modulolabs/pcb/Joystick/Joystick.csv

Qty | Value | Device | Package | Parts | Description | BOM | NOBOM | PARTNUM | VALUE
1 | .1uF | CAPACITOR-.1UF | 0603 | C1 | Capacitor |  |  | C0603C104K5RACTU | .1uF
1 | 1KΩ | RESISTOR-1KΩ | 0603 | R1 | Resistor |  |  | ERJ-3EKF1001V | 1KΩ
1 | ATTINY48/88-TQFP | ATTINY48/88-TQFP | TQFP-32 | U1 |  |  |  | ATTINY48-AUR
1 | DEVICE-PCB | DEVICE-PCB | DEVICE-PCB | PCB1 | Modulo Footprint |  | 1 | Joystick PCB
1 | HEADER-1X4-AMPMODU | HEADER-1X4-AMPMODU | AMPMODU-4P | JP1 |  |  |  | 147733-3
1 | JOYSTICK | JOYSTICK | JOYSTICK | U2 | Thumb Joystick |  |  | Joystick
1 | LED-1206-REV | LED-1206-REV | LED-1206-REV | LED1 | LED |  |  | LTST-C230TBKT
