modulolabs/pcb/Programmer/Programmer.brd

## EAGLE design Programmer/Programmer.brd (2015-08-15)

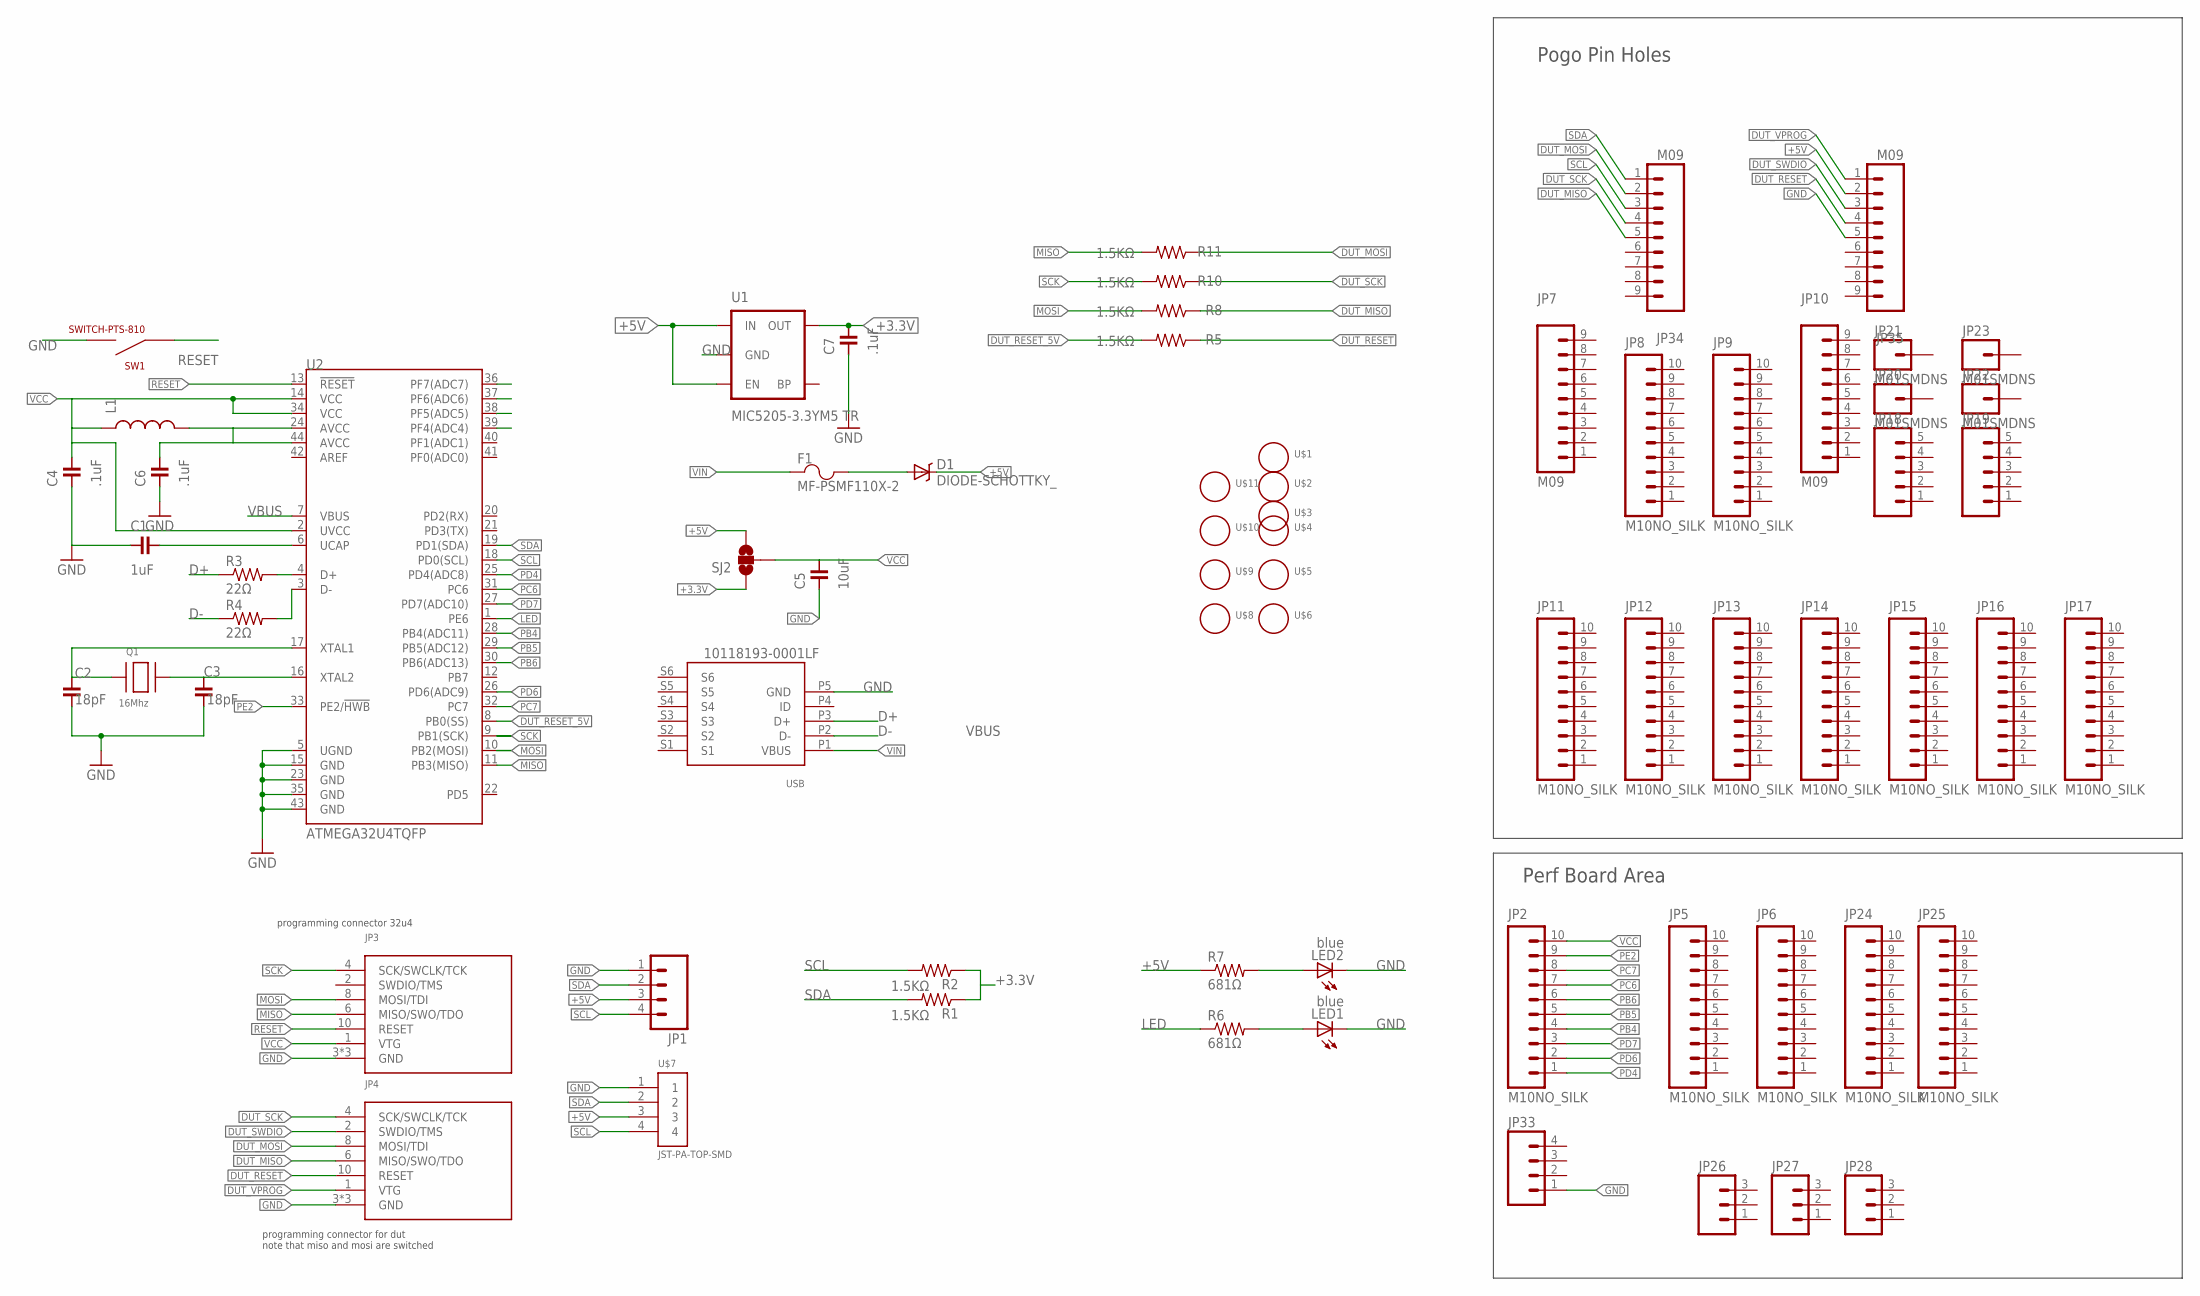
[picture p32: schematic Programmer.sch]

Parts:
C1: 1uF; 0603
C2, C3: 18pF; 0603
C4, C6, C7: .1uF; 0603
C5: 10uF; 0603
D1: DIODE-SCHOTTKY_; SMA-DIODE
F1: MF-PSMF110X-2; 0805; PARTNUM MF-PSFM110X-2
JP1: M04LOCK; 1X04_LOCK
JP2, JP5, JP6, JP8, JP9, JP11, JP12, JP13, JP14, JP15, JP16, JP17, JP24, JP25: M10NO_SILK; 1X10_NO_SILK
JP3, JP4: ICSP; 2X5-.05
JP7, JP10, JP34, JP35: M09; 1X09
JP18, JP19: M05NO_SILK; 1X05_NO_SILK
JP20, JP21, JP22, JP23: M01SMDNS; 1X01NS
JP26, JP27, JP28: M031X03_NO_SILK; 1X03_NO_SILK
JP33: M041X04_NO_SILK; 1X04_NO_SILK
L1: INDUCTOR0805; 0805
LED1, LED2: blue; 0805-LED
Q1: 16Mhz; NX3225; PARTNUM CX3225GB16000D0HEQCC
R1, R2, R5, R8, R10, R11: 1.5KΩ; 0603
R3, R4: 22Ω; 0603
R6, R7: 681Ω; 0603
SJ2: SOLDERJUMPER_2WAYPASTE1&2; SJ_3_PASTE1&2
SW1: SWITCH-PTS-810; TACT-SWITCH-PTS-810
U1: MIC5205-3.3YM5 TR; SOT23-5; PARTNUM MIC5205-3.3YM5 TR
U2: ATMEGA32U4TQFP; SPARKFUN-DIGITALIC_TQFP44; PARTNUM ATMEGA32U4TQFP
U3: USBFCI-MICROB; USB-MICROB-FCI; PARTNUM 10118193-0001LF
U$1, U$2, U$3, U$4, U$5, U$6, U$8, U$9, U$10, U$11: HOLE#2; HOLE-#2
U$7: JST-PA-TOP-SMD

Connections:
+3.3V: C7.1, R1.1, R2.1, SJ2.1, U1.5 (OUT)
+5V: D1.C, JP1.3, JP35.2, R7.1, SJ2.3, U1.1 (IN), U1.3 (EN), U$7.3
D+: R3.1, U3.P3 (D+)
D-: R4.1, U3.P2 (D-)
DUT_MISO: JP4.6 (MISO/SWO/TDO), JP34.5, R8.1
DUT_MOSI: JP4.8 (MOSI/TDI), JP34.2, R11.1
DUT_RESET: JP4.10 (RESET), JP35.4, R5.1
DUT_RESET_5V: R5.2, U2.8 (PB0(SS))
DUT_SCK: JP4.4 (SCK/SWCLK/TCK), JP34.4, R10.1
DUT_SWDIO: JP4.2 (SWDIO/TMS), JP35.3
DUT_VPROG: JP4.1 (VTG), JP35.1
GND: C1.2, C2.2, C3.2, C4.2, C5.2, C6.2, C7.2, JP1.1, JP3.3 (GND), JP3.5 (GND), JP3.9 (GND), JP4.3 (GND), JP4.5 (GND), JP4.9 (GND), JP33.1, JP35.5, LED1.C, LED2.C, SW1.P$3 (NEG1), SW1.P$4 (NEG1), U1.2 (GND), U2.5 (UGND), U2.15 (GND), U2.23 (GND), U2.35 (GND), U2.43 (GND), U3.P5 (GND), U$7.1
LED: R6.1, U2.1 (PE6)
MISO: JP3.6 (MISO/SWO/TDO), R11.2, U2.11 (PB3(MISO))
MOSI: JP3.8 (MOSI/TDI), R8.2, U2.10 (PB2(MOSI))
unnamed: C1.1, U2.6 (UCAP)
unnamed: C6.1, L1.2, U2.24 (AVCC), U2.44 (AVCC)
unnamed: C3.1, Q1.3 (X2), U2.16 (XTAL2)
unnamed: LED1.A, R6.2
unnamed: R3.2, U2.4 (D+)
unnamed: R4.2, U2.3 (D-)
unnamed: LED2.A, R7.2
unnamed: C2.1, Q1.1 (X1), U2.17 (XTAL1)
PB4: JP2.4, U2.28 (PB4(ADC11))
PB5: JP2.5, U2.29 (PB5(ADC12))
PB6: JP2.6, U2.30 (PB6(ADC13))
PC6: JP2.7, U2.31 (PC6)
PC7: JP2.8, U2.32 (PC7)
PD4: JP2.1, U2.25 (PD4(ADC8))
PD6: JP2.2, U2.26 (PD6(ADC9))
PD7: JP2.3, U2.27 (PD7(ADC10))
PE2: JP2.9, U2.33 (PE2/!HWB)
RESET: JP3.10 (RESET), SW1.P$1 (POS1), SW1.P$2 (POS1), U2.13 (!RESET)
SCK: JP3.4 (SCK/SWCLK/TCK), R10.2, U2.9 (PB1(SCK))
SCL: JP1.4, JP34.3, R2.2, U2.18 (PD0(SCL)), U$7.4
SDA: JP1.2, JP34.1, R1.2, U2.19 (PD1(SDA)), U$7.2
VBUS: D1.A, F1.2, U2.7 (VBUS)
VCC: C4.1, C5.1, JP2.10, JP3.1 (VTG), L1.1, SJ2.2, U2.2 (UVCC), U2.14 (VCC), U2.34 (VCC)
VIN: F1.1, U3.P1 (VBUS)

Notes on the sheet:
programming connector 32u4
programming connector for dut note that miso and mosi are switched
Pogo Pin Holes
Perf Board Area

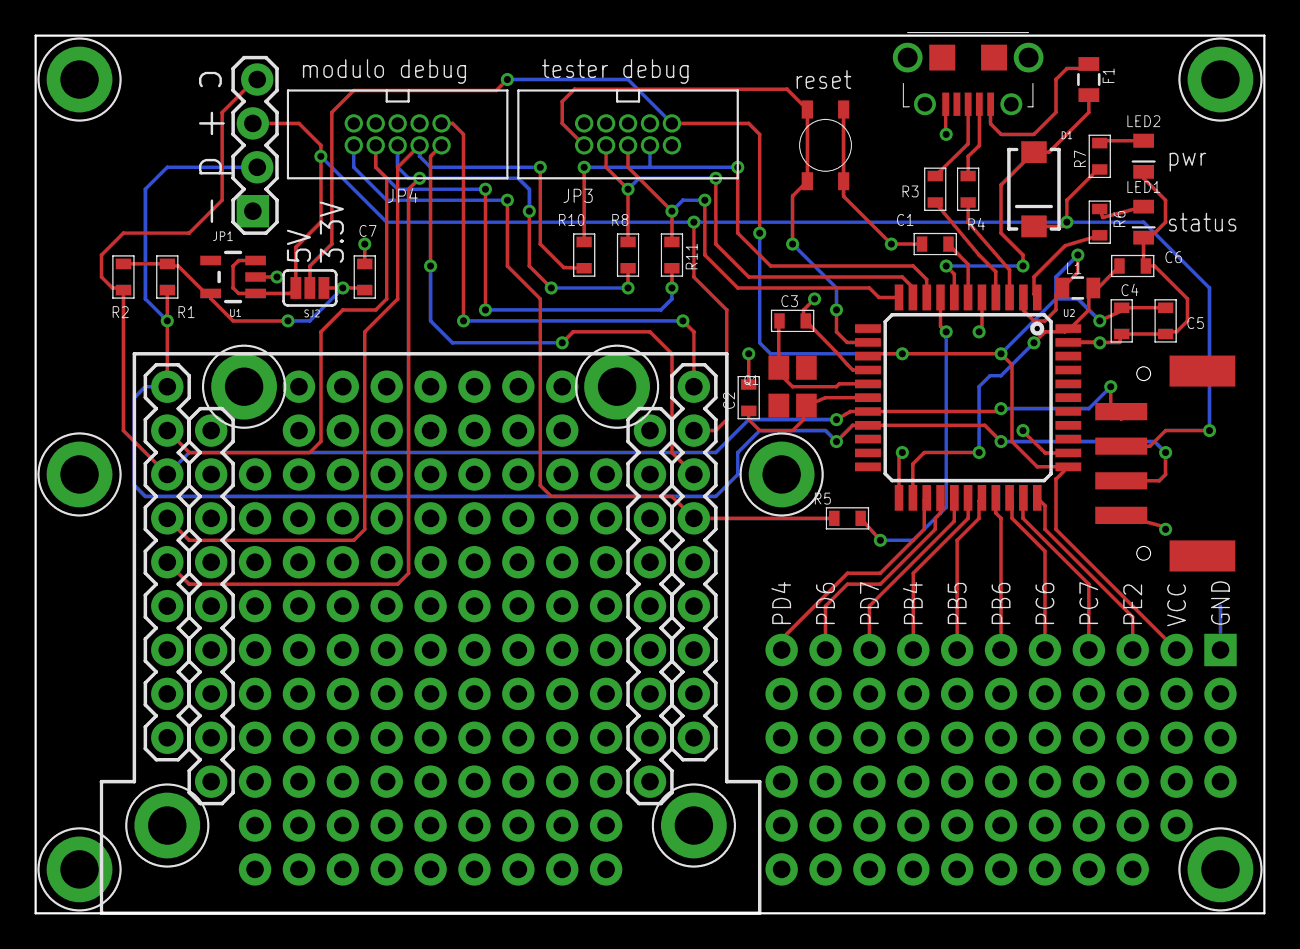
[picture p33: board Programmer.brd from above]

Board: 2 copper layers, 71.1 x 50.8 mm, 70 parts (0 on the bottom side), 39 nets.
