modulolabs/pcb/TempProbeProgrammer/TempProbeProgrammer.brd

## EAGLE design TempProbeProgrammer/TempProbeProgrammer.brd (2015-08-15)

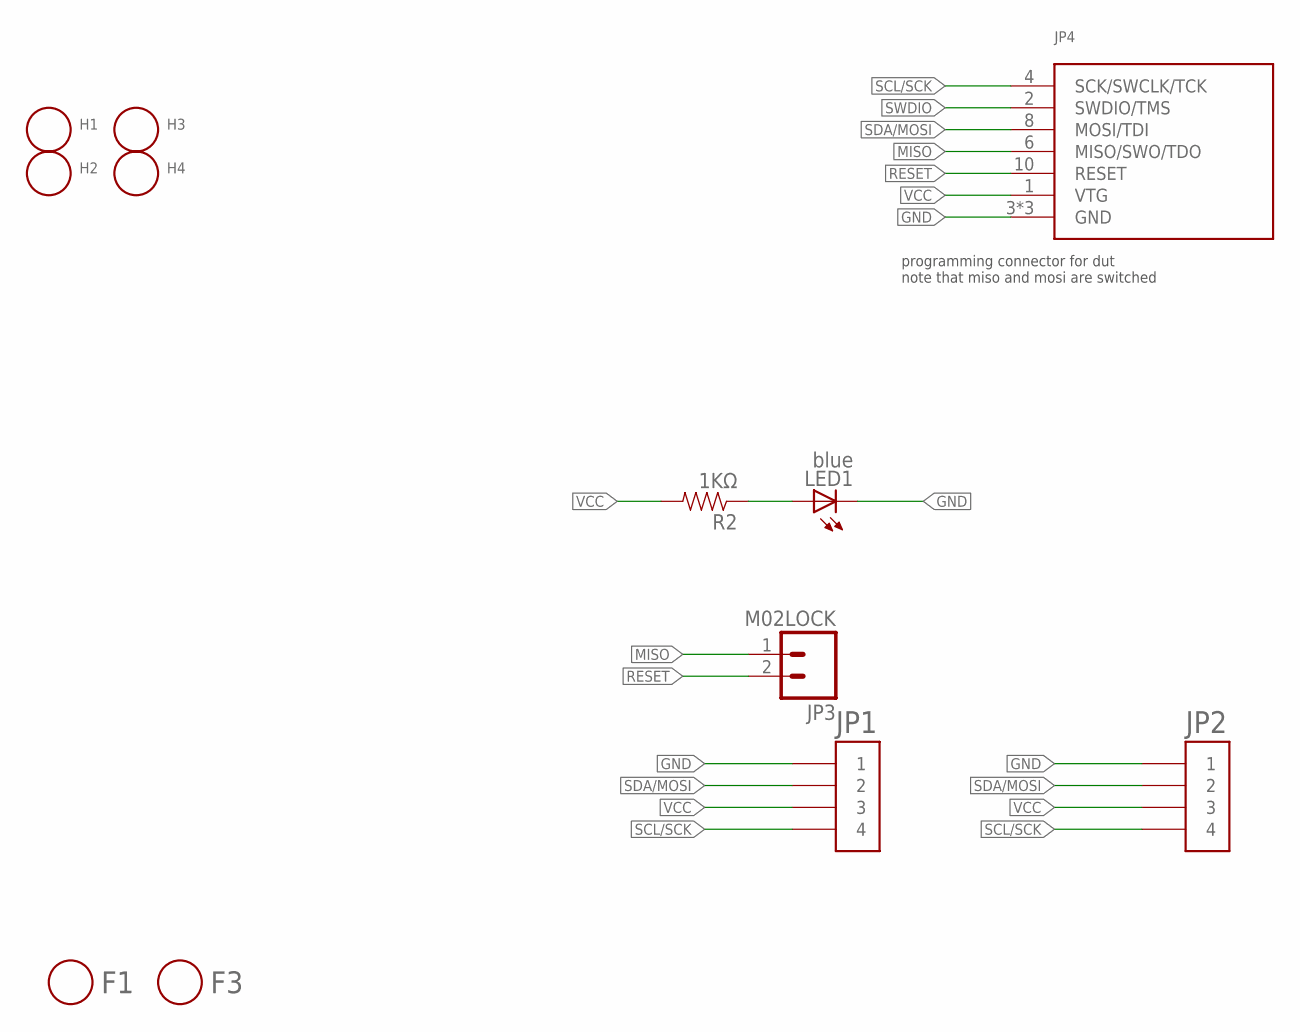
[picture p34: schematic TempProbeProgrammer.sch]

Parts:
F1, F3: FIDUCIAL; FIDUCIAL_1MM
H1, H2, H3, H4: HOLE#4; HOLE-#4
JP1, JP2: HEADER-1X4-JST-PA-SIDE-SMD; JST-PA-SIDE-SMD
JP3: M02LOCK; 1X02_LOCK; PARTNUM EXCLUDE
JP4: ICSP; 2X5-.05
LED1: blue; 0805-LED
R2: 1KΩ; 0603

Connections:
GND: JP1.1, JP2.1, JP4.3 (GND), JP4.5 (GND), JP4.9 (GND), LED1.C
MISO: JP3.1, JP4.6 (MISO/SWO/TDO)
unnamed: LED1.A, R2.1
RESET: JP3.2, JP4.10 (RESET)
SCL/SCK: JP1.4, JP2.4, JP4.4 (SCK/SWCLK/TCK)
SDA/MOSI: JP1.2, JP2.2, JP4.8 (MOSI/TDI)
SWDIO: JP4.2 (SWDIO/TMS)
VCC: JP1.3, JP2.3, JP4.1 (VTG), R2.2

Notes on the sheet:
programming connector for dut note that miso and mosi are switched

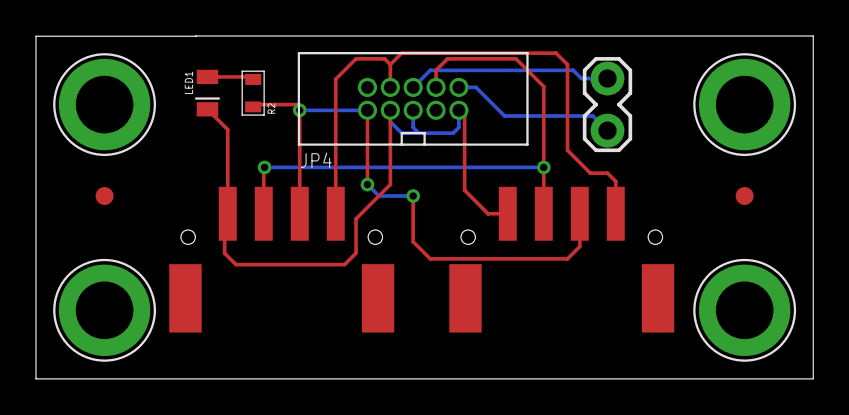
[picture p35: board TempProbeProgrammer.brd from above]

Board: 2 copper layers, 43.2 x 19.1 mm, 12 parts (0 on the bottom side), 7 nets.
