modulolabs/pcb/PerfBoard/PerfBoard.brd

## EAGLE design PerfBoard/PerfBoard.brd (2015-06-10)

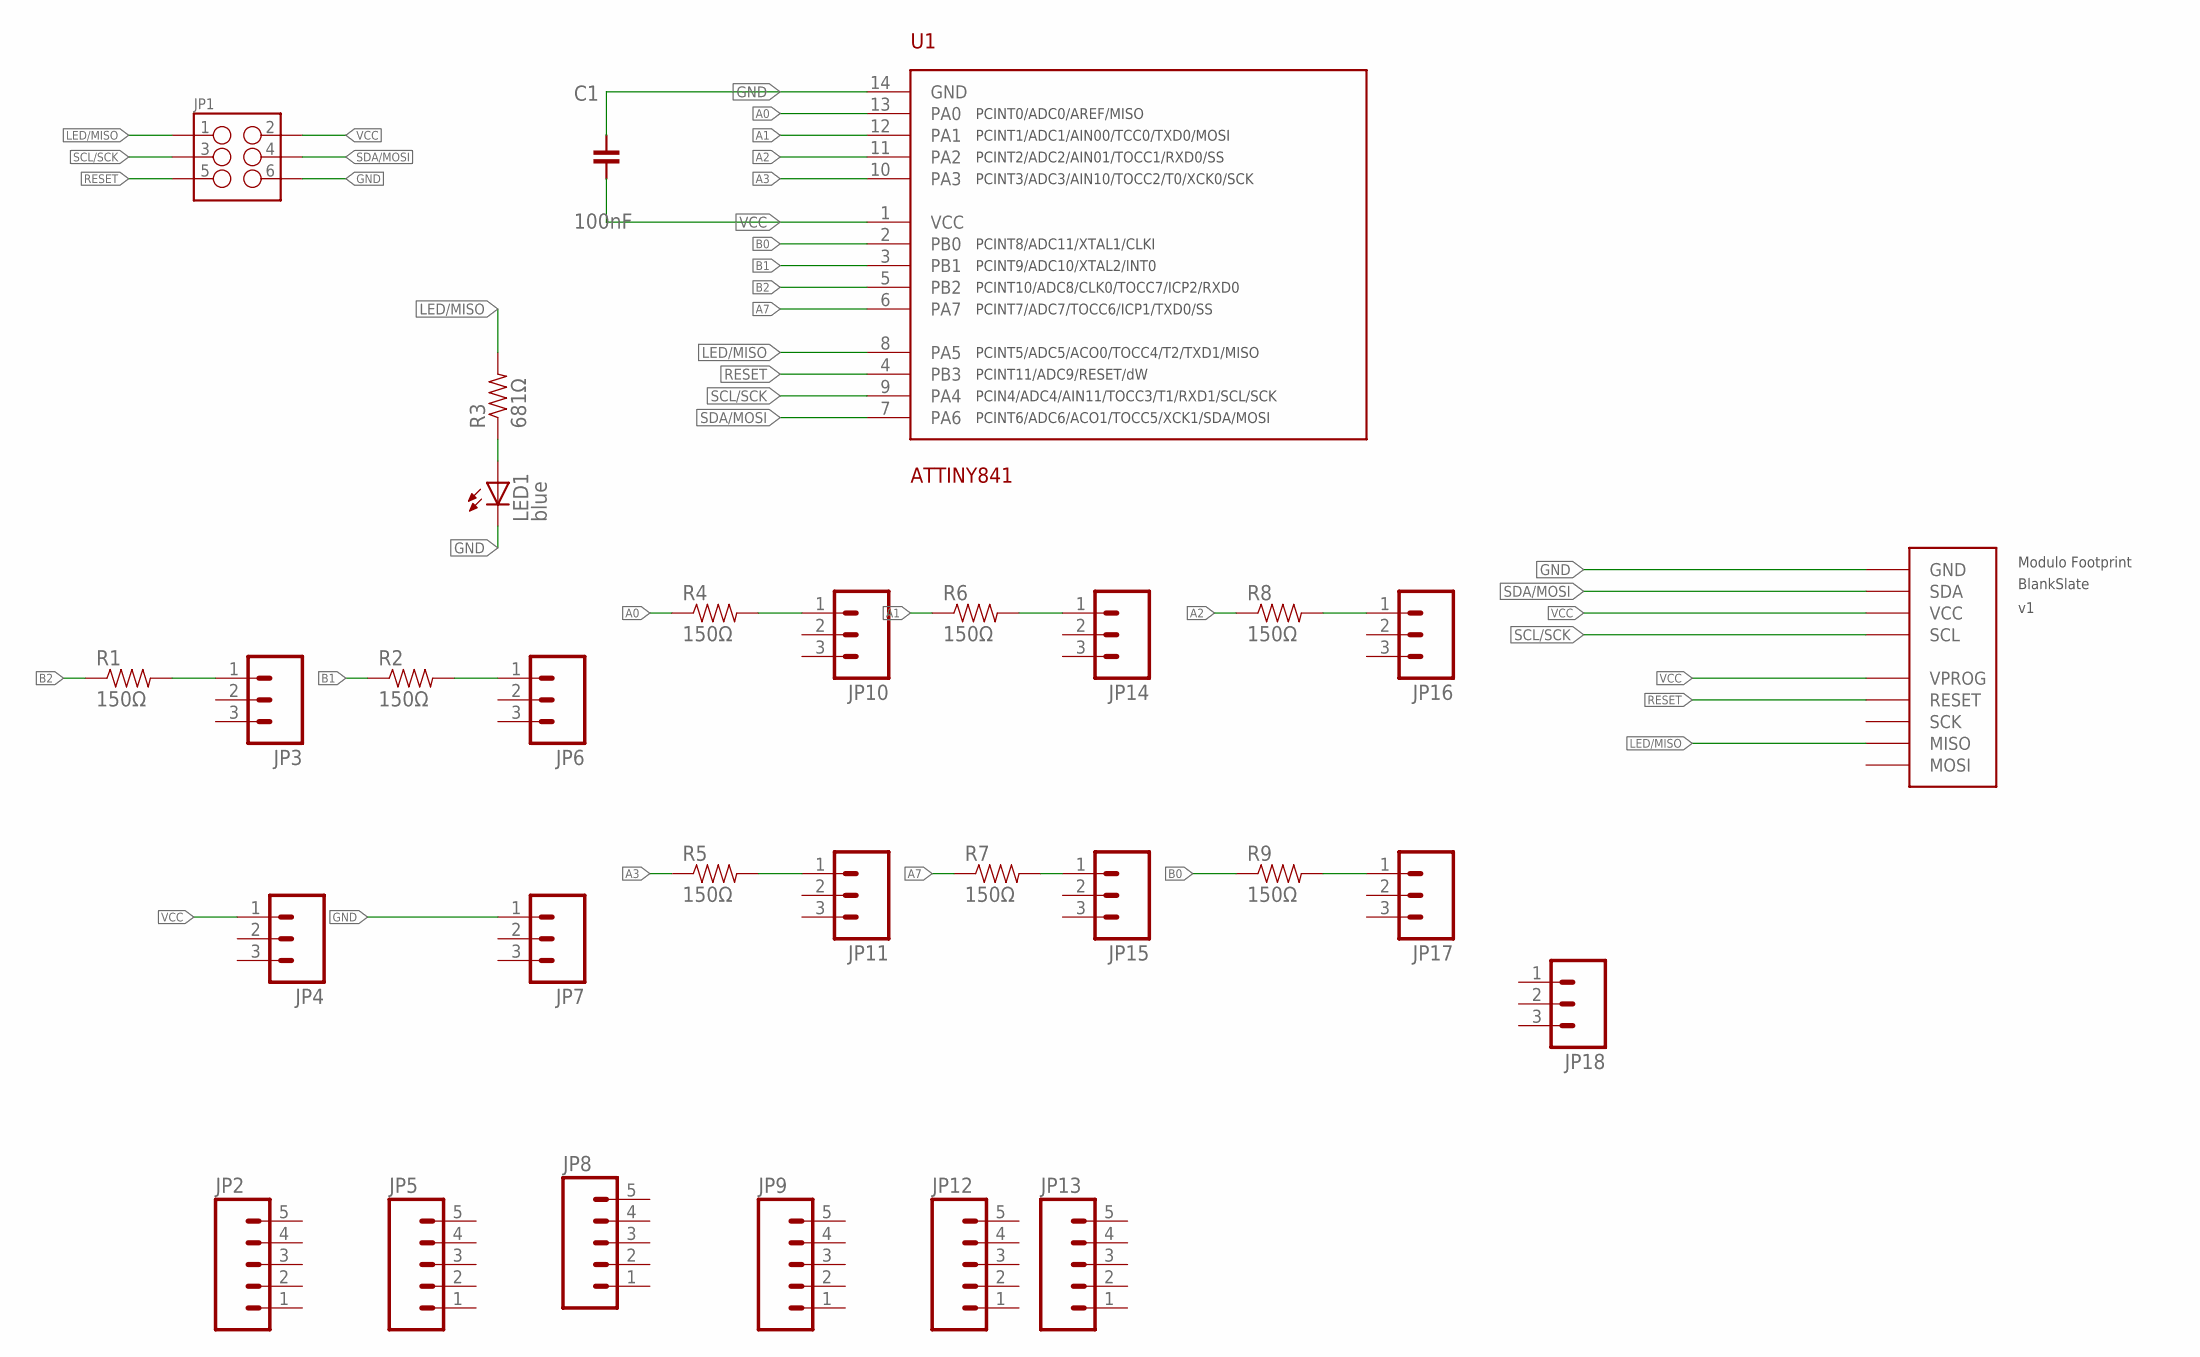
[picture p36: schematic PerfBoard.sch]

Parts:
C1: 100nF; 0603
JP1: M03X2; 2X3_SMD
JP2, JP5, JP8, JP9, JP12, JP13: M05NO_SILK; 1X05_NO_SILK
JP3, JP4, JP6, JP7, JP10, JP11, JP14, JP15, JP16, JP17, JP18: M031X03_NO_SILK; 1X03_NO_SILK
LED1: blue; 0805-LED
PCB1: EXCLUDE; FOOTPRINT2
R1, R2, R4, R5, R6, R7, R8, R9: 150Ω; 0603
R3: 681Ω; 0603
U1: ATTINY841; SOIC-14

Connections:
A0: R4.1, U1.13 (PA0)
A1: R6.1, U1.12 (PA1)
A2: R8.1, U1.11 (PA2)
A3: R5.1, U1.10 (PA3)
A7: R7.1, U1.6 (PA7)
B0: R9.1, U1.2 (PB0)
B1: R2.1, U1.3 (PB1)
B2: R1.1, U1.5 (PB2)
GND: C1.1, JP1.6, JP7.1, LED1.C, PCB1.BUS0 (GND), U1.14 (GND)
LED/MISO: JP1.1, PCB1.PROG3 (MISO), R3.2, U1.8 (PA5)
unnamed: LED1.A, R3.1
unnamed: JP3.1, R1.2
unnamed: JP6.1, R2.2
unnamed: JP10.1, R4.2
unnamed: JP11.1, R5.2
unnamed: JP15.1, R7.2
unnamed: JP14.1, R6.2
unnamed: JP16.1, R8.2
unnamed: JP17.1, R9.2
RESET: JP1.5, PCB1.PROG1 (RESET), U1.4 (PB3)
SCL/SCK: JP1.3, PCB1.BUS3 (SCL), U1.9 (PA4)
SDA/MOSI: JP1.4, PCB1.BUS1 (SDA), U1.7 (PA6)
VCC: C1.2, JP1.2, JP4.1, PCB1.BUS2 (VCC), PCB1.PROG0 (VPROG), U1.1 (VCC)

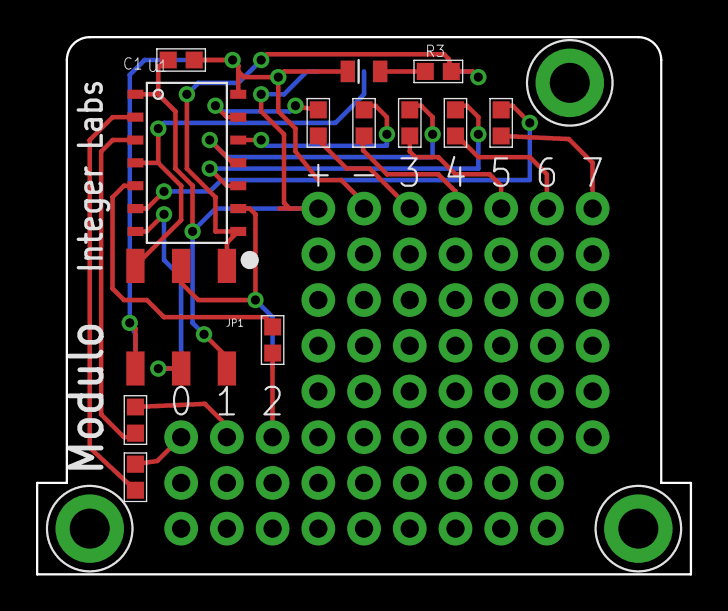
[picture p37: board PerfBoard.brd from above]

Board: 2 copper layers, 36.3 x 29.8 mm, 31 parts (0 on the bottom side), 23 nets.
