modulolabs/pcb/GPIO/GPIO.brd

## EAGLE design GPIO/GPIO.brd (2015-04-02)

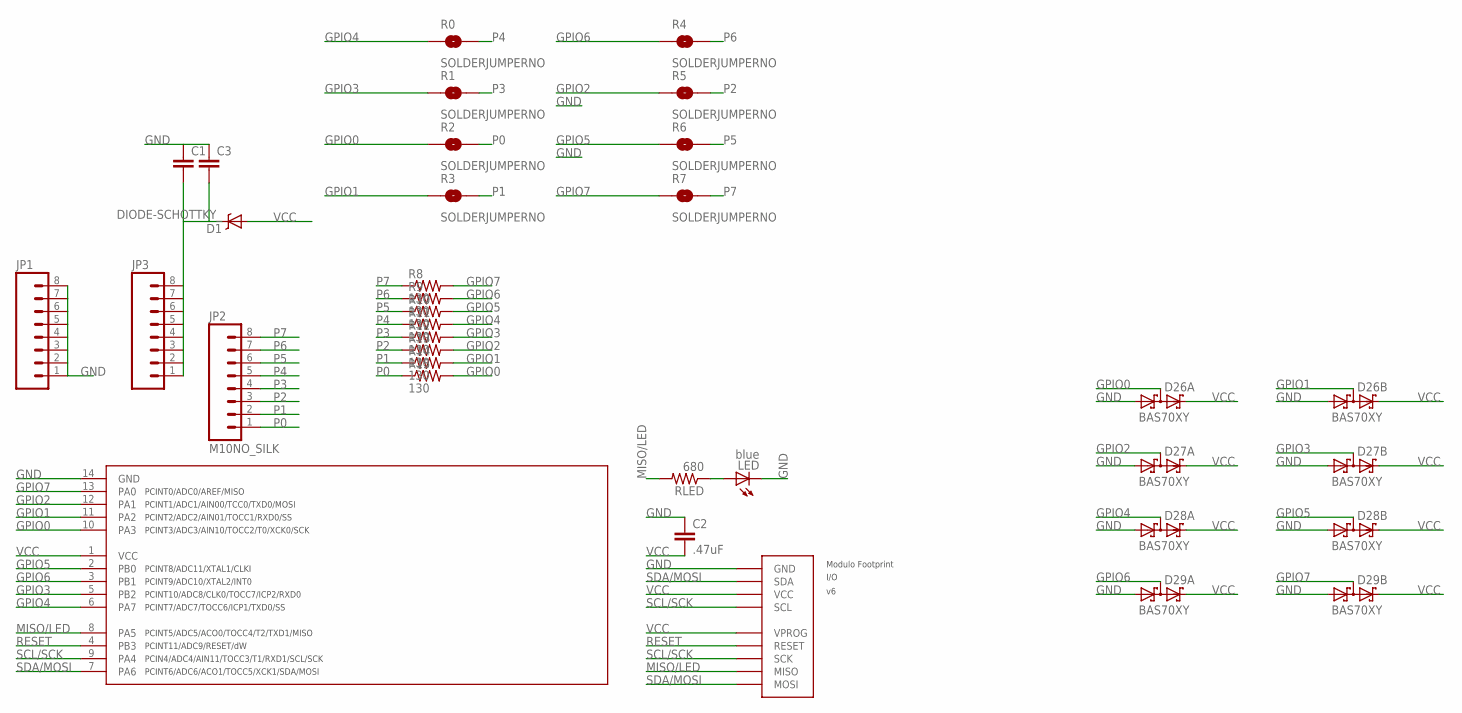
[picture p38: schematic GPIO.sch]

Parts:
C1, C3: CAP1206; 1206
C2: .47uF; 0805
D1: DIODE-SCHOTTKY_; SMA-DIODE
D26, D27, D28, D29: BAS70XY; SOT363_PHILIPS
JP1, JP3: M08NO_SILK; 1X08_NO_SILK
JP2: M10NO_SILK; 1X08_NO_SILK
LED: blue; CHIPLED_0805
R0, R1, R2, R3, R4, R5, R6, R7: SOLDERJUMPERNO; SJ_2S-NO
R8, R9, R10, R11, R12, R13, R14, R15: 130; 0805
RLED: 680; 0805
U$3: TINY841; SOIC14
U$4: FOOTPRINTFOOTPRINT-2; FOOTPRINT2

Connections:
GND: C1.1, C2.1, C3.1, D26.1 (A1), D26.4 (A1), D27.1 (A1), D27.4 (A1), D28.1 (A1), D28.4 (A1), D29.1 (A1), D29.4 (A1), JP1.1, JP1.2, JP1.3, JP1.4, JP1.5, JP1.6, JP1.7, JP1.8, LED.C, U$3.14 (GND), U$4.BUS0 (GND)
GPIO0: D26.6 (C1A2), R2.1, R15.2, U$3.10 (PA3)
GPIO1: D26.3 (C1A2), R3.1, R14.2, U$3.11 (PA2)
GPIO2: D27.6 (C1A2), R5.1, R13.2, U$3.12 (PA1)
GPIO3: D27.3 (C1A2), R1.1, R12.2, U$3.5 (PB2)
GPIO4: D28.6 (C1A2), R0.1, R11.2, U$3.6 (PA7)
GPIO5: D28.3 (C1A2), R6.1, R10.2, U$3.2 (PB0)
GPIO6: D29.6 (C1A2), R4.1, R9.2, U$3.3 (PB1)
GPIO7: D29.3 (C1A2), R7.1, R8.2, U$3.13 (PA0)
MISO/LED: RLED.2, U$3.8 (PA5), U$4.PROG3 (MISO)
unnamed: LED.A, RLED.1
P0: JP2.1, R2.2, R15.1
P1: JP2.2, R3.2, R14.1
P2: JP2.3, R5.2, R13.1
P3: JP2.4, R1.2, R12.1
P4: JP2.5, R0.2, R11.1
P5: JP2.6, R6.2, R10.1
P6: JP2.7, R4.2, R9.1
P7: JP2.8, R7.2, R8.1
RESET: U$3.4 (PB3), U$4.PROG1 (RESET)
SCL/SCK: U$3.9 (PA4), U$4.BUS3 (SCL), U$4.PROG2 (SCK)
SDA/MOSI: U$3.7 (PA6), U$4.BUS1 (SDA), U$4.PROG4 (MOSI)
VCC: C2.2, D1.A, D26.2 (C2), D26.5 (C2), D27.2 (C2), D27.5 (C2), D28.2 (C2), D28.5 (C2), D29.2 (C2), D29.5 (C2), U$3.1 (VCC), U$4.BUS2 (VCC), U$4.PROG0 (VPROG)
VOUT: C1.2, C3.2, D1.C, JP3.1, JP3.2, JP3.3, JP3.4, JP3.5, JP3.6, JP3.7, JP3.8

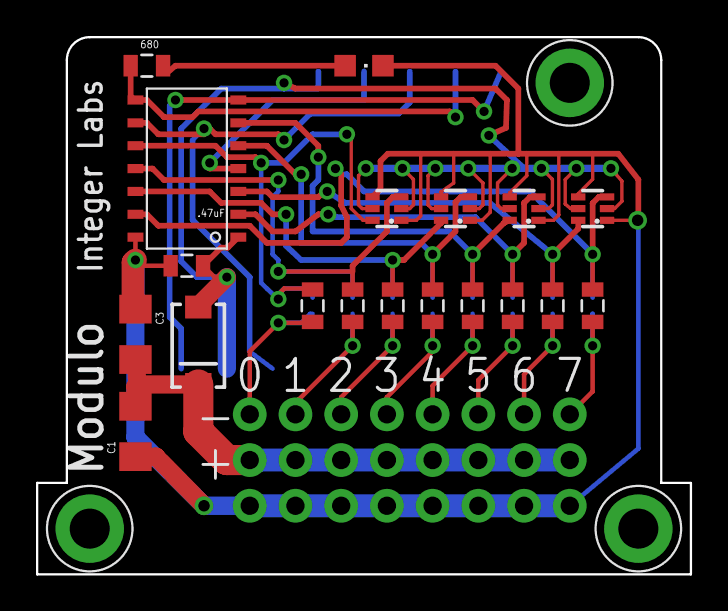
[picture p39: board GPIO.brd from above]

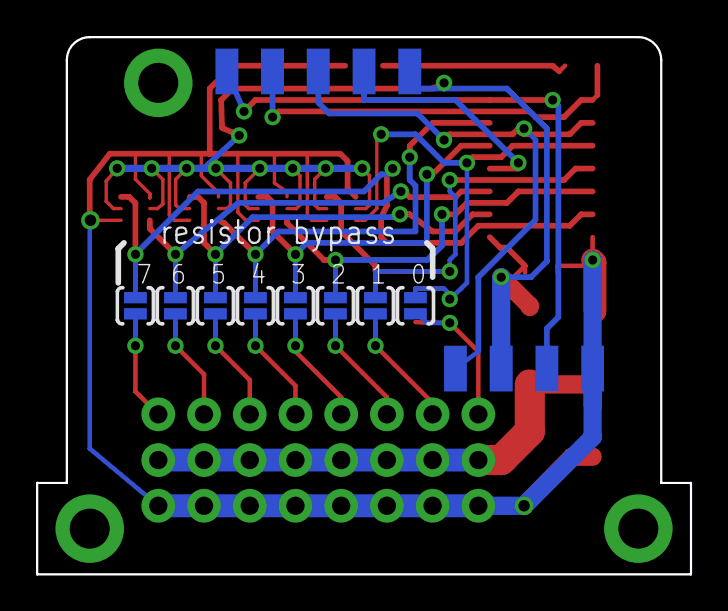
[picture p40: board GPIO.brd from below]

Board: 2 copper layers, 36.3 x 29.8 mm, 31 parts (8 on the bottom side), 24 nets.
