modulolabs/pcb/RPi/RPi.brd

## EAGLE design RPi/RPi.brd (2015-04-02)

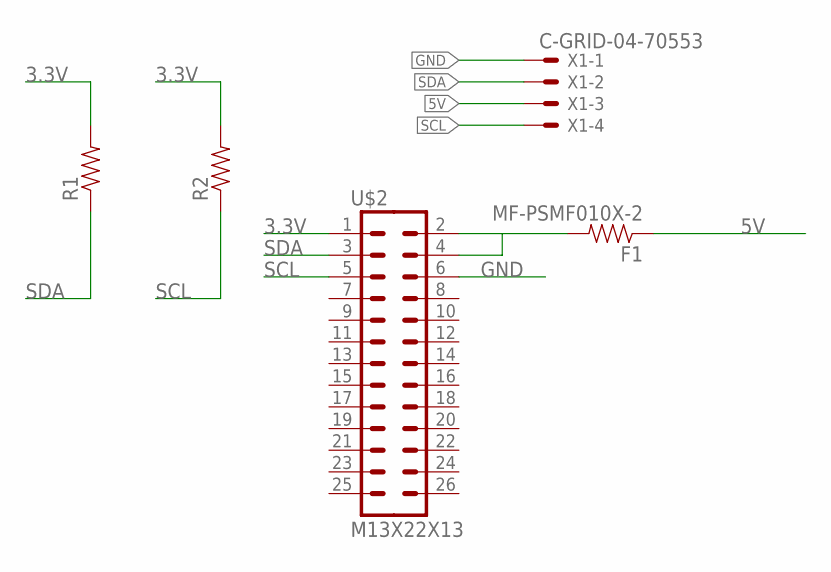
[picture p41: schematic RPi.sch]

Parts:
F1: MF-PSMF010X-2; 0805
R1, R2: RESISTOR0805-RES; 0805
U$2: M13X22X13; 2X13
X1: C-GRID-04-70553; 70553-04

Connections:
3.3V: R1.2, R2.2, U$2.1
5V: F1.1, X1.3
GND: U$2.6, X1.1
unnamed: F1.2, U$2.2, U$2.4
SCL: R2.1, U$2.5, X1.4
SDA: R1.1, U$2.3, X1.2

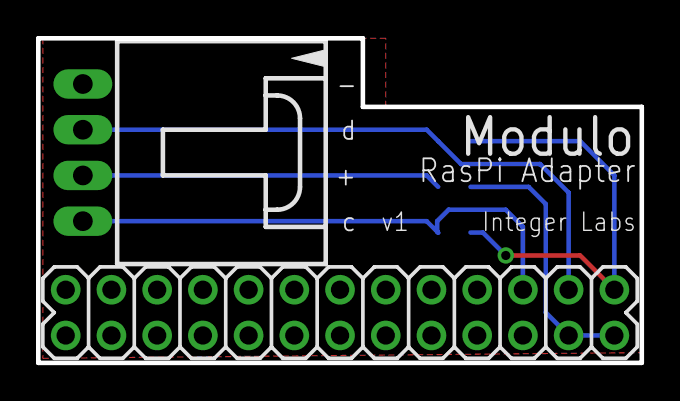
[picture p42: board RPi.brd from above]

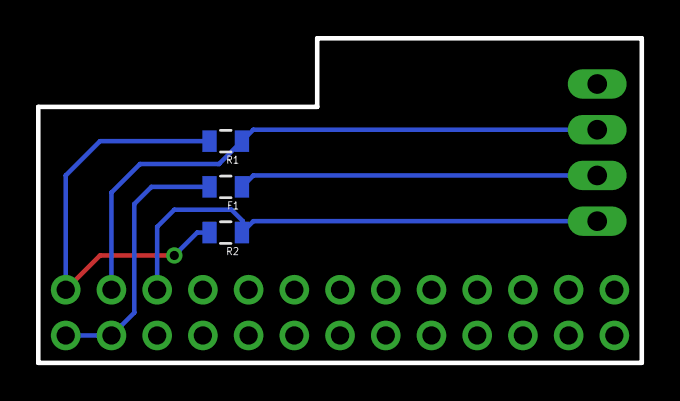
[picture p43: board RPi.brd from below]

Board: 2 copper layers, 33.5 x 18.0 mm, 5 parts (3 on the bottom side), 6 nets.
