modulolabs/pcb/OLED/OLED.brd

## EAGLE design OLED/OLED.brd (2015-04-02)

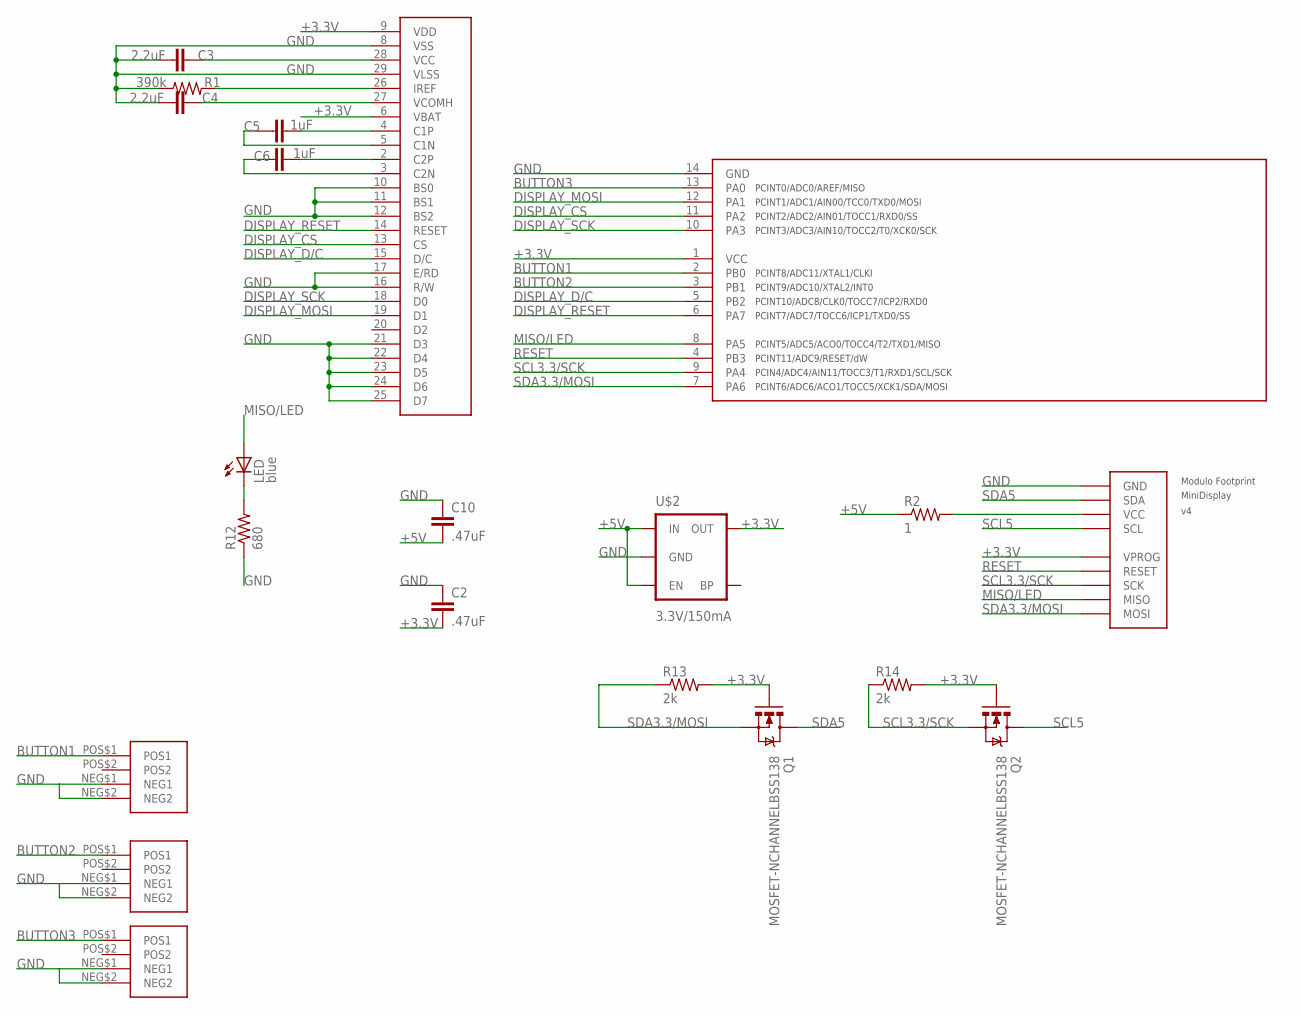
[picture p44: schematic OLED.sch]

Parts:
C2, C10: .47uF; 0805
C3, C4: 2.2uF; 0805
C5, C6: 1uF; 0805
LED: blue; CHIP-LED0805
Q1, Q2: MOSFET-NCHANNELBSS138; SOT23
R1: 390k; 0603-RES
R2: 1; 0805
R12: 680; 0805
R13, R14: 2k; 0805
U$1: OLEDREVERSE; FPC-30-REVERSE
U$2: 3.3V/150mA; SOT23-5
U$3: TINY841; SOIC14
U$4: FOOTPRINTFOOTPRINT-2; FOOTPRINT2
U$5, U$6, U$7: TACT-SWITCHBOURNS-7914J; BOURNS-7914J

Connections:
+3.3V: C2.2, Q1.1 (G), Q2.1 (G), R13.2, R14.2, U$1.6 (VBAT), U$1.9 (VDD), U$2.5 (OUT), U$3.1 (VCC), U$4.PROG0 (VPROG)
+5V: C10.2, R2.1, U$2.1 (IN), U$2.3 (EN)
BUTTON1: U$3.2 (PB0), U$5.POS$1 (POS1)
BUTTON2: U$3.3 (PB1), U$6.POS$1 (POS1)
BUTTON3: U$3.13 (PA0), U$7.POS$1 (POS1)
DISPLAY_CS: U$1.13 (CS), U$3.11 (PA2)
DISPLAY_D/C: U$1.15 (D/C), U$3.5 (PB2)
DISPLAY_MOSI: U$1.19 (D1), U$3.12 (PA1)
DISPLAY_RESET: U$1.14 (RESET), U$3.6 (PA7)
DISPLAY_SCK: U$1.18 (D0), U$3.10 (PA3)
GND: C2.1, C3.2, C4.2, C10.1, R1.1, R12.1, U$1.8 (VSS), U$1.10 (BS0), U$1.11 (BS1), U$1.12 (BS2), U$1.16 (R/W), U$1.17 (E/RD), U$1.21 (D3), U$1.22 (D4), U$1.23 (D5), U$1.24 (D6), U$1.25 (D7), U$1.29 (VLSS), U$2.2 (GND), U$3.14 (GND), U$4.BUS0 (GND), U$5.NEG$1 (NEG1), U$5.NEG$2 (NEG2), U$6.NEG$1 (NEG1), U$6.NEG$2 (NEG2), U$7.NEG$1 (NEG1), U$7.NEG$2 (NEG2)
MISO/LED: LED.A, U$3.8 (PA5), U$4.PROG3 (MISO)
unnamed: R1.2, U$1.26 (IREF)
unnamed: R2.2, U$4.BUS2 (VCC)
unnamed: C3.1, U$1.28 (VCC)
unnamed: C4.1, U$1.27 (VCOMH)
unnamed: LED.C, R12.2
unnamed: C5.2, U$1.4 (C1P)
unnamed: C6.2, U$1.2 (C2P)
unnamed: C5.1, U$1.5 (C1N)
unnamed: C6.1, U$1.3 (C2N)
RESET: U$3.4 (PB3), U$4.PROG1 (RESET)
SCL3.3/SCK: Q2.2 (S), R14.1, U$3.9 (PA4), U$4.PROG2 (SCK)
SCL5: Q2.3 (D), U$4.BUS3 (SCL)
SDA3.3/MOSI: Q1.2 (S), R13.1, U$3.7 (PA6), U$4.PROG4 (MOSI)
SDA5: Q1.3 (D), U$4.BUS1 (SDA)

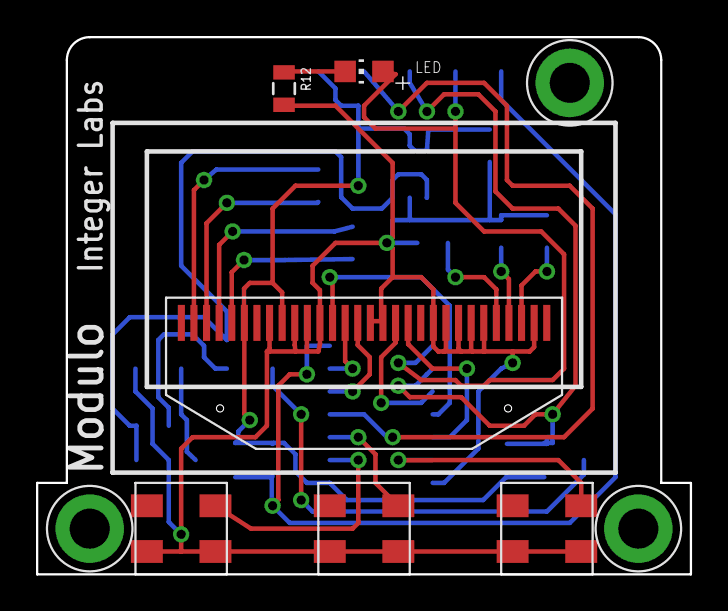
[picture p45: board OLED.brd from above]

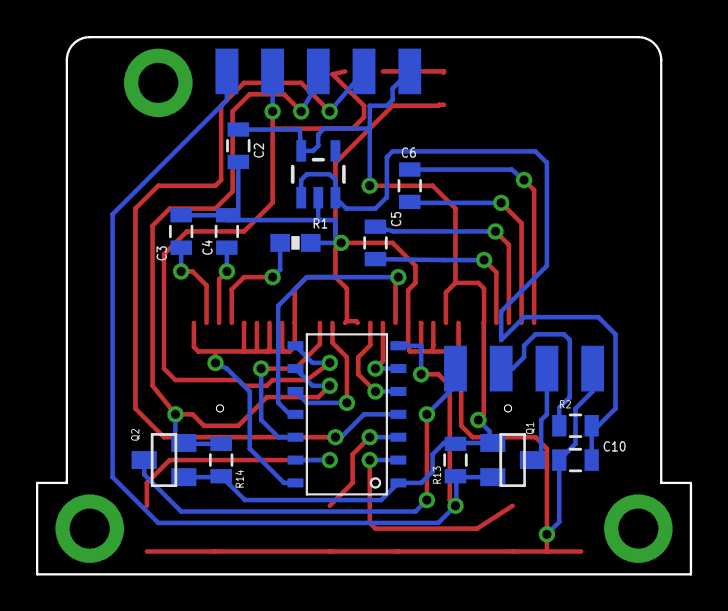
[picture p46: board OLED.brd from below]

Board: 2 copper layers, 36.3 x 29.8 mm, 21 parts (14 on the bottom side), 26 nets.
