modulolabs/pcb/MagKnob/Knob.brd

## EAGLE design MagKnob/Knob.brd (2015-04-02, an earlier design)

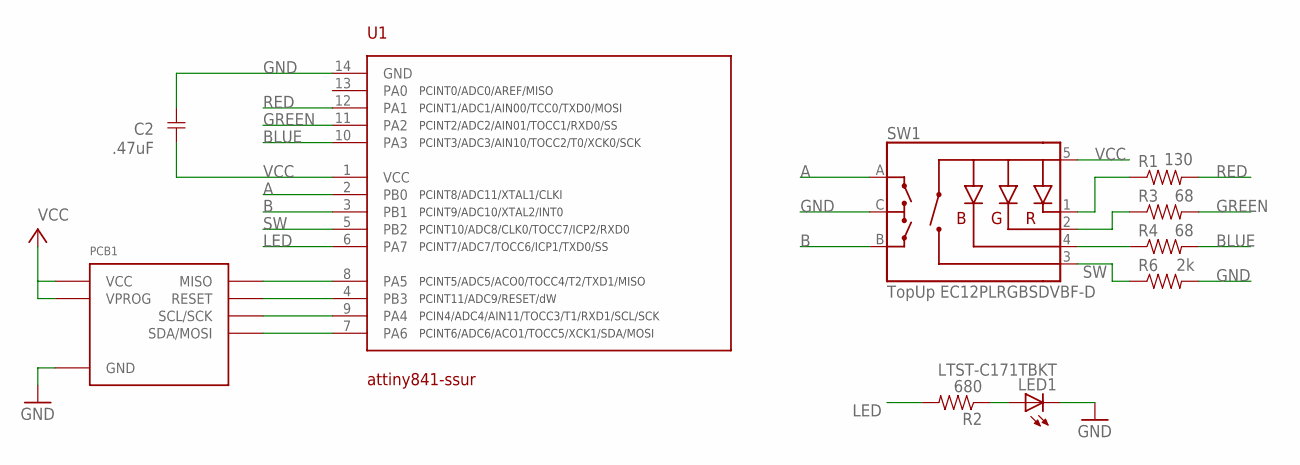
[picture p47: schematic Knob.sch]

Parts:
C2: .47uF; 0805
LED1: LTST-C171TBKT; 0805-LED
PCB1: MAGDEVICE
R1: 130; 0805
R2: 680; 0805
R3, R4: 68; 0805
R6: 2k; 0805
SW1: TopUp EC12PLRGBSDVBF-D; ENCODER_LED_3
U1: attiny841-ssur; SOIC14

Connections:
A: SW1.A, U1.2 (PB0)
B: SW1.B, U1.3 (PB1)
BLUE: R4.2, U1.10 (PA3)
GND: C2.2, LED1.C, PCB1.GNDA (GND), PCB1.GNDB (GND), R6.2, SW1.C, U1.14 (GND)
GREEN: R3.2, U1.11 (PA2)
LED: R2.2, U1.6 (PA7)
MISO: PCB1.MISO, U1.8 (PA5)
unnamed: R1.1, SW1.1 (-R)
unnamed: R3.1, SW1.2 (-G)
unnamed: R4.1, SW1.4 (-B)
unnamed: LED1.A, R2.1
RED: R1.2, U1.12 (PA1)
RESET: PCB1.RESET, U1.4 (PB3)
SCL/SCK: PCB1.SCLA (SCL/SCK), PCB1.SCLB (SCL/SCK), U1.9 (PA4)
SDA/MOSI: PCB1.SDAA (SDA/MOSI), PCB1.SDAB (SDA/MOSI), U1.7 (PA6)
SW: R6.1, SW1.3 (SW), U1.5 (PB2)
VCC: C2.1, PCB1.VCCA (VCC), PCB1.VCCB (VCC), PCB1.VPROG, SW1.5 (+), U1.1 (VCC)

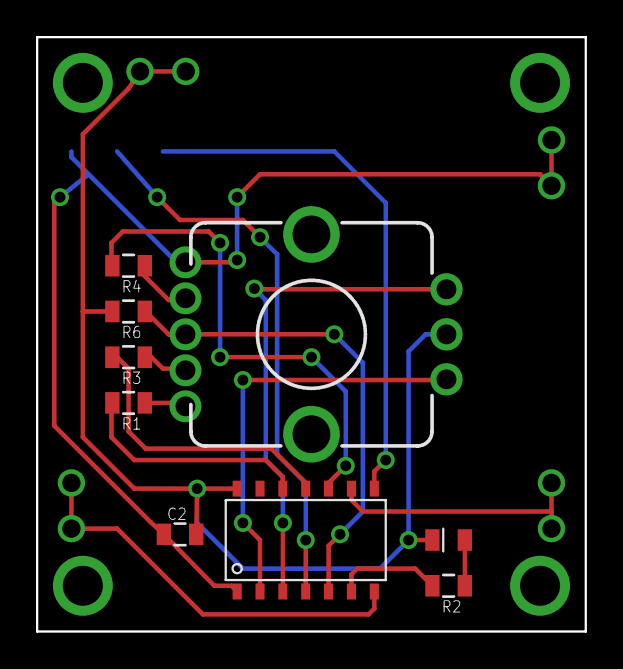
[picture p48: board MagKnob/Knob.brd from above]

Board: 2 copper layers, 30.5 x 33.0 mm, 10 parts (0 on the bottom side), 17 nets.
