modulolabs/pcb/MagController/MagController.brd

## EAGLE design MagController/MagController.brd (2015-04-02)

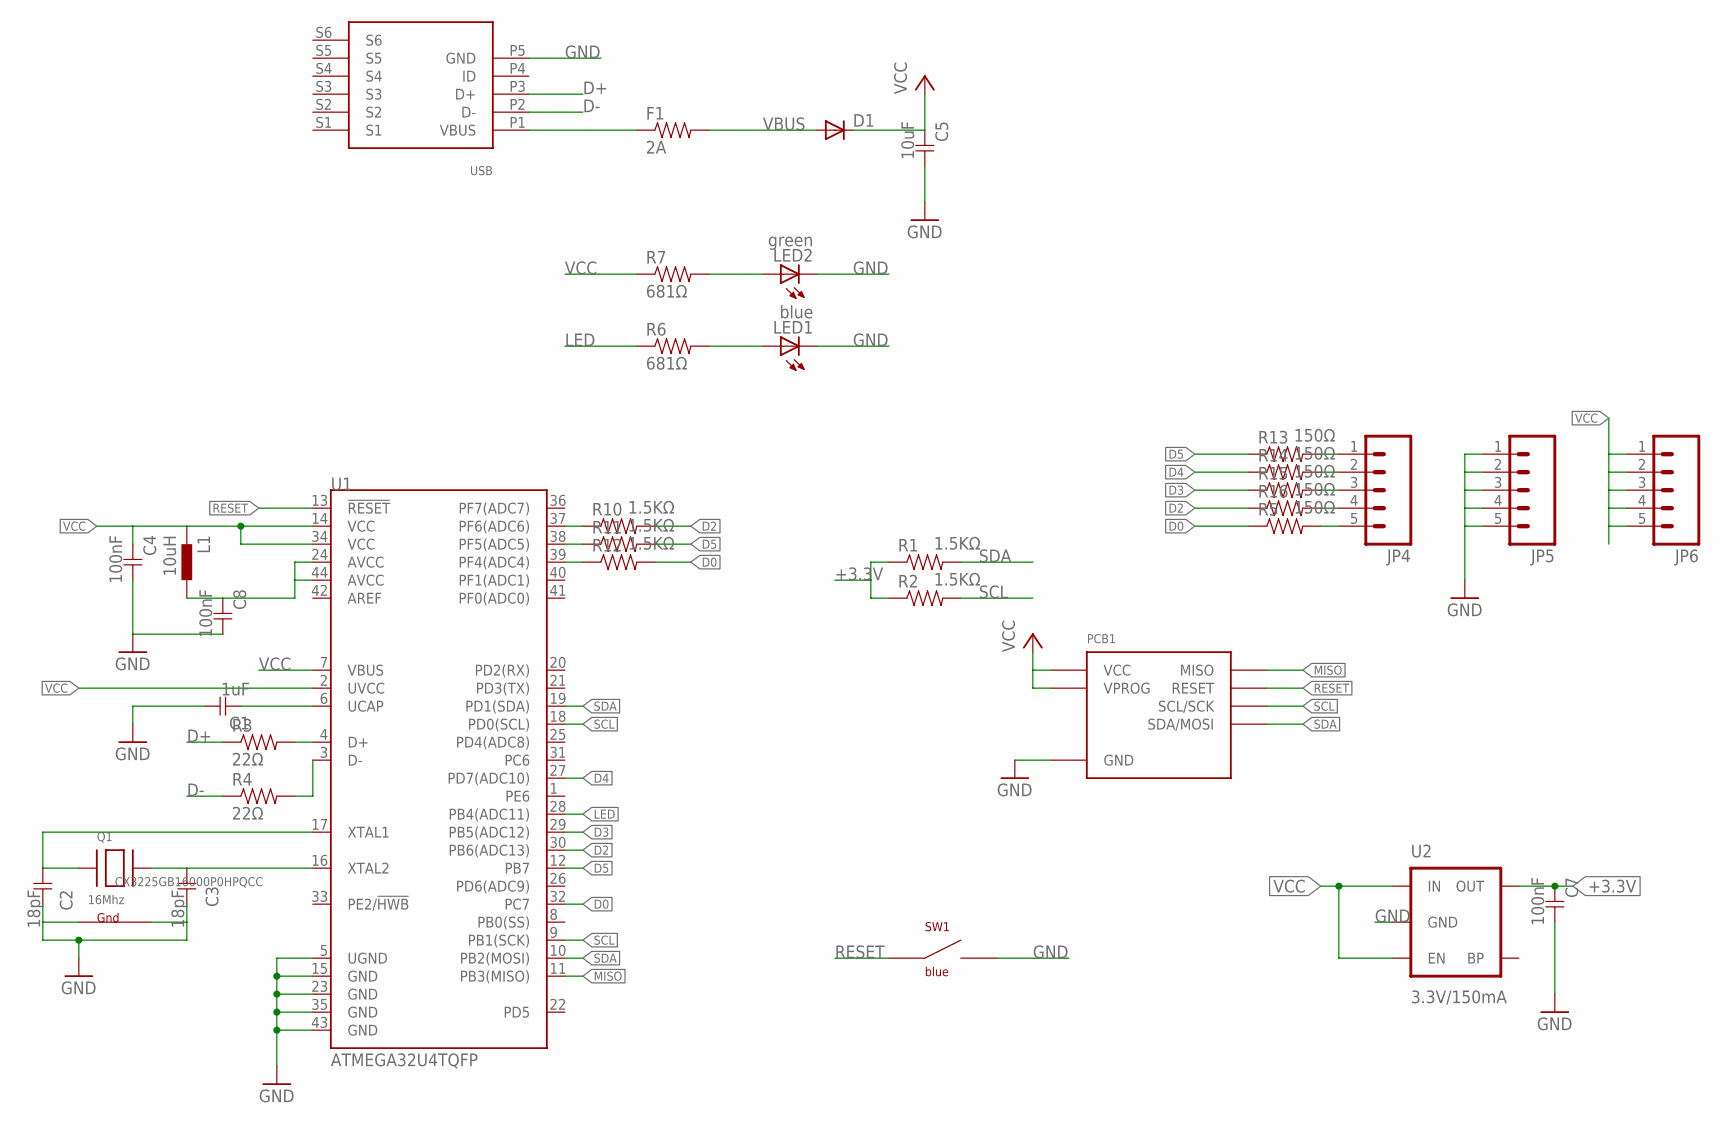
[picture p49: schematic MagController.sch]

Parts:
C1: 1uF; 0603
C2, C3: 18pF; 0603
C4, C7, C8: 100nF; 0603
C5: 10uF; 0603
D1: DIODESMA; SMA-DIODE; PARTNUM SSA33L-E3/61TGICT-ND
F1: 2A; 0603; PARTNUM MF-PSMF110X-2
JP4, JP5, JP6: M05NO_SILK; 1X05_NO_SILK
L1: 10uH; 0603
LED1: blue; 0805-LED
LED2: green; 0805-LED
PCB1: MAGDEVICE
Q1: 16Mhz; NX3225; PARTNUM CX3225GB16000P0HPQCC
R1, R2, R10, R11, R12: 1.5KΩ; 0603
R3, R4: 22Ω; 0603
R5, R13, R14, R15, R16: 150Ω; 0603
R6, R7: 681Ω; 0603
SW1: blue; BOURNS-7914J
U1: ATMEGA32U4TQFP; SPARKFUN-DIGITALIC_TQFP44; PARTNUM ATMEGA32U4-AU
U2: 3.3V/150mA; SOT23-5; PARTNUM MIC5205-3.3YM5 TR
U3: USBFCI-MICROB; USB-MICROB-FCI; PARTNUM 10118194-0001LF

Connections:
+3.3V: C7.1, R1.1, R2.1, U2.5 (OUT)
AVCC: C8.1, L1.2, U1.24 (AVCC), U1.44 (AVCC)
D0: R5.1, R12.2, U1.32 (PC7)
D2: R10.2, R16.1, U1.30 (PB6(ADC13))
D3: R15.1, U1.29 (PB5(ADC12))
D4: R14.1, U1.27 (PD7(ADC10))
D5: R11.2, R13.1, U1.12 (PB7)
D+: R3.1, U3.P3 (D+)
D-: R4.1, U3.P2 (D-)
GND: C1.2, C2.2, C3.2, C4.2, C5.2, C7.2, C8.2, JP5.1, JP5.2, JP5.3, JP5.4, JP5.5, LED1.C, LED2.C, PCB1.GNDA (GND), PCB1.GNDB (GND), Q1.2 (G1), Q1.4 (G2), SW1.NEG$1 (NEG1), SW1.NEG$2 (NEG1), U1.5 (UGND), U1.15 (GND), U1.23 (GND), U1.35 (GND), U1.43 (GND), U2.2 (GND), U3.P5 (GND)
LED: R6.1, U1.28 (PB4(ADC11))
MISO: PCB1.MISO, U1.11 (PB3(MISO))
unnamed: C1.1, U1.6 (UCAP)
unnamed: JP4.1, R13.2
unnamed: F1.1, U3.P1 (VBUS)
unnamed: C3.1, Q1.3 (X2), U1.16 (XTAL2)
unnamed: LED1.A, R6.2
unnamed: R12.1, U1.39 (PF4(ADC4))
unnamed: R11.1, U1.38 (PF5(ADC5))
unnamed: R3.2, U1.4 (D+)
unnamed: R4.2, U1.3 (D-)
unnamed: R10.1, U1.37 (PF6(ADC6))
unnamed: JP4.5, R5.2
unnamed: LED2.A, R7.2
unnamed: JP4.2, R14.2
unnamed: C2.1, Q1.1 (X1), U1.17 (XTAL1)
unnamed: JP4.3, R15.2
unnamed: JP4.4, R16.2
RESET: PCB1.RESET, SW1.POS$1 (POS1), SW1.POS$2 (POS1), U1.13 (!RESET)
SCL: PCB1.SCLA (SCL/SCK), PCB1.SCLB (SCL/SCK), R2.2, U1.9 (PB1(SCK)), U1.18 (PD0(SCL))
SDA: PCB1.SDAA (SDA/MOSI), PCB1.SDAB (SDA/MOSI), R1.2, U1.10 (PB2(MOSI)), U1.19 (PD1(SDA))
VBUS: D1.A, F1.2
VCC: C4.1, C5.1, D1.C, JP6.1, JP6.2, JP6.3, JP6.4, JP6.5, L1.1, PCB1.VCCA (VCC), PCB1.VCCB (VCC), PCB1.VPROG, R7.1, U1.2 (UVCC), U1.7 (VBUS), U1.14 (VCC), U1.34 (VCC), U2.1 (IN), U2.3 (EN)

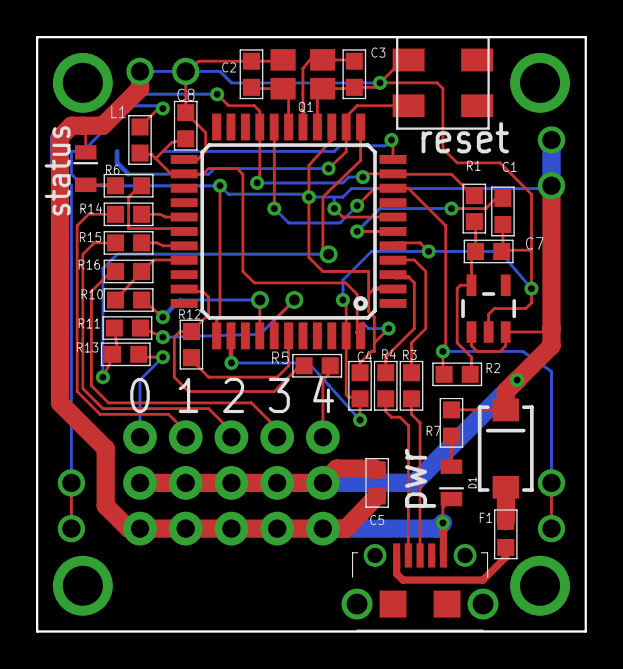
[picture p50: board MagController.brd from above]

Board: 2 copper layers, 30.5 x 33.0 mm, 35 parts (0 on the bottom side), 33 nets.
