modulolabs/pcb/SX1231/SX1231.brd

## EAGLE design SX1231/SX1231.brd (2015-04-02)

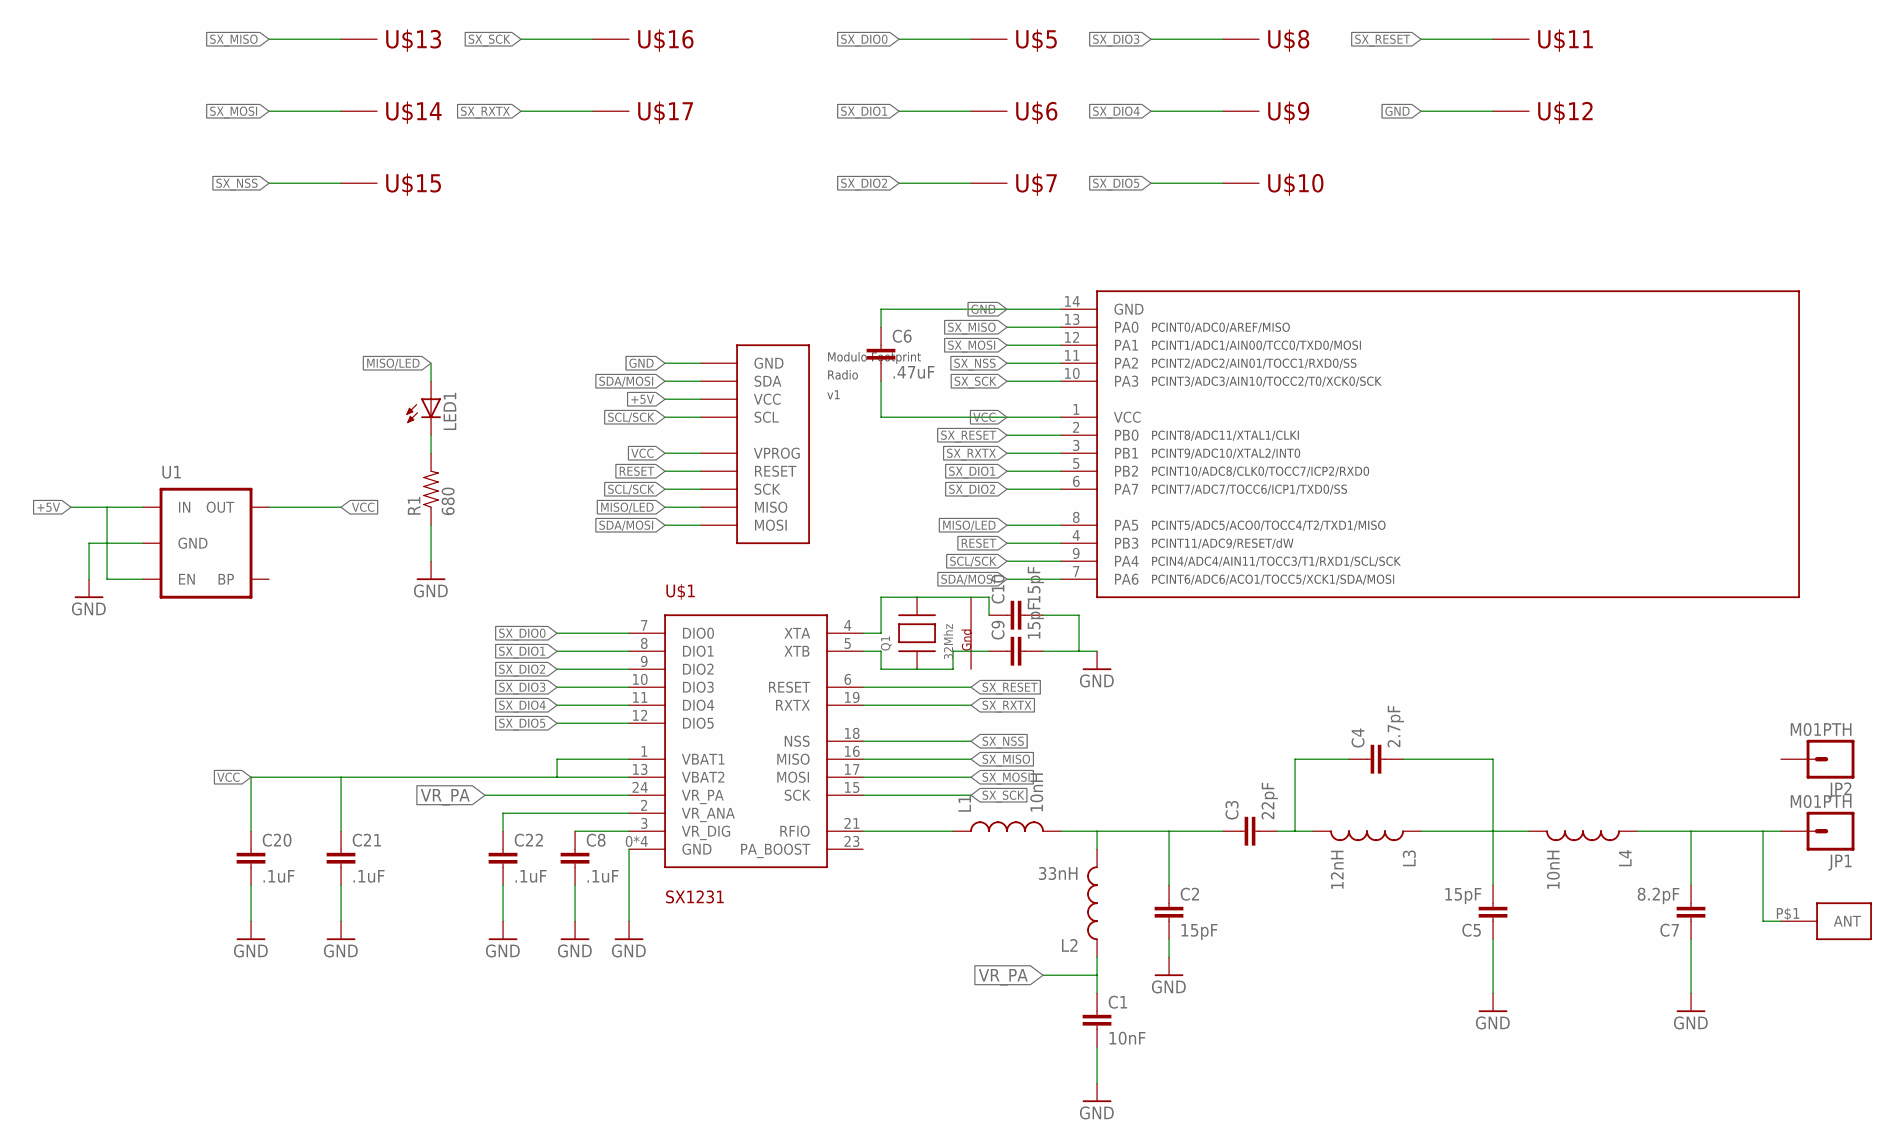
[picture p51: schematic SX1231.sch]

Parts:
C1: 10nF; 0805
C2, C5, C9, C10: 15pF; 0805
C3: 22pF; 0805
C4: 2.7pF; 0805
C6: .47uF; 0805
C7: 8.2pF; 0805
C8, C20, C21, C22: .1uF; 0805
JP1, JP2: M01PTH; 1X01
L1, L4: 10nH; 0805
L2: 33nH; 0805
L3: 12nH; 0805
LED1: LEDCHIP-LED0805; CHIP-LED0805
Q1: 32Mhz; NX3225
R1: 680; 0805
U1: MIC52053.3V; SOT23-5
U$1: SX1231; QFN-24
U$2: FOOTPRINTFOOTPRINT-2; FOOTPRINT2
U$3: TINY841; SOIC14
U$4: ANTENNA; ANT-433-PW-LP
U$5, U$6, U$7, U$8, U$9, U$10, U$11, U$12, U$13, U$14, U$15, U$16, U$17: TESTPOINT

Connections:
+5V: U1.1 (IN), U1.3 (EN), U$2.BUS2 (VCC)
G1: Q1.4 (G1)
G2: Q1.2 (G2)
GND: C1.2, C2.2, C5.1, C6.1, C7.1, C8.2, C9.2, C10.2, C20.2, C21.2, C22.2, R1.1, U1.2 (GND), U$1.0 (GND), U$1.14 (GND), U$1.20 (GND), U$1.22 (GND), U$2.BUS0 (GND), U$3.14 (GND), U$12.P$1
MISO/LED: LED1.A, U$2.PROG3 (MISO), U$3.8 (PA5)
unnamed: C8.1, U$1.3 (VR_DIG)
unnamed: C9.1, Q1.1 (X1), U$1.5 (XTB)
unnamed: C10.1, Q1.3 (X2), U$1.4 (XTA)
unnamed: LED1.C, R1.2
unnamed: C22.1, U$1.2 (VR_ANA)
unnamed: L1.1, U$1.21 (RFIO)
unnamed: C2.1, C3.1, L1.2, L2.2
unnamed: C3.2, C4.1, L3.2
unnamed: C4.2, C5.2, L3.1, L4.2
unnamed: C7.2, JP1.1, L4.1, U$4.P$1
RESET: U$2.PROG1 (RESET), U$3.4 (PB3)
SCL/SCK: U$2.BUS3 (SCL), U$2.PROG2 (SCK), U$3.9 (PA4)
SDA/MOSI: U$2.BUS1 (SDA), U$2.PROG4 (MOSI), U$3.7 (PA6)
SX_DIO0: U$1.7 (DIO0), U$5.P$1
SX_DIO1: U$1.8 (DIO1), U$3.5 (PB2), U$6.P$1
SX_DIO2: U$1.9 (DIO2), U$3.6 (PA7), U$7.P$1
SX_DIO3: U$1.10 (DIO3), U$8.P$1
SX_DIO4: U$1.11 (DIO4), U$9.P$1
SX_DIO5: U$1.12 (DIO5), U$10.P$1
SX_MISO: U$1.16 (MISO), U$3.13 (PA0), U$13.P$1
SX_MOSI: U$1.17 (MOSI), U$3.12 (PA1), U$14.P$1
SX_NSS: U$1.18 (NSS), U$3.11 (PA2), U$15.P$1
SX_RESET: U$1.6 (RESET), U$3.2 (PB0), U$11.P$1
SX_RXTX: U$1.19 (RXTX), U$3.3 (PB1), U$17.P$1
SX_SCK: U$1.15 (SCK), U$3.10 (PA3), U$16.P$1
VCC: C6.2, C20.1, C21.1, U1.5 (OUT), U$1.1 (VBAT1), U$1.13 (VBAT2), U$2.PROG0 (VPROG), U$3.1 (VCC)
VR_PA: C1.1, L2.1, U$1.24 (VR_PA)
