modulolabs/pcb/SX1231/SX1231.brd

## EAGLE design SX1231/SX1231.brd (continued)

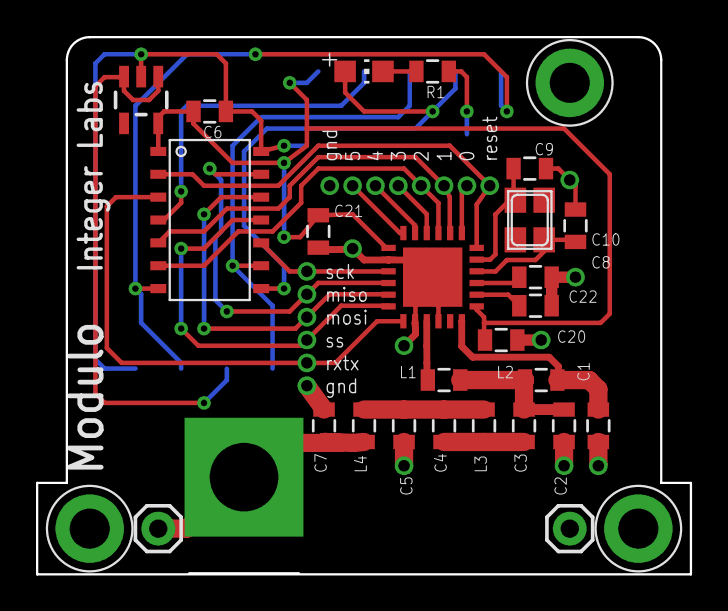
[picture p52: board SX1231.brd from above]

Board: 2 copper layers, 36.3 x 29.8 mm, 40 parts (0 on the bottom side), 30 nets.
