modulolabs/pcb/PowerSupply/PowerSupply.brd

## EAGLE design PowerSupply/PowerSupply.brd (2015-04-02)

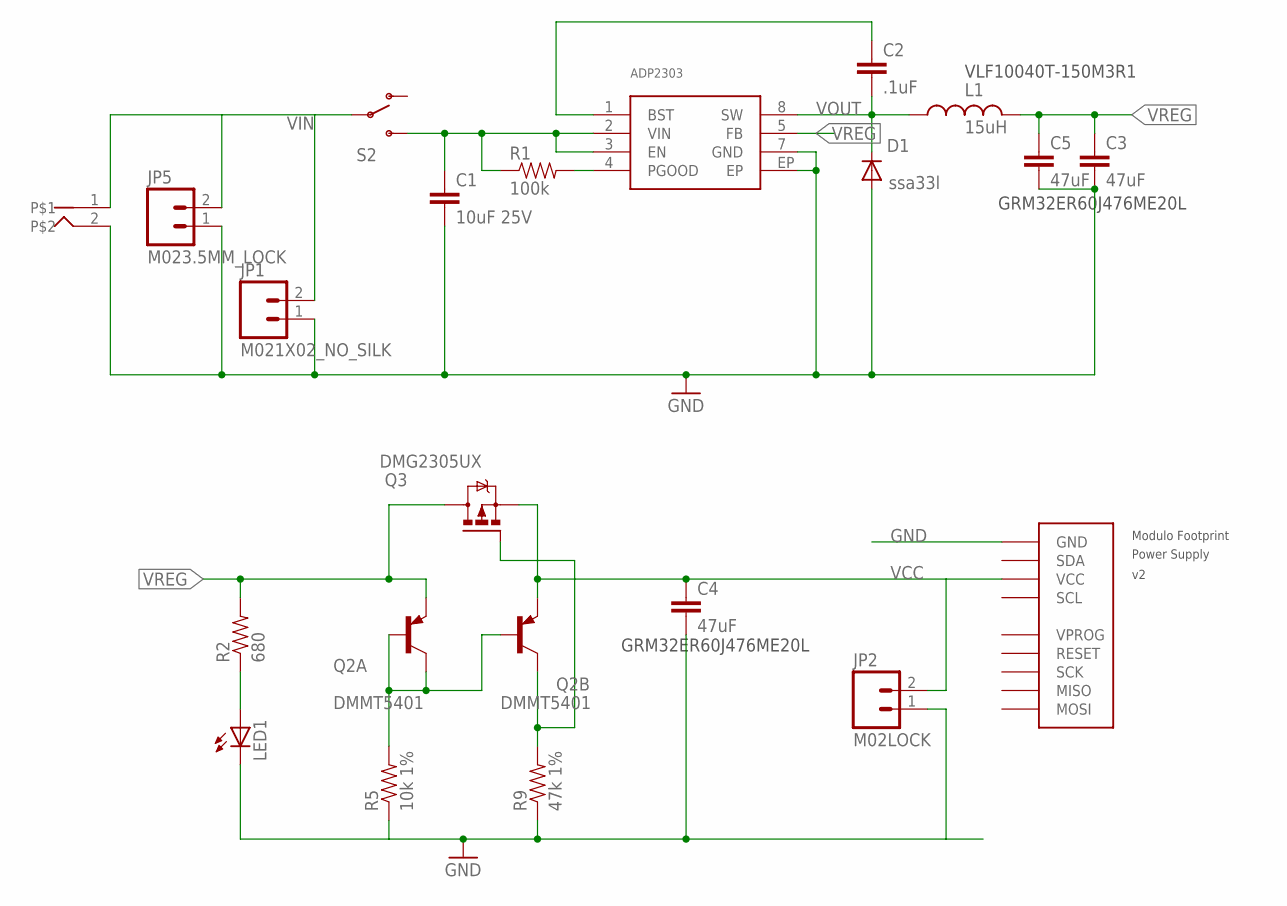
[picture p53: schematic PowerSupply.sch]

Parts:
C1: 10uF 25V; 0805
C2: .1uF; 0805
C3, C4, C5: 47uF; 1210
D1: ssa33l; SMA-DIODE
JP1: M021X02_NO_SILK; 1X02_NO_SILK
JP2: M02LOCK; 1X02_LOCK
JP5: M023.5MM_LOCK; SCREWTERMINAL-3.5MM-2_LOCK
L1: 15uH; INDUCTOR-VLF10040
LED1: LEDCHIP-LED0805; CHIP-LED0805
Q2: DMMT5401; SOT-26
Q3: DMG2305UX; MICRO3
R1: 100k; 0805
R2: 680; 0805
R5: 10k 1%; 0805
R9: 47k 1%; 0805
S2: SWITCH-SPDTPTH_LOCK; SWITCH-SPDT_LOCK.007S
U$3: ADP2303; SOIC8-EP
U$4: FOOTPRINTFOOTPRINT-2; FOOTPRINT2
U$21: DC-JACKLOWPRO; DC-POWER-JACK-LOWPRO

Connections:
GND: C1.2, C3.2, C4.2, C5.2, D1.A, JP1.1, JP2.1, JP5.1, LED1.C, R5.1, R9.1, U$3.7 (GND), U$3.EP, U$4.BUS0 (GND), U$21.2
unnamed: JP1.2, JP5.2, S2.2, U$21.1
unnamed: R1.2, U$3.4 (PGOOD)
unnamed: LED1.A, R2.1
unnamed: C2.1, U$3.1 (BST)
unnamed: Q2.1 (C), Q2.2 (B), Q2.3 (B), R5.2
unnamed: Q2.4 (C), Q3.1 (G), R9.2
VCC: C4.1, JP2.2, Q2.5 (E), Q3.2 (S), U$4.BUS2 (VCC)
VIN: C1.1, R1.1, S2.3 (S), U$3.2 (VIN), U$3.3 (EN)
VOUT: C2.2, D1.C, L1.P$1 (1), U$3.8 (SW)
VREG: C3.1, C5.1, L1.P$2 (2), Q2.6 (E), Q3.3 (D), R2.2, U$3.5 (FB)

Notes on the sheet:
GRM32ER60J476ME20L
VLF10040T-150M3R1

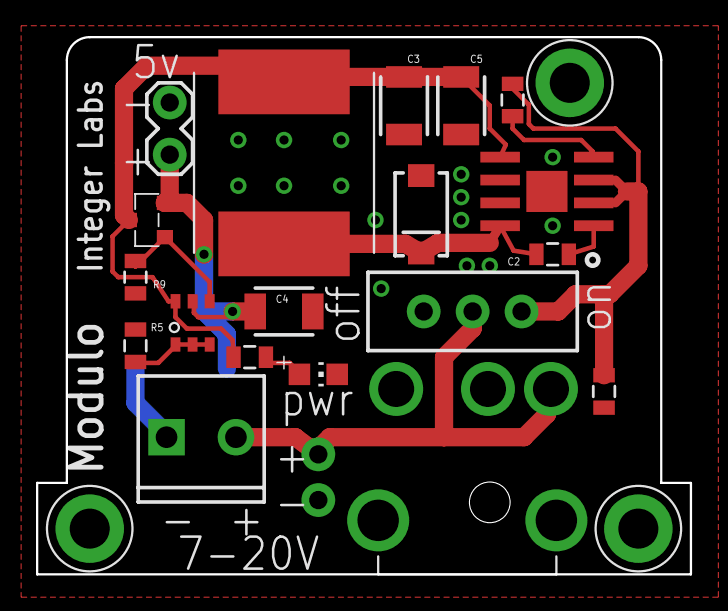
[picture p54: board PowerSupply.brd from above]

Board: 2 copper layers, 36.3 x 29.8 mm, 21 parts (0 on the bottom side), 11 nets.
