modulolabs/pcb/32u4/32u4.brd

## EAGLE design 32u4/32u4.brd (2015-04-02)

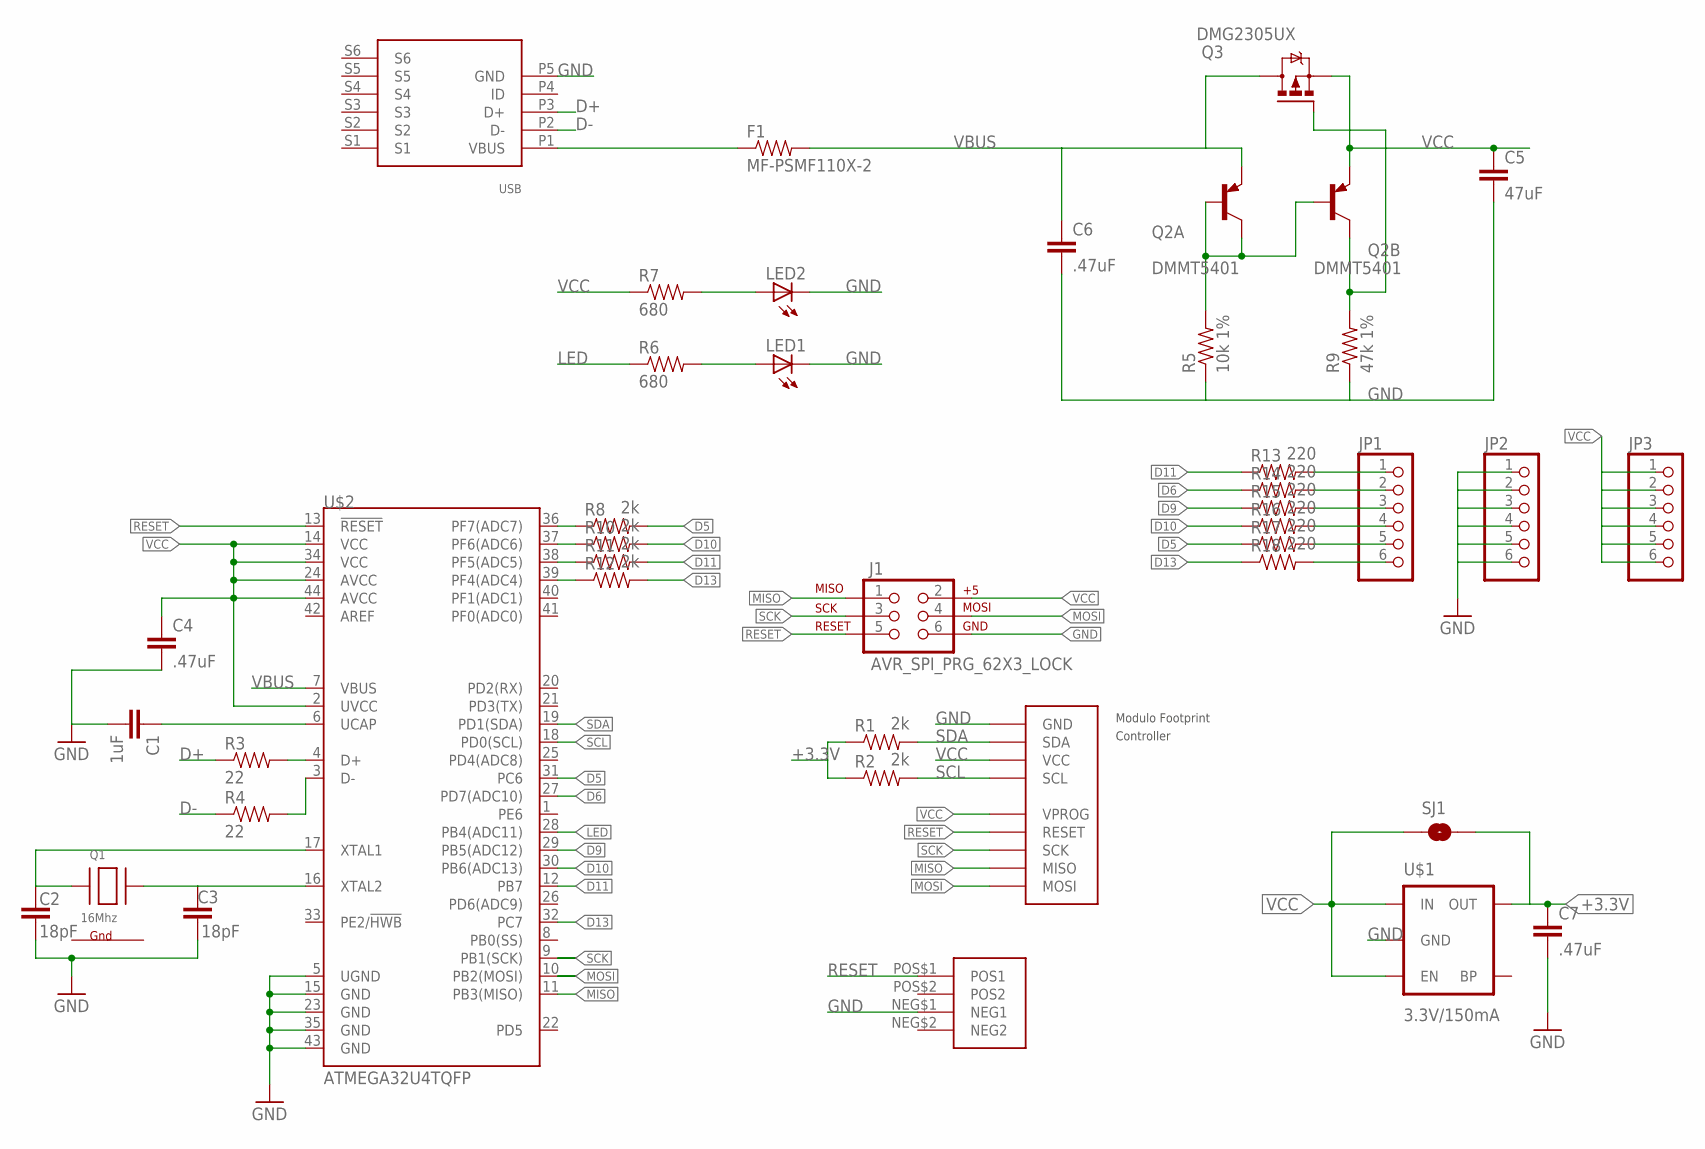
[picture p55: schematic 32u4.sch]

Parts:
C1: 1uF; 0805
C2, C3: 18pF; 0805
C4, C6, C7: .47uF; 0805
C5: 47uF; 0805
F1: MF-PSMF110X-2; 0805
FOOTPRINT: Controller; FOOTPRINT2
J1: AVR_SPI_PRG_62X3_LOCK; 2X3_LOCK
JP1, JP2, JP3: PINHD-1X6LOCK; 1X06-BIGLOCK
LED1, LED2: LEDCHIP-LED0805; CHIP-LED0805
Q1: 16Mhz; NX3225
Q2: DMMT5401; SOT-26
Q3: DMG2305UX; MICRO3
R1, R2, R8, R10, R11, R12: 2k; 0805
R3, R4: 22; 0805
R5: 10k 1%; 0805
R6, R7: 680; 0805
R9: 47k 1%; 0805
R13, R14, R15, R16, R17, R18: 220; 0805
SJ1: SOLDERJUMPERNO; SJ_2S-NO
U$1: 3.3V/150mA; SOT23-5
U$2: ATMEGA32U4TQFP; SPARKFUN-DIGITALIC_TQFP44
U$4: USBFCI-MICROB; USB-MICROB-FCI
U$6: TACT-SWITCHBOURNS-7914J; BOURNS-7914J

Connections:
+3.3V: C7.1, R1.1, R2.1, SJ1.2, U$1.5 (OUT)
D0: R12.2, R18.1, U$2.32 (PC7)
D1: R8.2, R17.1, U$2.31 (PC6)
D2: R10.2, R16.1, U$2.30 (PB6(ADC13))
D3: R15.1, U$2.29 (PB5(ADC12))
D4: R14.1, U$2.27 (PD7(ADC10))
D5: R11.2, R13.1, U$2.12 (PB7)
D+: R3.1, U$4.P3 (D+)
D-: R4.1, U$4.P2 (D-)
G1: Q1.4 (G1)
G2: Q1.2 (G2)
GND: C1.2, C2.2, C3.2, C4.2, C5.2, C6.2, C7.2, FOOTPRINT.BUS0 (GND), J1.6, JP2.1, JP2.2, JP2.3, JP2.4, JP2.5, JP2.6, LED1.C, LED2.C, R5.1, R9.1, U$1.2 (GND), U$2.5 (UGND), U$2.15 (GND), U$2.23 (GND), U$2.35 (GND), U$2.43 (GND), U$4.P5 (GND), U$6.NEG$1 (NEG1)
LED: R6.1, U$2.28 (PB4(ADC11))
MISO: FOOTPRINT.PROG3 (MISO), J1.1, U$2.11 (PB3(MISO))
MOSI: FOOTPRINT.PROG4 (MOSI), J1.4, U$2.10 (PB2(MOSI))
unnamed: C1.1, U$2.6 (UCAP)
unnamed: JP1.1, R13.2
unnamed: F1.1, U$4.P1 (VBUS)
unnamed: C3.1, Q1.3 (X2), U$2.16 (XTAL2)
unnamed: LED1.A, R6.2
unnamed: R12.1, U$2.39 (PF4(ADC4))
unnamed: R11.1, U$2.38 (PF5(ADC5))
unnamed: R3.2, U$2.4 (D+)
unnamed: R4.2, U$2.3 (D-)
unnamed: R10.1, U$2.37 (PF6(ADC6))
unnamed: R8.1, U$2.36 (PF7(ADC7))
unnamed: LED2.A, R7.2
unnamed: JP1.2, R14.2
unnamed: Q2.1 (C), Q2.2 (B), Q2.3 (B), R5.2
unnamed: C2.1, Q1.1 (X1), U$2.17 (XTAL1)
unnamed: Q2.4 (C), Q3.1 (G), R9.2
unnamed: JP1.3, R15.2
unnamed: JP1.4, R16.2
unnamed: JP1.5, R17.2
unnamed: JP1.6, R18.2
RESET: FOOTPRINT.PROG1 (RESET), J1.5, U$2.13 (!RESET), U$6.POS$1 (POS1)
SCK: FOOTPRINT.PROG2 (SCK), J1.3, U$2.9 (PB1(SCK))
SCL: FOOTPRINT.BUS3 (SCL), R2.2, U$2.18 (PD0(SCL))
SDA: FOOTPRINT.BUS1 (SDA), R1.2, U$2.19 (PD1(SDA))
VBUS: C6.1, F1.2, Q2.6 (E), Q3.3 (D), U$2.7 (VBUS)
VCC: C4.1, C5.1, FOOTPRINT.BUS2 (VCC), FOOTPRINT.PROG0 (VPROG), J1.2, JP3.1, JP3.2, JP3.3, JP3.4, JP3.5, JP3.6, Q2.5 (E), Q3.2 (S), R7.1, SJ1.1, U$1.1 (IN), U$1.3 (EN), U$2.2 (UVCC), U$2.14 (VCC), U$2.24 (AVCC), U$2.34 (VCC), U$2.44 (AVCC)

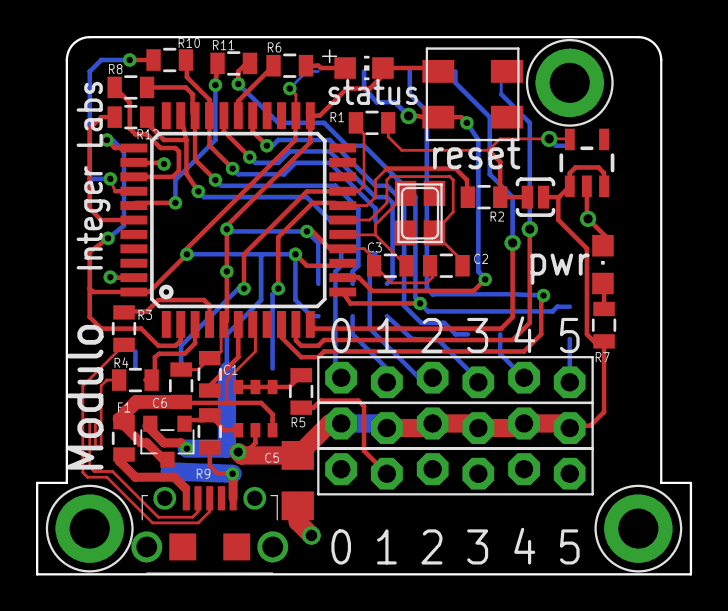
[picture p56: board 32u4.brd from above]

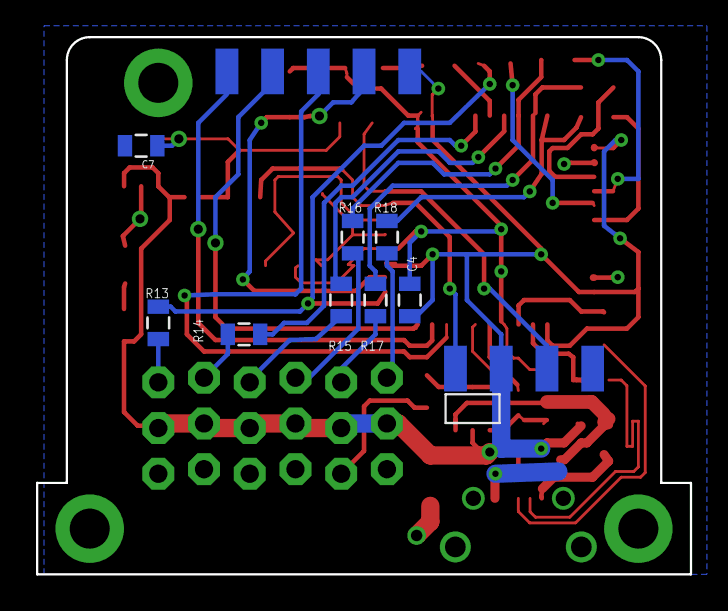
[picture p57: board 32u4.brd from below]

Board: 2 copper layers, 36.3 x 29.8 mm, 40 parts (8 on the bottom side), 39 nets.
