modulolabs/pcb/ControllerBase/ControllerBase.brd

## EAGLE design ControllerBase/ControllerBase.brd (2015-04-02)

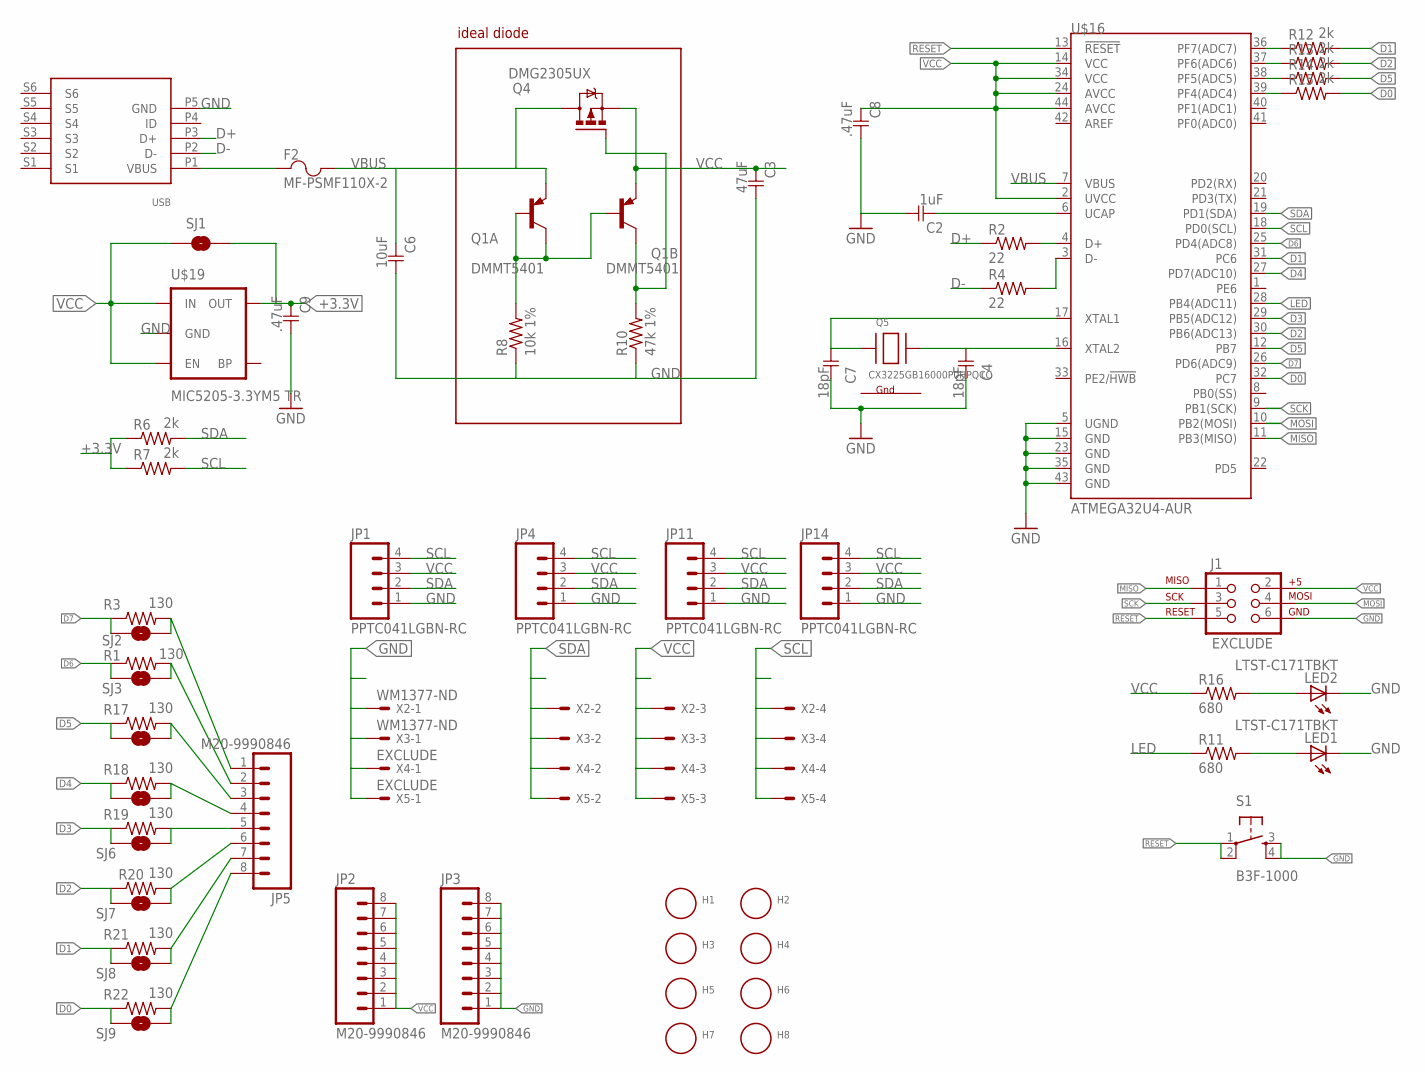
[picture p58: schematic ControllerBase.sch]

Parts:
C2: 1uF; 0805
C3: 47uF; 0805
C4, C7: 18pF; 0805
C6: 10uF; 0805
C8, C9: .47uF; 0805
F2: MF-PSMF110X-2; 0805
H1, H2, H3, H4, H5, H6, H7, H8: EXCLUDE; HOLE-#2
J1: EXCLUDE; 2X3_LOCK
JP1, JP4, JP11, JP14: PPTC041LGBN-RC; 1X04_LOCK
JP2, JP3, JP5: M20-9990846; 1X08_NO_SILK
LED1, LED2: LTST-C171TBKT; 0805-LED
Q1: DMMT5401; SOT-26
Q4: DMG2305UX; MICRO3
Q5: CX3225GB16000P0HPQCC; NX3225
R1, R3, R17, R18, R19, R20, R21, R22: 130; 0805
R2, R4: 22; 0805
R6, R7, R12, R13, R14, R15: 2k; 0805
R8: 10k 1%; 0805
R10: 47k 1%; 0805
R11, R16: 680; 0805
S1: B3F-1000; TACTILE-PTH
SJ1, SJ2, SJ3, SJ4, SJ5, SJ6, SJ7, SJ8, SJ9: EXCLUDE; SJ_2S-NO
U$16: ATMEGA32U4-AUR; SPARKFUN-DIGITALIC_TQFP44
U$17: 10118194-0001LF; USB-MICROB-FCI
U$19: MIC5205-3.3YM5 TR; SOT23-5
X2, X3: WM1377-ND; 15-91-04
X4, X5: EXCLUDE; 15-91-04

Connections:
+3.3V: C9.1, R6.1, R7.1, SJ1.2, U$19.5 (OUT)
D0: R15.2, R22.1, SJ9.1, U$16.32 (PC7)
D1: R12.2, R21.1, SJ8.1, U$16.31 (PC6)
D2: R13.2, R20.1, SJ7.1, U$16.30 (PB6(ADC13))
D3: R19.1, SJ6.1, U$16.29 (PB5(ADC12))
D4: R18.1, SJ5.1, U$16.27 (PD7(ADC10))
D5: R14.2, R17.1, SJ4.1, U$16.12 (PB7)
D6: R1.1, SJ3.1, U$16.25 (PD4(ADC8))
D7: R3.1, SJ2.1, U$16.26 (PD6(ADC9))
D+: R2.1, U$17.P3 (D+)
D-: R4.1, U$17.P2 (D-)
G1: Q5.4 (G1)
G2: Q5.2 (G2)
GND: C2.2, C3.2, C4.2, C6.2, C7.2, C8.2, C9.2, J1.6, JP1.1, JP3.1, JP3.2, JP3.3, JP3.4, JP3.5, JP3.6, JP3.7, JP3.8, JP4.1, JP11.1, JP14.1, LED1.C, LED2.C, R8.1, R10.1, S1.3, S1.4, U$16.5 (UGND), U$16.15 (GND), U$16.23 (GND), U$16.35 (GND), U$16.43 (GND), U$17.P5 (GND), U$19.2 (GND), X2.1, X3.1, X4.1, X5.1
LED: R11.1, U$16.28 (PB4(ADC11))
MISO: J1.1, U$16.11 (PB3(MISO))
MOSI: J1.4, U$16.10 (PB2(MOSI))
unnamed: JP5.2, R1.2, SJ3.2
unnamed: JP5.1, R3.2, SJ2.2
unnamed: C2.1, U$16.6 (UCAP)
unnamed: R2.2, U$16.4 (D+)
unnamed: R4.2, U$16.3 (D-)
unnamed: Q1.1 (C), Q1.2 (B), Q1.3 (B), R8.2
unnamed: Q1.4 (C), Q4.1 (G), R10.2
unnamed: F2.1, U$17.P1 (VBUS)
unnamed: LED1.A, R11.2
unnamed: C4.1, Q5.3 (X2), U$16.16 (XTAL2)
unnamed: R15.1, U$16.39 (PF4(ADC4))
unnamed: R14.1, U$16.38 (PF5(ADC5))
unnamed: R13.1, U$16.37 (PF6(ADC6))
unnamed: R12.1, U$16.36 (PF7(ADC7))
unnamed: LED2.A, R16.2
unnamed: C7.1, Q5.1 (X1), U$16.17 (XTAL1)
unnamed: JP5.3, R17.2, SJ4.2
unnamed: JP5.4, R18.2, SJ5.2
unnamed: JP5.5, R19.2, SJ6.2
unnamed: JP5.6, R20.2, SJ7.2
unnamed: JP5.7, R21.2, SJ8.2
unnamed: JP5.8, R22.2, SJ9.2
RESET: J1.5, S1.1, S1.2, U$16.13 (!RESET)
SCK: J1.3, U$16.9 (PB1(SCK))
SCL: JP1.4, JP4.4, JP11.4, JP14.4, R7.2, U$16.18 (PD0(SCL)), X2.4, X3.4, X4.4, X5.4
SDA: JP1.2, JP4.2, JP11.2, JP14.2, R6.2, U$16.19 (PD1(SDA)), X2.2, X3.2, X4.2, X5.2
VBUS: C6.1, F2.2, Q1.6 (E), Q4.3 (D), U$16.7 (VBUS)
VCC: C3.1, C8.1, J1.2, JP1.3, JP2.1, JP2.2, JP2.3, JP2.4, JP2.5, JP2.6, JP2.7, JP2.8, JP4.3, JP11.3, JP14.3, Q1.5 (E), Q4.2 (S), R16.1, SJ1.1, U$16.2 (UVCC), U$16.14 (VCC), U$16.24 (AVCC), U$16.34 (VCC), U$16.44 (AVCC), U$19.1 (IN), U$19.3 (EN), X2.3, X3.3, X4.3, X5.3

Notes on the sheet:
ideal diode

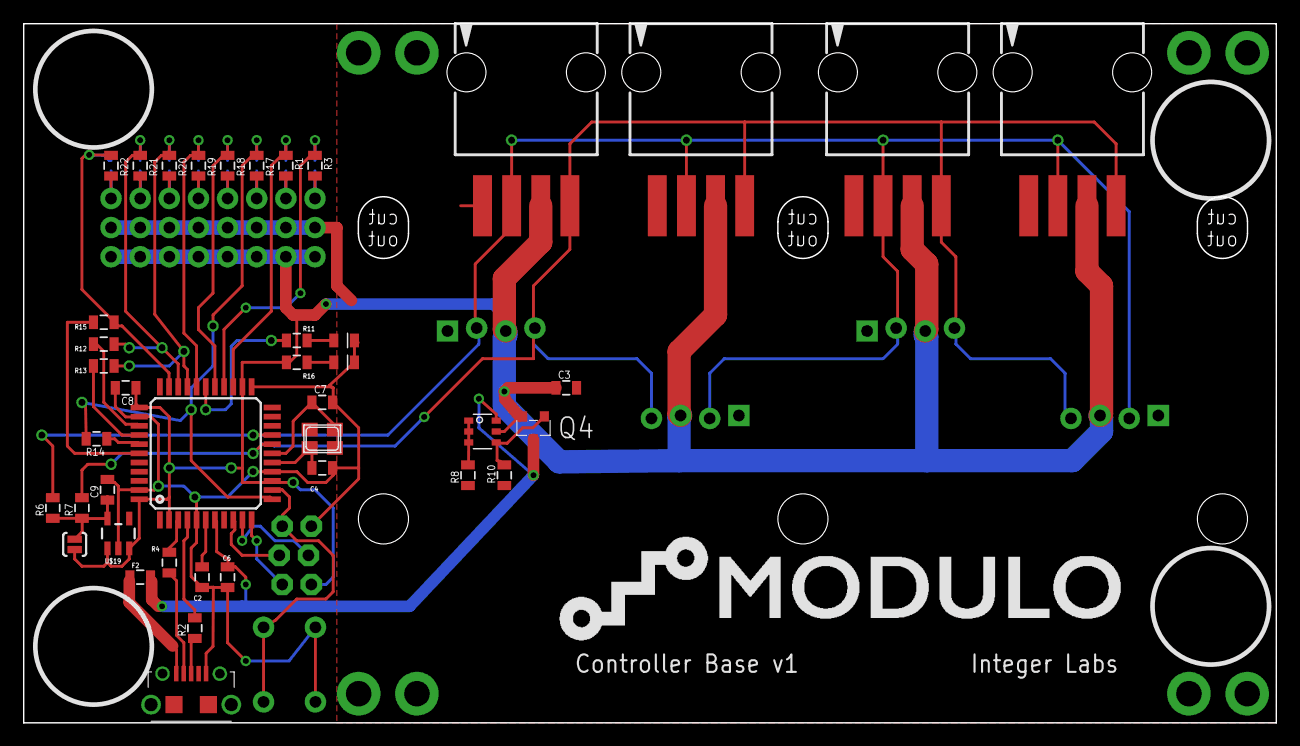
[picture p59: board ControllerBase.brd from above]

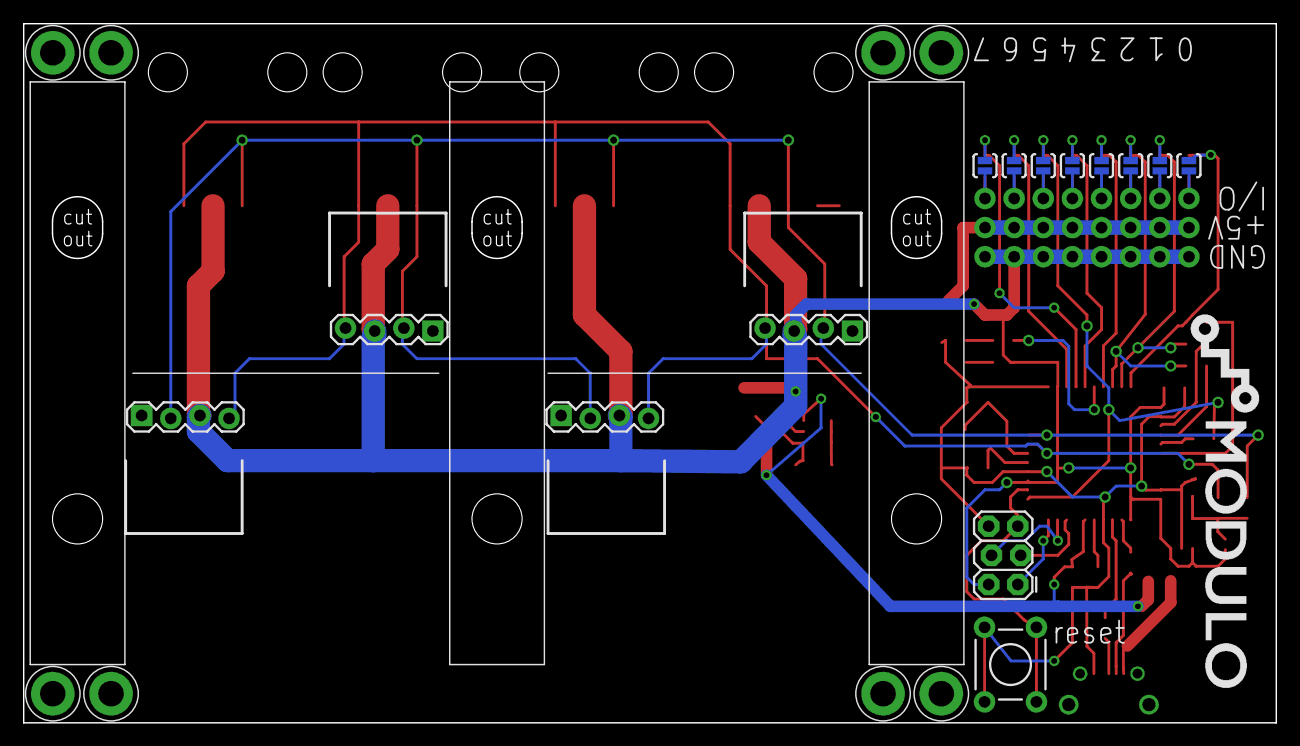
[picture p60: board ControllerBase.brd from below]

Board: 2 copper layers, 109.2 x 61.0 mm, 71 parts (29 on the bottom side), 43 nets.

Other parts of the board:
U$1: LOGO_WITH_TEXT_0.25_INCH
U$2: LOGO_WITH_TEXT_0.5
U$3, U$4, U$5: CARD-GUIDE-2"
