modulolabs/pcb/SparkBase/SparkBase.brd

## EAGLE design SparkBase/SparkBase.brd (2015-04-02)

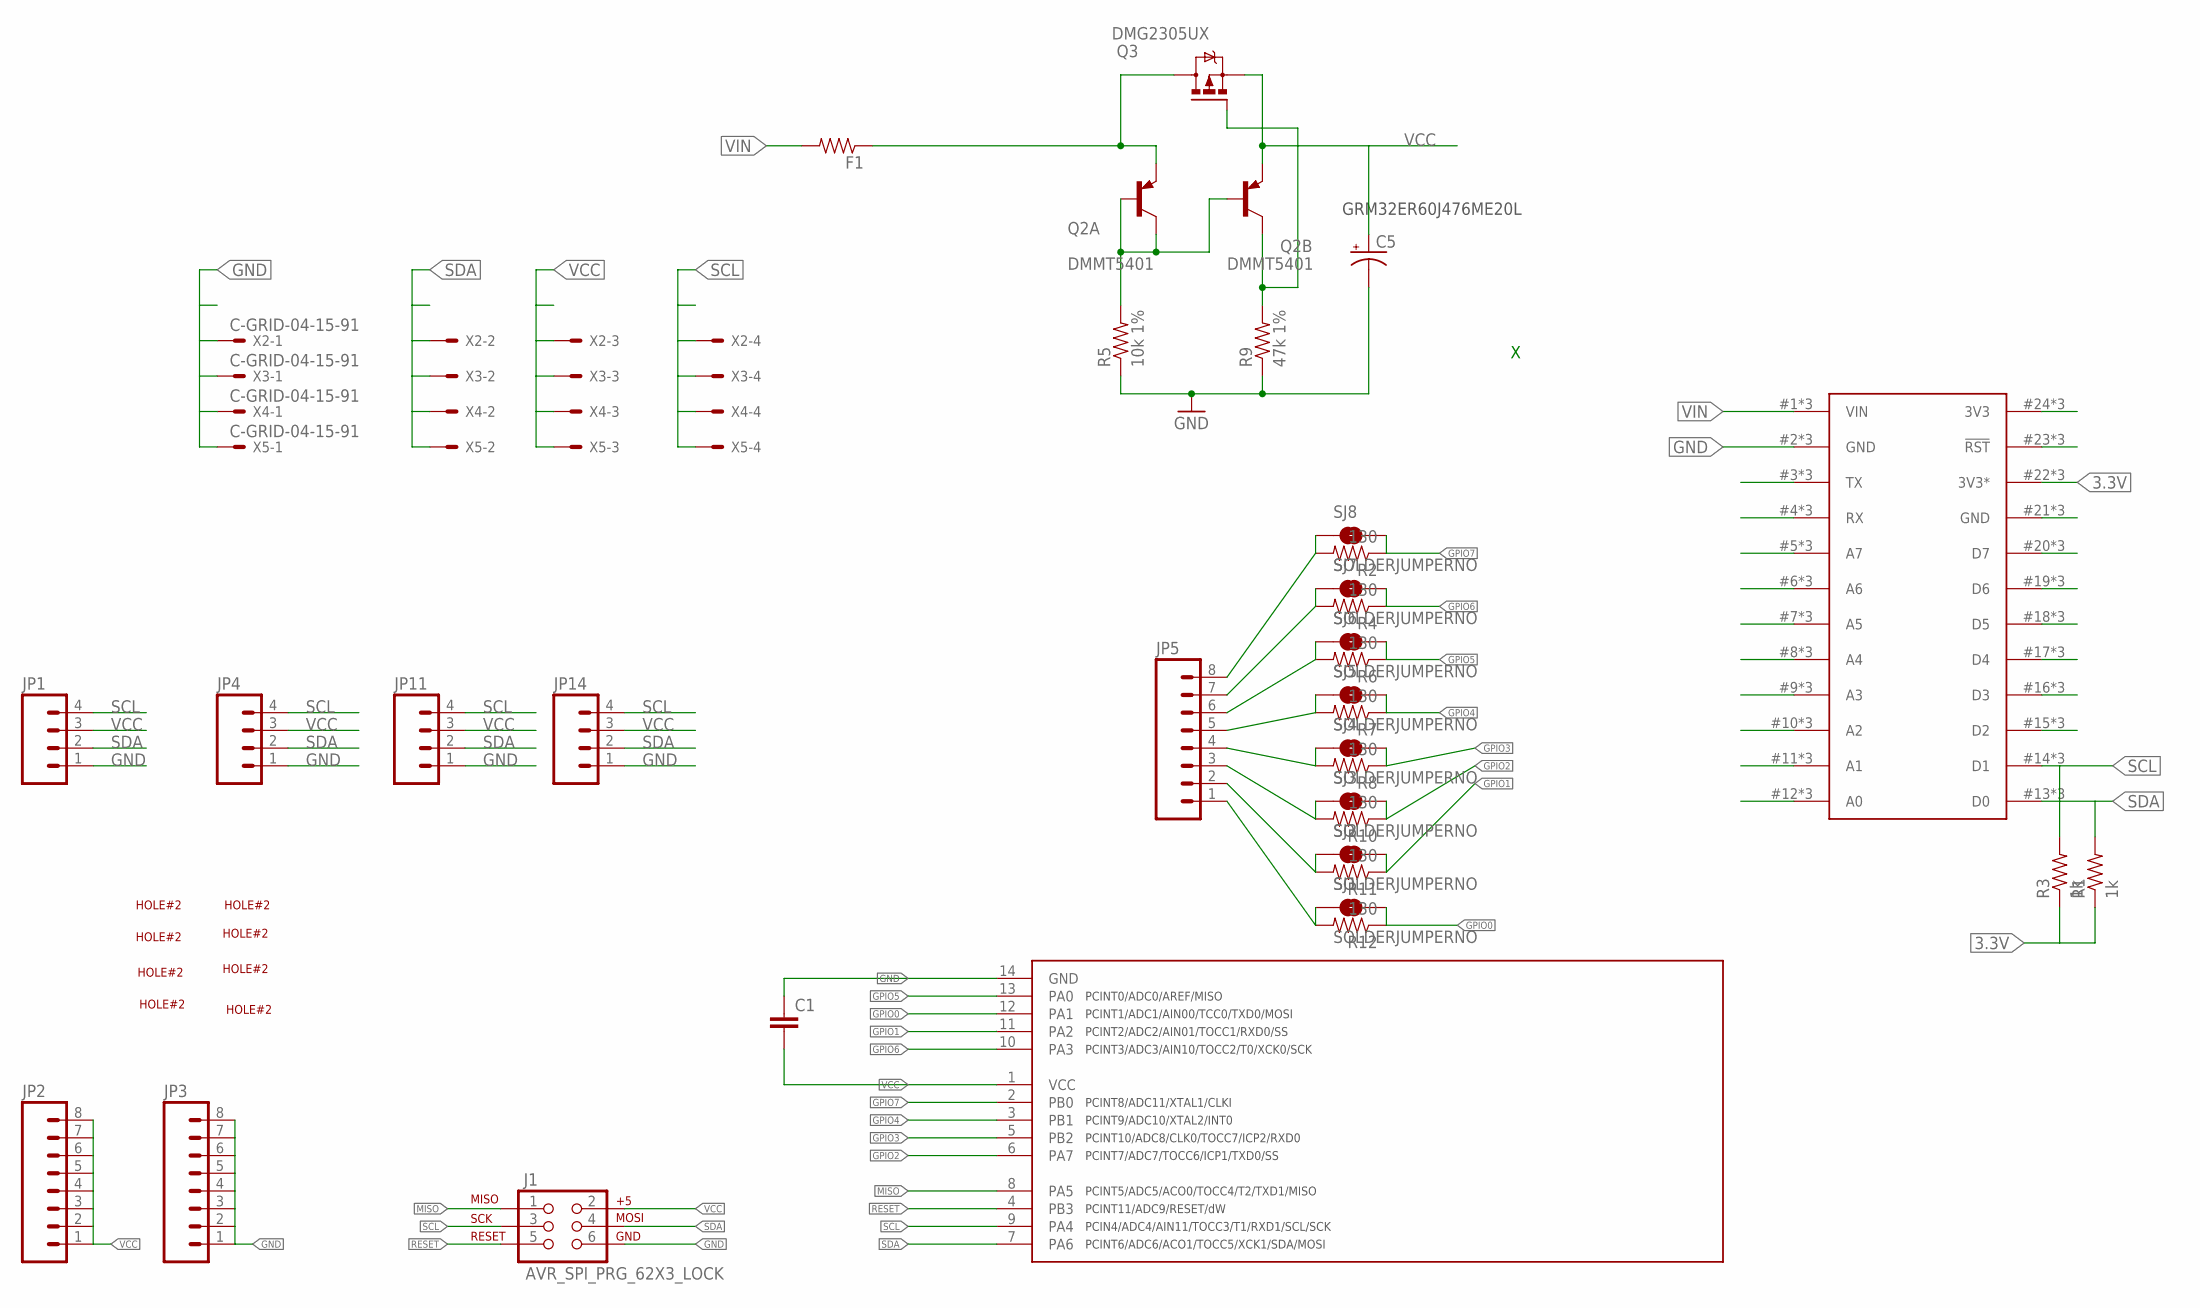
[picture p61: schematic SparkBase.sch]

Parts:
C1: CAP0805; 0805
C5: CAP_POLC; PANASONIC_C
F1: RESISTOR0805-RES; 0805
J1: AVR_SPI_PRG_62X3_LOCK; 2X3_LOCK
JP1, JP4, JP11, JP14: M04LOCK; 1X04_LOCK
JP2, JP3, JP5: M08NO_SILK; 1X08_NO_SILK
Q2: DMMT5401; SOT-26
Q3: DMG2305UX; MICRO3
R1, R3: 1k; 0805
R2, R4, R6, R7, R8, R10, R11, R12: 130; 0805
R5: 10k 1%; 0805
R9: 47k 1%; 0805
SJ1, SJ2, SJ3, SJ4, SJ5, SJ6, SJ7, SJ8: SOLDERJUMPERNO; SJ_2S-NO
U$2: SPARK_CORE; SPARK_CORE_STACKABLE
U$6: TINY841; SOIC14
U$7, U$8, U$9, U$10, U$11, U$12, U$13, U$14: HOLE#2; HOLE-#2
X2, X3, X4, X5: C-GRID-04-15-91; 15-91-04

Connections:
3.3V: R1.1, R3.1, U$2.22 (3V3*), U$2.#22 (3V3*), U$2.@22 (3V3*)
GND: C1.1, C5.-, J1.6, JP1.1, JP3.1, JP3.2, JP3.3, JP3.4, JP3.5, JP3.6, JP3.7, JP3.8, JP4.1, JP11.1, JP14.1, R5.1, R9.1, U$2.2 (GND), U$2.#2 (GND), U$2.@2 (GND), U$6.14 (GND), X2.1, X3.1, X4.1, X5.1
GPIO0: R12.1, SJ1.2, U$6.12 (PA1)
GPIO1: R11.1, SJ2.2, U$6.11 (PA2)
GPIO2: R10.1, SJ3.2, U$6.6 (PA7)
GPIO3: R8.1, SJ4.2, U$6.5 (PB2)
GPIO4: R7.1, SJ5.2, U$6.3 (PB1)
GPIO5: R6.1, SJ6.2, U$6.13 (PA0)
GPIO6: R4.1, SJ7.2, U$6.10 (PA3)
GPIO7: R2.1, SJ8.2, U$6.2 (PB0)
MISO: J1.1, U$6.8 (PA5)
unnamed: U$2.3 (TX), U$2.#3 (TX), U$2.@3 (TX)
unnamed: U$2.4 (RX), U$2.#4 (RX), U$2.@4 (RX)
unnamed: U$2.5 (A7), U$2.#5 (A7), U$2.@5 (A7)
unnamed: U$2.6 (A6), U$2.#6 (A6), U$2.@6 (A6)
unnamed: U$2.7 (A5), U$2.#7 (A5), U$2.@7 (A5)
unnamed: U$2.8 (A4), U$2.#8 (A4), U$2.@8 (A4)
unnamed: U$2.9 (A3), U$2.#9 (A3), U$2.@9 (A3)
unnamed: U$2.10 (A2), U$2.#10 (A2), U$2.@10 (A2)
unnamed: U$2.11 (A1), U$2.#11 (A1), U$2.@11 (A1)
unnamed: U$2.12 (A0), U$2.#12 (A0), U$2.@12 (A0)
unnamed: U$2.24 (3V3), U$2.#24 (3V3), U$2.@24 (3V3)
unnamed: U$2.23 (!RST), U$2.#23 (!RST), U$2.@23 (!RST)
unnamed: U$2.21 (GND), U$2.#21 (GND), U$2.@21 (GND)
unnamed: Q2.1 (C), Q2.2 (B), Q2.3 (B), R5.2
unnamed: U$2.20 (D7), U$2.#20 (D7), U$2.@20 (D7)
unnamed: Q2.4 (C), Q3.1 (G), R9.2
unnamed: U$2.19 (D6), U$2.#19 (D6), U$2.@19 (D6)
unnamed: U$2.18 (D5), U$2.#18 (D5), U$2.@18 (D5)
unnamed: U$2.17 (D4), U$2.#17 (D4), U$2.@17 (D4)
unnamed: U$2.16 (D3), U$2.#16 (D3), U$2.@16 (D3)
unnamed: U$2.15 (D2), U$2.#15 (D2), U$2.@15 (D2)
unnamed: JP5.1, R12.2, SJ1.1
unnamed: JP5.2, R11.2, SJ2.1
unnamed: JP5.3, R10.2, SJ3.1
unnamed: JP5.4, R8.2, SJ4.1
unnamed: JP5.5, R7.2, SJ5.1
unnamed: JP5.6, R6.2, SJ6.1
unnamed: JP5.7, R4.2, SJ7.1
unnamed: JP5.8, R2.2, SJ8.1
RESET: J1.5, U$6.4 (PB3)
SCL: J1.3, JP1.4, JP4.4, JP11.4, JP14.4, R3.2, U$2.14 (D1), U$2.#14 (D1), U$2.@14 (D1), U$6.9 (PA4), X2.4, X3.4, X4.4, X5.4
SDA: J1.4, JP1.2, JP4.2, JP11.2, JP14.2, R1.2, U$2.13 (D0), U$2.#13 (D0), U$2.@13 (D0), U$6.7 (PA6), X2.2, X3.2, X4.2, X5.2
VCC: C1.2, C5.+, J1.2, JP1.3, JP2.1, JP2.2, JP2.3, JP2.4, JP2.5, JP2.6, JP2.7, JP2.8, JP4.3, JP11.3, JP14.3, Q2.5 (E), Q3.2 (S), U$6.1 (VCC), X2.3, X3.3, X4.3, X5.3
VIN: F1.2, U$2.1 (VIN), U$2.#1 (VIN), U$2.@1 (VIN)
VREG: F1.1, Q2.6 (E), Q3.3 (D)

Notes on the sheet:
GRM32ER60J476ME20L

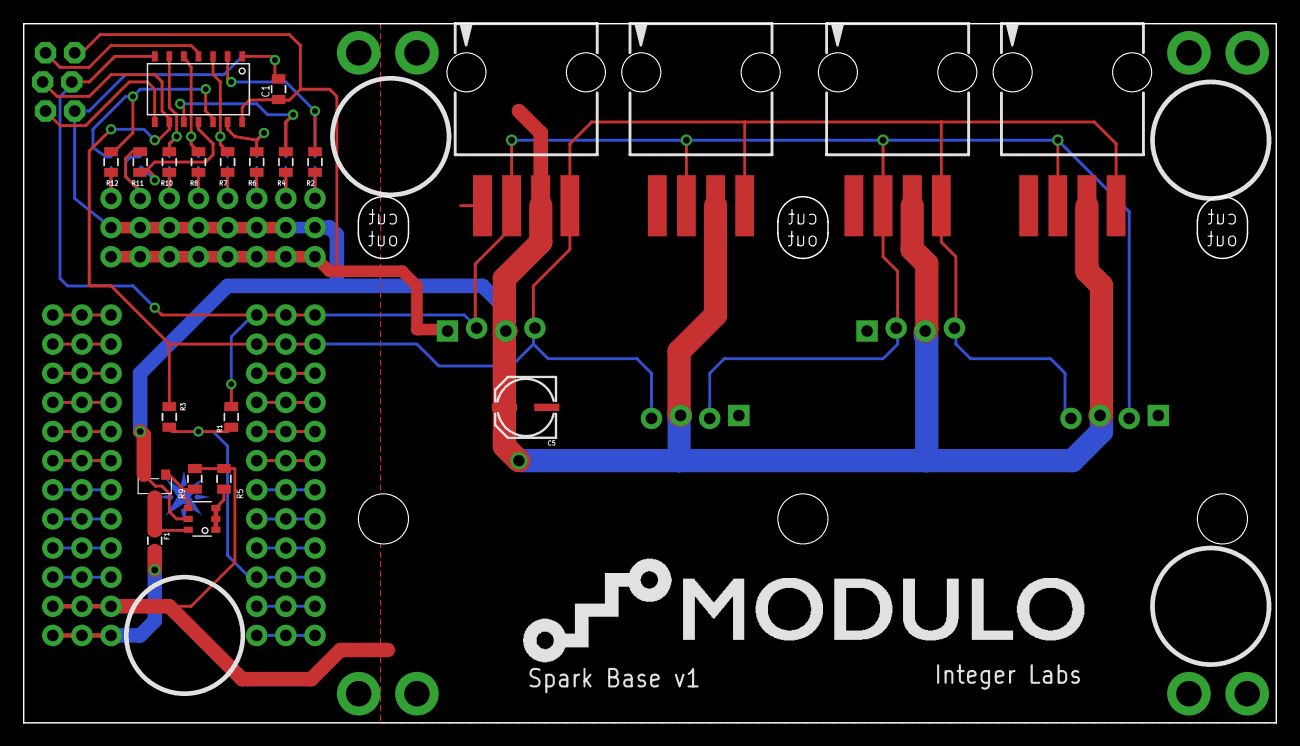
[picture p62: board SparkBase.brd from above]

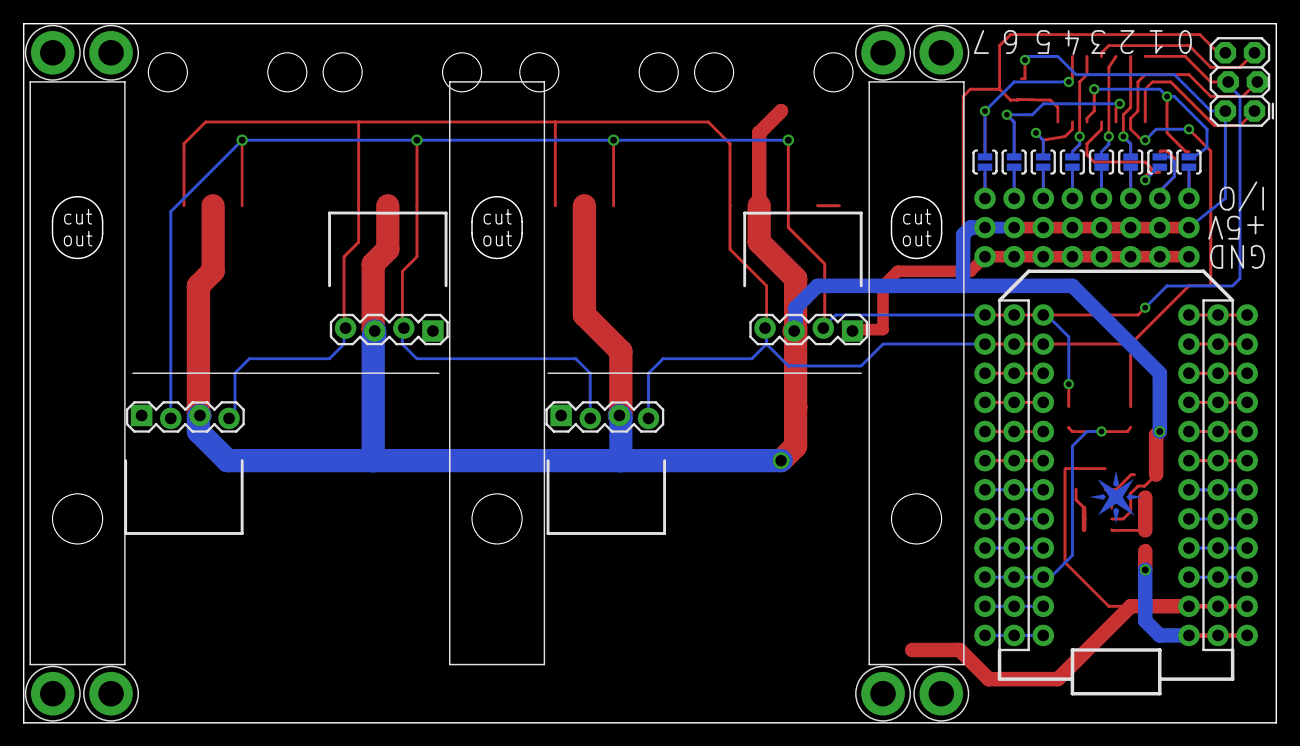
[picture p63: board SparkBase.brd from below]

Board: 2 copper layers, 109.2 x 61.0 mm, 52 parts (29 on the bottom side), 46 nets.

Other parts of the board:
U$1: SPARK_LOGO_PLUS_PLANE
U$3, U$4, U$5: CARD-GUIDE-2"
U$15: LOGO_WITH_TEXT_0.5
