modulolabs/pcb/NJM2670/NJM2670.brd

## EAGLE design NJM2670/NJM2670.brd (2015-04-02)

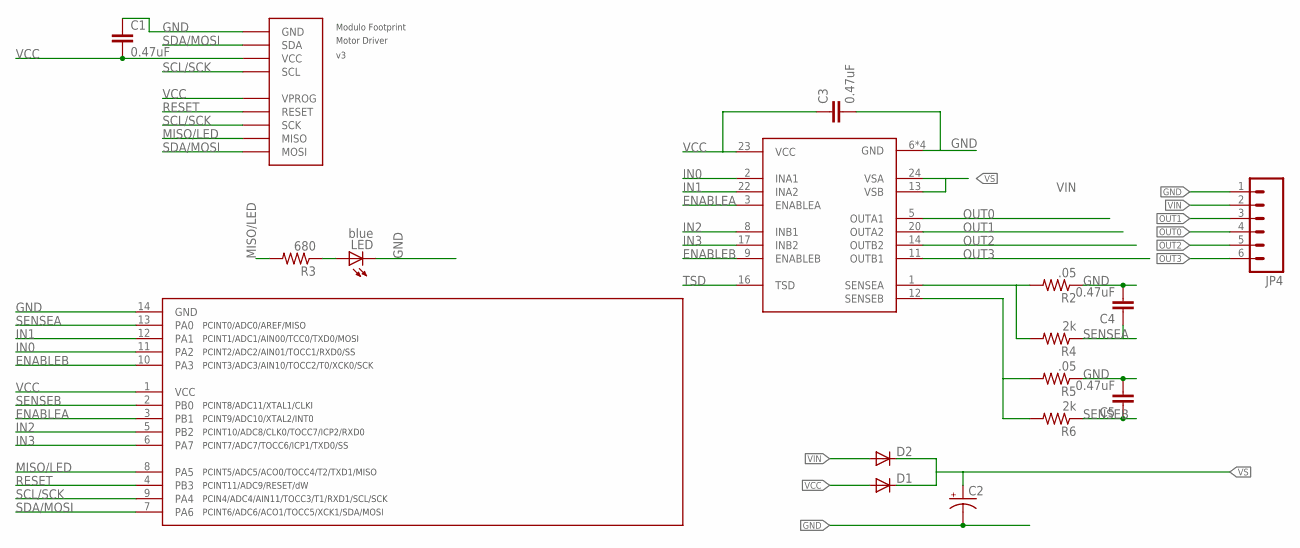
[picture p64: schematic NJM2670.sch]

Parts:
C1, C3, C4, C5: 0.47uF; 0805
C2: CAP_POLC; PANASONIC_C
D1, D2: DIODESMA; SMA-DIODE
JP4: M063.5MM-6; SCREWTERMINAL-3.5MM-6
LED: blue; CHIPLED_0805
R2, R5: .05; 0805
R3: 680; 0805
R4, R6: 2k; 0805
U$1: FOOTPRINTFOOTPRINT-2; FOOTPRINT2
U$3: TINY841; SOIC14
U$6: NJM2670; SOP-24-E3

Connections:
ENABLEA: U$3.3 (PB1), U$6.3 (ENABLEA)
ENABLEB: U$3.10 (PA3), U$6.9 (ENABLEB)
GND: C1.1, C2.-, C3.2, C4.2, C5.2, JP4.1, LED.C, R2.1, R5.1, U$1.BUS0 (GND), U$3.14 (GND), U$6.6 (GND), U$6.7 (GND), U$6.18 (GND), U$6.19 (GND)
IN0: U$3.11 (PA2), U$6.2 (INA1)
IN1: U$3.12 (PA1), U$6.22 (INA2)
IN2: U$3.5 (PB2), U$6.8 (INB1)
IN3: U$3.6 (PA7), U$6.17 (INB2)
MISO/LED: R3.2, U$1.PROG3 (MISO), U$3.8 (PA5)
unnamed: R2.2, R4.2, U$6.1 (SENSEA)
unnamed: R5.2, R6.2, U$6.12 (SENSEB)
unnamed: LED.A, R3.1
OUT0: JP4.4, U$6.5 (OUTA1)
OUT1: JP4.3, U$6.20 (OUTA2)
OUT2: JP4.5, U$6.14 (OUTB2)
OUT3: JP4.6, U$6.11 (OUTB1)
RESET: U$1.PROG1 (RESET), U$3.4 (PB3)
SCL/SCK: U$1.BUS3 (SCL), U$1.PROG2 (SCK), U$3.9 (PA4)
SDA/MOSI: U$1.BUS1 (SDA), U$1.PROG4 (MOSI), U$3.7 (PA6)
SENSEA: C4.1, R4.1, U$3.13 (PA0)
SENSEB: C5.1, R6.1, U$3.2 (PB0)
TSD: U$6.16 (TSD)
VCC: C1.2, C3.1, D1.A, U$1.BUS2 (VCC), U$1.PROG0 (VPROG), U$3.1 (VCC), U$6.23 (VCC)
VIN: D2.A, JP4.2
VS: C2.+, D1.C, D2.C, U$6.13 (VSB), U$6.24 (VSA)

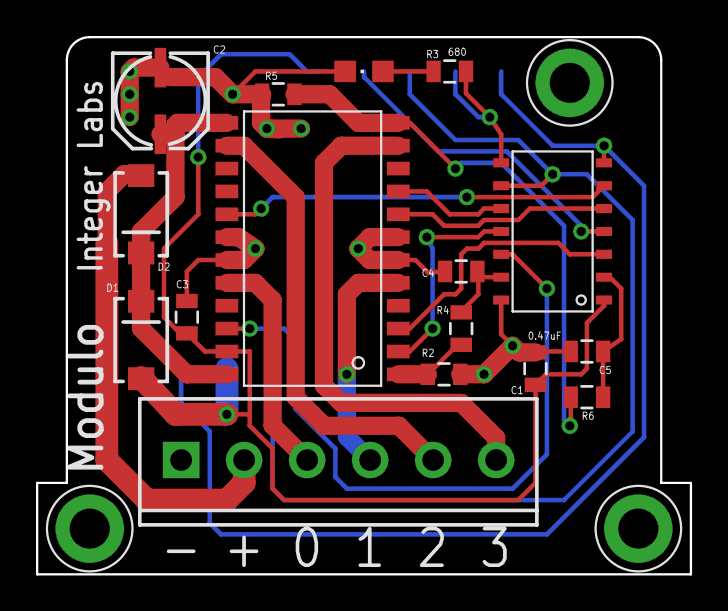
[picture p65: board NJM2670.brd from above]

Board: 2 copper layers, 36.3 x 29.8 mm, 17 parts (0 on the bottom side), 23 nets.
