modulolabs/pcb/MagBase/MagBase.brd

## EAGLE design MagBase/MagBase.brd (2015-04-02)

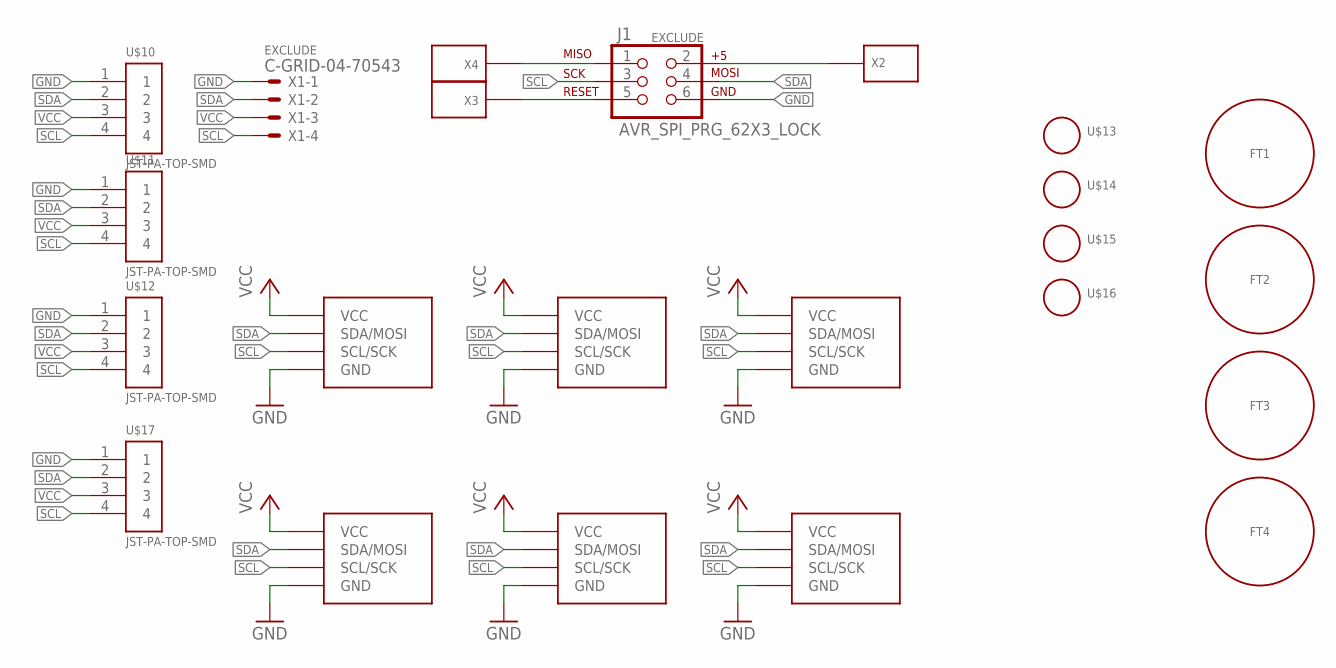
[picture p66: schematic MagBase.sch]

Parts:
FT1, FT2, FT3, FT4: FOOT
J1: AVR_SPI_PRG_62X3_LOCK; 2X3_LOCK; PARTNUM EXCLUDE
U$1, U$2, U$3, U$4, U$5, U$6: MAGBASE
U$10, U$11, U$12, U$17: JST-PA-TOP-SMD; PARTNUM BM04B-PASS-1-TFT(LF)(SN)
U$13, U$14, U$15, U$16: HOLE#4; HOLE-#4
X1: C-GRID-04-70543; 70543-04; PARTNUM EXCLUDE
X2, X3, X4: SPRING-CONTACT

Connections:
GND: J1.6, U$1.GNDA (GND), U$1.GNDB (GND), U$2.GNDA (GND), U$2.GNDB (GND), U$3.GNDA (GND), U$3.GNDB (GND), U$4.GNDA (GND), U$4.GNDB (GND), U$5.GNDA (GND), U$5.GNDB (GND), U$6.GNDA (GND), U$6.GNDB (GND), U$10.1, U$11.1, U$12.1, U$17.1, X1.1
unnamed: J1.1, X4.P$1
unnamed: J1.5, X3.P$1
unnamed: J1.2, X2.P$1
SCL: J1.3, U$1.SCLA (SCL/SCK), U$1.SCLB (SCL/SCK), U$2.SCLA (SCL/SCK), U$2.SCLB (SCL/SCK), U$3.SCLA (SCL/SCK), U$3.SCLB (SCL/SCK), U$4.SCLA (SCL/SCK), U$4.SCLB (SCL/SCK), U$5.SCLA (SCL/SCK), U$5.SCLB (SCL/SCK), U$6.SCLA (SCL/SCK), U$6.SCLB (SCL/SCK), U$10.4, U$11.4, U$12.4, U$17.4, X1.4
SDA: J1.4, U$1.SDAA (SDA/MOSI), U$1.SDAB (SDA/MOSI), U$2.SDAA (SDA/MOSI), U$2.SDAB (SDA/MOSI), U$3.SDAA (SDA/MOSI), U$3.SDAB (SDA/MOSI), U$4.SDAA (SDA/MOSI), U$4.SDAB (SDA/MOSI), U$5.SDAA (SDA/MOSI), U$5.SDAB (SDA/MOSI), U$6.SDAA (SDA/MOSI), U$6.SDAB (SDA/MOSI), U$10.2, U$11.2, U$12.2, U$17.2, X1.2
VCC: U$1.VCCA (VCC), U$1.VCCB (VCC), U$2.VCCA (VCC), U$2.VCCB (VCC), U$3.VCCA (VCC), U$3.VCCB (VCC), U$4.VCCA (VCC), U$4.VCCB (VCC), U$5.VCCA (VCC), U$5.VCCB (VCC), U$6.VCCA (VCC), U$6.VCCB (VCC), U$10.3, U$11.3, U$12.3, U$17.3, X1.3

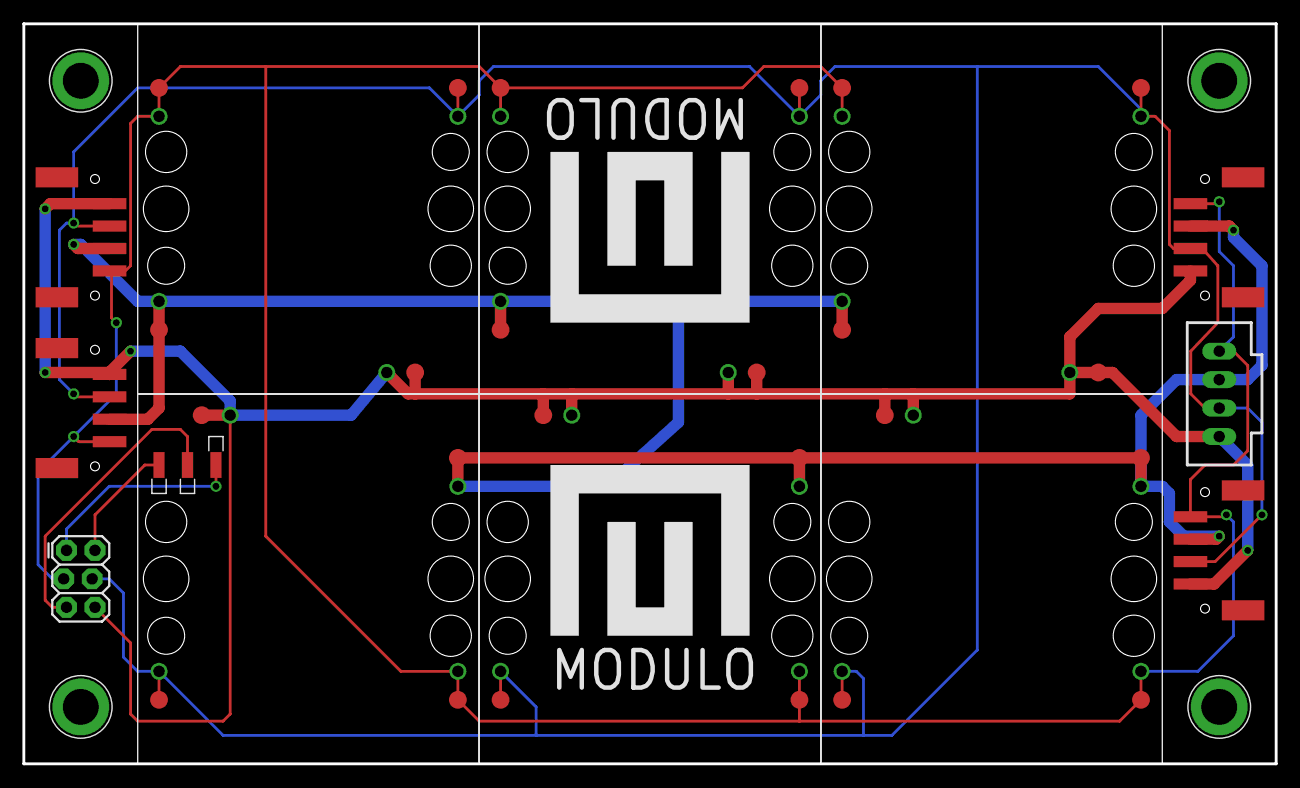
[picture p67: board MagBase.brd from above]

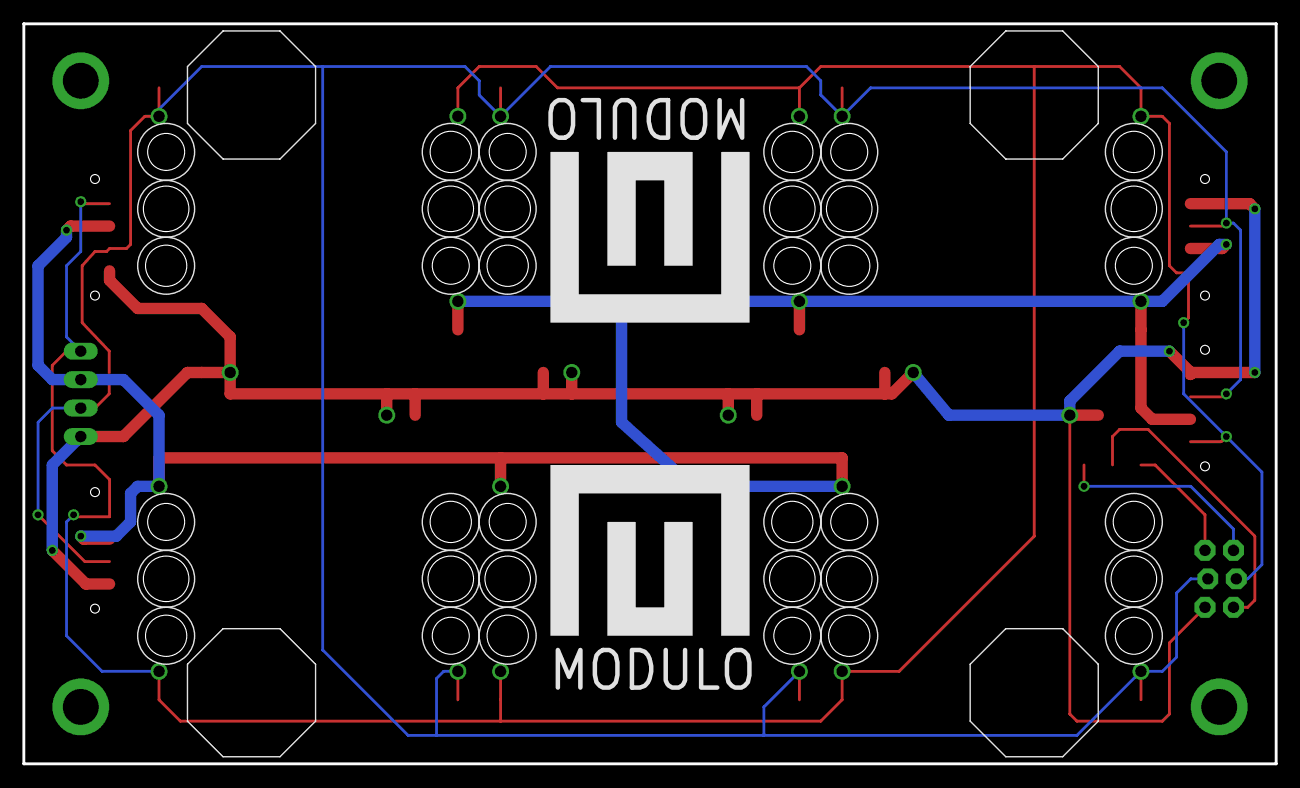
[picture p68: board MagBase.brd from below]

Board: 2 copper layers, 111.8 x 66.0 mm, 23 parts (4 on the bottom side), 7 nets.
