modulolabs/pcb/NavButtons/NavButtons.brd

## EAGLE design NavButtons/NavButtons.brd (2014-11-25)

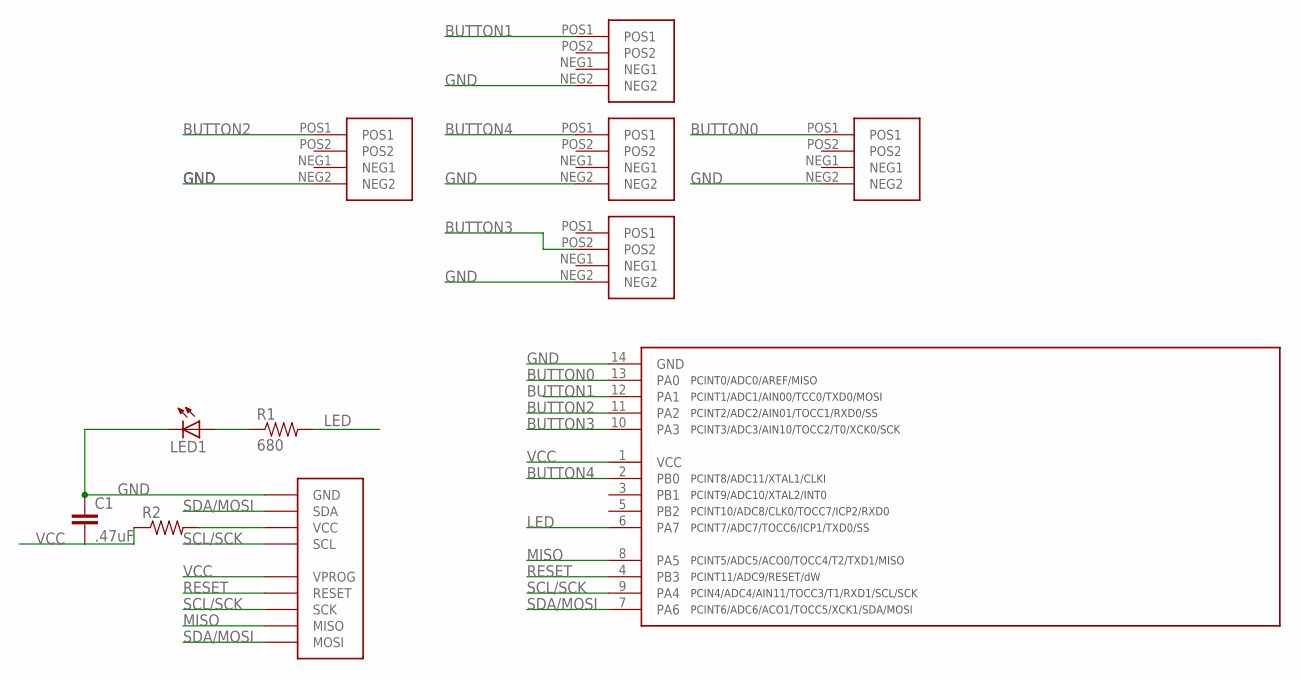
[picture p69: schematic NavButtons.sch]

Parts:
B1, B3, B4, B5, B7: TACT-SWITCH; MJTP1138
C1: .47uF; 0805
LED1: LEDCHIP-LED0805; CHIP-LED0805
R1: 680; 0805
R2: RESISTOR0805-RES; 0805
U$1: TINY841; SOIC14
U$2: FOOTPRINTFOOTPRINT-2; FOOTPRINT2

Connections:
BUTTON0: B5.POS1, U$1.13 (PA0)
BUTTON1: B1.POS1, U$1.12 (PA1)
BUTTON2: B3.POS1, U$1.11 (PA2)
BUTTON3: B7.POS2, U$1.10 (PA3)
BUTTON4: B4.POS1, U$1.2 (PB0)
GND: B1.NEG2, B3.NEG2, B4.NEG2, B5.NEG2, B7.NEG2, C1.1, LED1.C, U$1.14 (GND), U$2.BUS0 (GND)
LED: R1.2, U$1.6 (PA7)
MISO: U$1.8 (PA5), U$2.PROG3 (MISO)
unnamed: R2.2, U$2.BUS2 (VCC)
unnamed: LED1.A, R1.1
RESET: U$1.4 (PB3), U$2.PROG1 (RESET)
SCL/SCK: U$1.9 (PA4), U$2.BUS3 (SCL), U$2.PROG2 (SCK)
SDA/MOSI: U$1.7 (PA6), U$2.BUS1 (SDA), U$2.PROG4 (MOSI)
VCC: C1.2, R2.1, U$1.1 (VCC), U$2.PROG0 (VPROG)

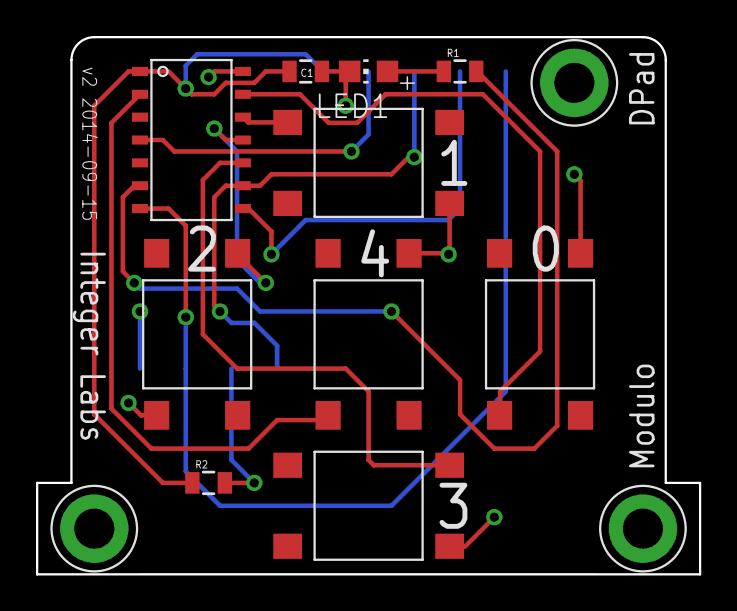
[picture p70: board NavButtons.brd from above]

Board: 2 copper layers, 36.8 x 29.8 mm, 11 parts (0 on the bottom side), 14 nets.
