modulolabs/pcb/AC/AC.brd

## EAGLE design AC/AC.brd (2014-10-15)

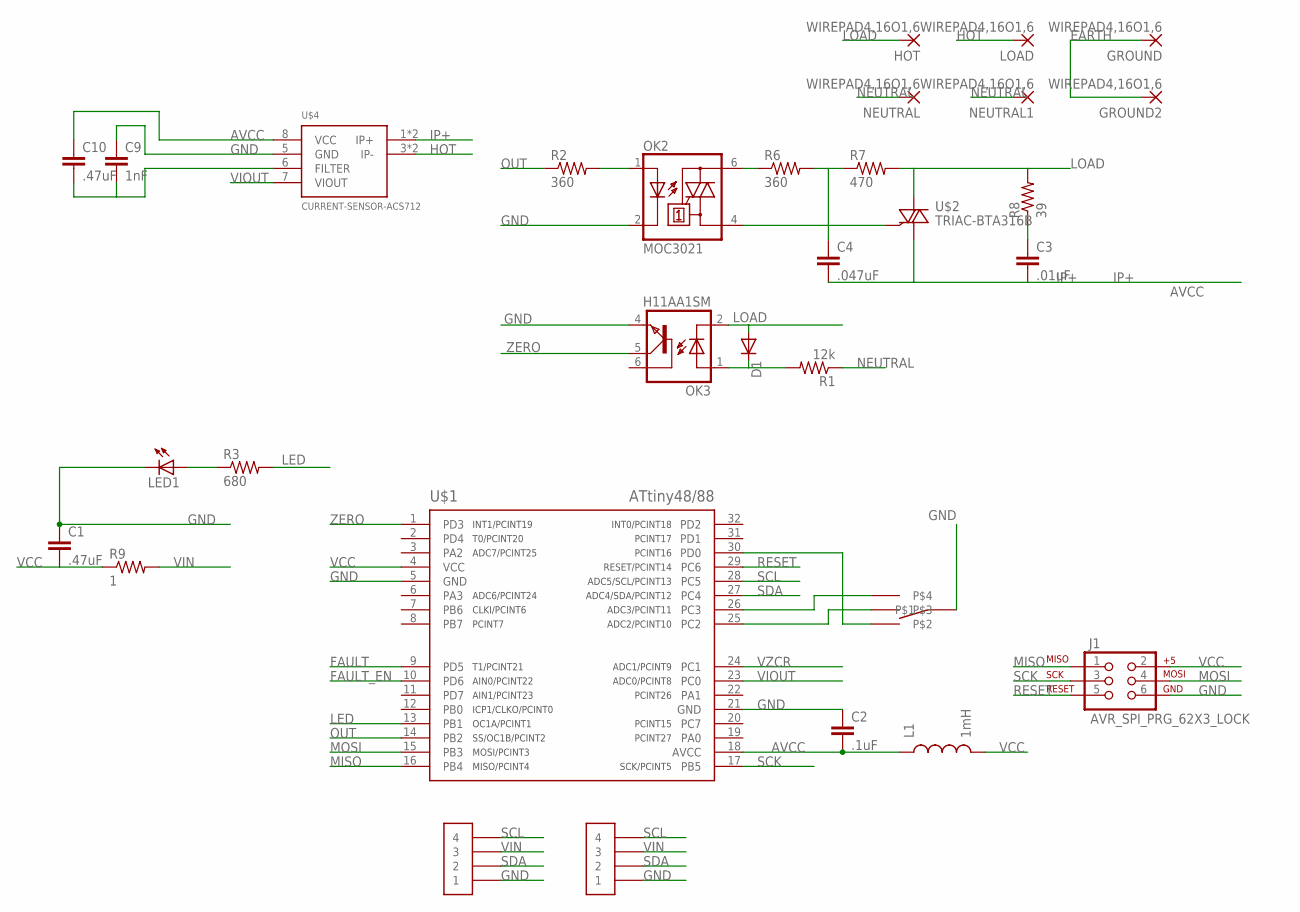
[picture p71: schematic AC.sch]

Parts:
C1, C10: .47uF; 0805
C2: .1uF; 0805
C3: .01uF; C1206
C4: .047uF; C1206
C9: 1nF; 0805
D1: DIODESMA; SMA-DIODE
GROUND, GROUND2: WIREPAD4,16O1,6; 4,16O1,6
HOT: WIREPAD4,16O1,6; 4,16O1,6
J1: AVR_SPI_PRG_62X3_LOCK; 2X3_LOCK
JP1, JP2: HEADER-1X4MOLEX-SL; HEADER-1X4-MOLEX-SL
L1: 1mH; 1007
LED1: LED5MM
LOAD: WIREPAD4,16O1,6; 4,16O1,6
NEUTRAL, NEUTRAL1: WIREPAD4,16O1,6; 4,16O1,6
OK2: MOC3021; DIL6-SMD
OK3: H11AA1SM; DIL6-SMD
R1: 12k; R1206
R2: 360; 0805
R3: 680; 0805
R6: 360; R1206
R7: 470; R1206
R8: 39; R1206
R9: 1; 0805
U$1: ATTINY48/88-TQFP; TQFP-32
U$2: TRIAC-BTA316B; D2PACK
U$3: SWITCH-SP3T; SWITCH-SLIDE-APEM-MHS133K
U$4: CURRENT-SENSOR-ACS712; SOIC-8

Connections:
AVCC: C2.2, C10.1, L1.1, U$1.18 (AVCC), U$4.8 (VCC)
EARTH: GROUND.1, GROUND2.1
FAULT: U$1.9 (PD5)
FAULT_EN: U$1.10 (PD6)
GND: C1.1, C2.1, C9.1, J1.6, JP1.P$1 (1), JP2.P$1 (1), LED1.K (C), OK2.2 (C), OK3.4 (EMI), U$1.5 (GND), U$1.21 (GND), U$3.P2, U$4.5 (GND)
HOT: LOAD.1, U$4.3 (IP-), U$4.4 (IP-)
IP+: C3.2, C4.2, U$2.1 (A1), U$4.1 (IP+), U$4.2 (IP+)
LED: R3.2, U$1.13 (PB1)
LOAD: D1.A, HOT.1, OK3.2 (C), R7.2, R8.2, U$2.2 (A2)
MISO: J1.1, U$1.16 (PB4)
MOSI: J1.4, U$1.15 (PB3)
unnamed: OK2.4 (A1), U$2.3 (G)
unnamed: D1.C, OK3.1 (A), R1.2
unnamed: OK2.1 (A), R2.2
unnamed: OK2.6 (A2), R6.1
unnamed: LED1.A, R3.1
unnamed: U$1.25 (PC2), U$3.P3
unnamed: U$1.26 (PC3), U$3.P4
unnamed: U$1.30 (PD0), U$3.P1
unnamed: C9.2, C10.2, U$4.6 (FILTER)
unnamed: C4.1, R6.2, R7.1
unnamed: C3.1, R8.1
NEUTRAL: NEUTRAL.1, NEUTRAL1.1, R1.1
OUT: R2.1, U$1.14 (PB2)
RESET: J1.5, U$1.29 (PC6)
SCK: J1.3, U$1.17 (PB5)
SCL: JP1.P$4 (4), JP2.P$4 (4), U$1.28 (PC5)
SDA: JP1.P$2 (2), JP2.P$2 (2), U$1.27 (PC4)
VCC: C1.2, J1.2, L1.2, R9.1, U$1.4 (VCC)
VIN: JP1.P$3 (3), JP2.P$3 (3), R9.2
VIOUT: U$1.23 (PC0), U$4.7 (VIOUT)
VZCR: U$1.24 (PC1)
ZERO: OK3.5 (COL), U$1.1 (PD3)

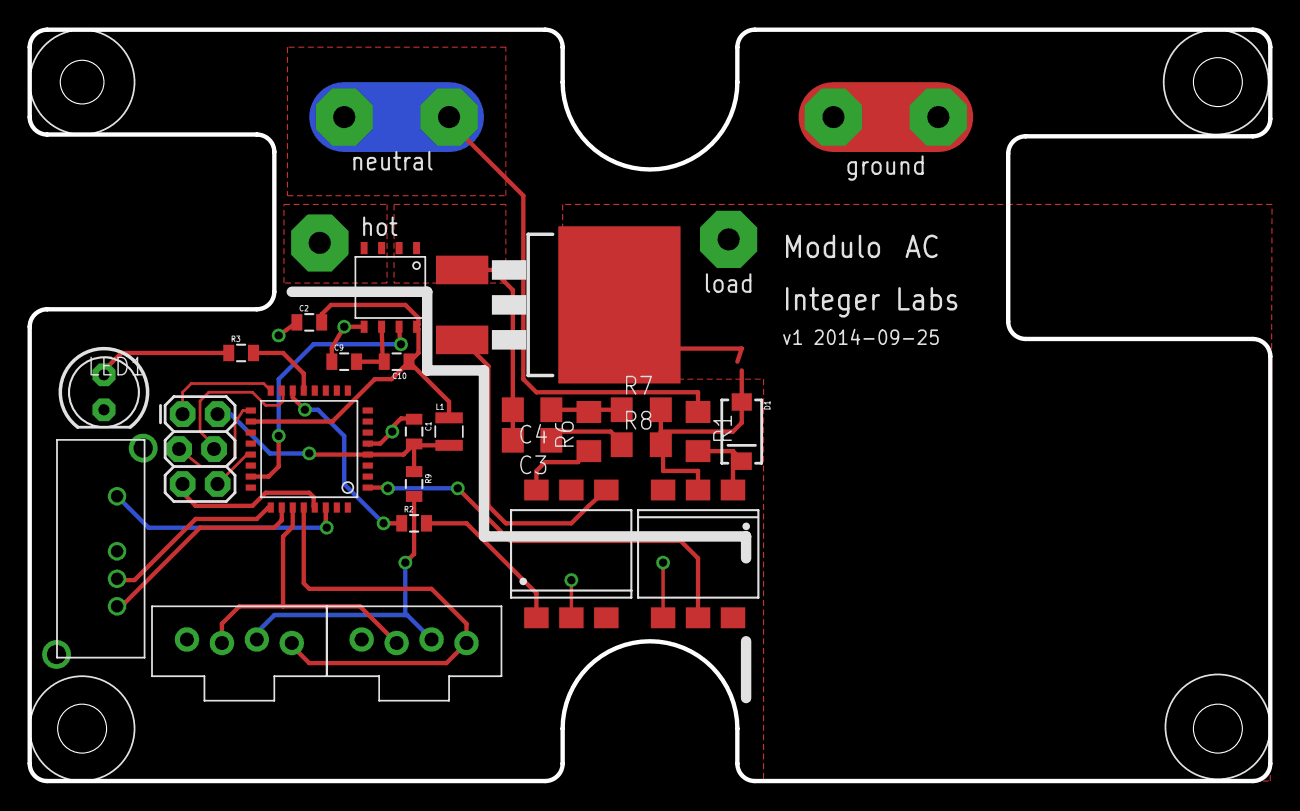
[picture p72: board AC.brd from above]

Board: 2 copper layers, 90.2 x 54.6 mm, 31 parts (0 on the bottom side), 30 nets.
