modulolabs/pcb/uC/SAMD21/SAMD21.brd

## EAGLE design uC/SAMD21/SAMD21.brd (2014-08-30)

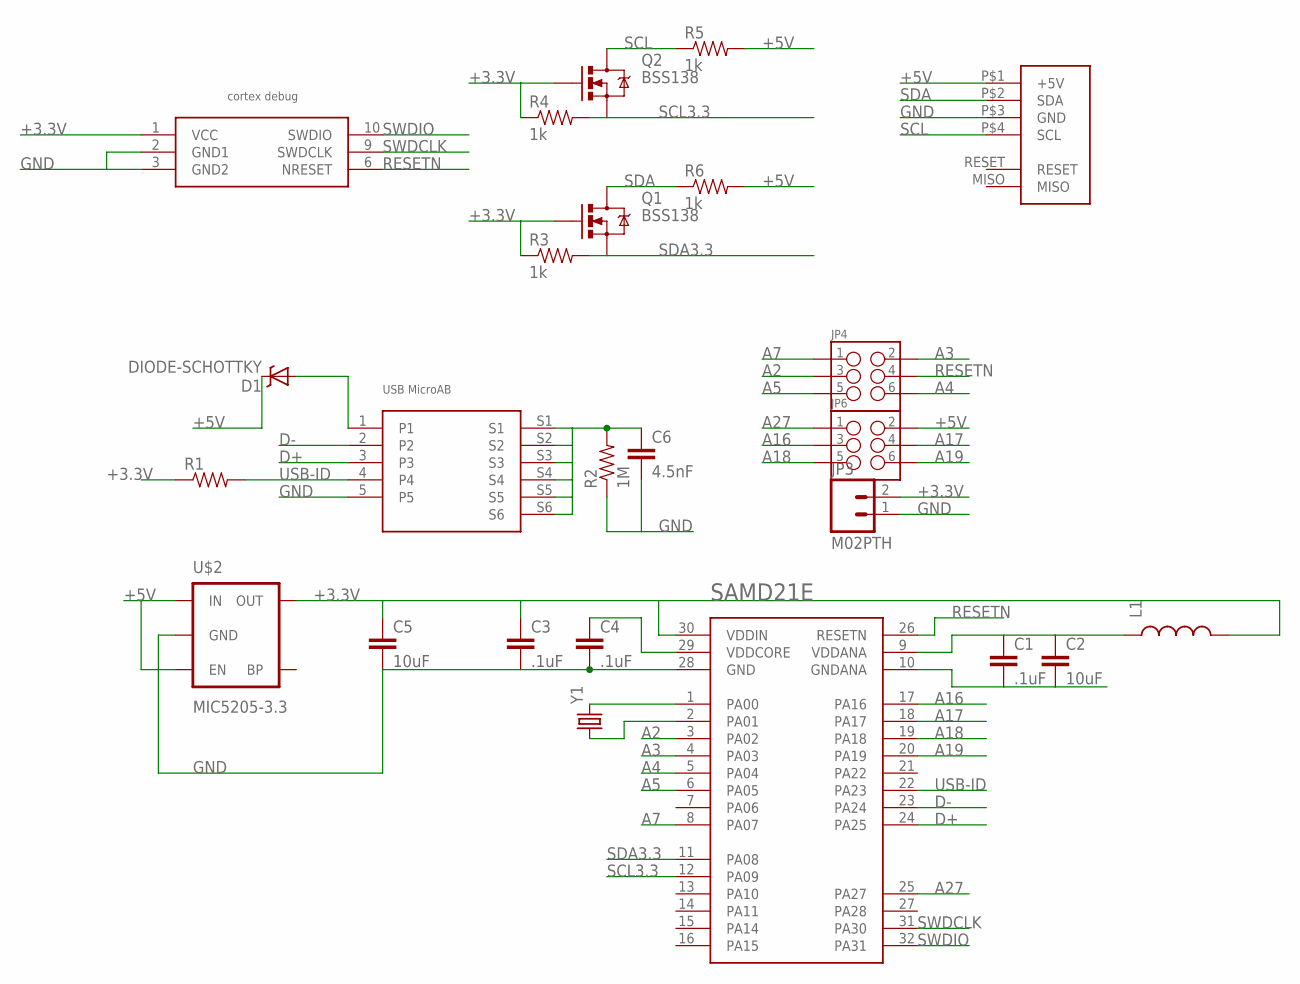
[picture p73: schematic SAMD21.sch]

Parts:
C1, C3, C4: .1uF; 0805
C2, C5: 10uF; 0805
C6: 4.5nF; 0805
D1: DIODE-SCHOTTKY; SOD-523
JP3: M02PTH; 1X02
JP4, JP6: M03X22X3_SILK_SM; 2X3
L1: INDUCTOR0805; 0805
Q1, Q2: BSS138; SOT23
R1: RESISTOR0805-RES; 0805
R2: 1M; 0805
R3, R4, R5, R6: 1k; 0805
U$1: SAMD21E; TQFP-32
U$2: MIC5205-3.3; SOT23-5
U$3: USB-MICRO-AB; MOLEX-MICROAB
U$4: FOOTPRINT
U$5: CORTEX-DEBUG; HEADER-10-.05
Y1: CRYSTALTXC-7A; CRYSTAL-TXC-7A

Connections:
+3.3V: C3.1, C5.1, JP3.2, L1.2, Q1.1 (G), Q2.1 (G), R1.1, R3.1, R4.1, U$1.30 (VDDIN), U$2.5 (OUT), U$5.1 (VCC)
+5V: D1.C, JP6.2, R5.2, R6.2, U$2.1 (IN), U$2.3 (EN), U$4.P$1 (+5V)
A2: JP4.3, U$1.3 (PA02)
A3: JP4.2, U$1.4 (PA03)
A4: JP4.6, U$1.5 (PA04)
A5: JP4.5, U$1.6 (PA05)
A7: JP4.1, U$1.8 (PA07)
A16: JP6.3, U$1.17 (PA16)
A17: JP6.4, U$1.18 (PA17)
A18: JP6.5, U$1.19 (PA18)
A19: JP6.6, U$1.20 (PA19)
A27: JP6.1, U$1.25 (PA27)
D+: U$1.24 (PA25), U$3.3
D-: U$1.23 (PA24), U$3.2
GND: C3.2, C4.2, C5.2, C6.2, JP3.1, R2.1, U$1.28 (GND), U$2.2 (GND), U$3.5, U$4.P$3 (GND), U$5.2 (GND1), U$5.3 (GND2)
unnamed: C1.1, C2.1, L1.1, U$1.9 (VDDANA)
unnamed: C1.2, C2.2, U$1.10 (GNDANA)
unnamed: C6.1, R2.2, U$3.S1, U$3.S2, U$3.S3, U$3.S4, U$3.S5, U$3.S6
unnamed: D1.A, U$3.1
unnamed: C4.1, U$1.29 (VDDCORE)
unnamed: U$1.1 (PA00), Y1.P$2 (2)
unnamed: U$1.2 (PA01), Y1.P$1 (1)
RESETN: JP4.4, U$1.26 (RESETN), U$5.6 (NRESET)
SCL: Q2.3 (D), R5.1, U$4.P$4 (SCL)
SCL3.3: Q2.2 (S), R4.2, U$1.12 (PA09)
SDA: Q1.3 (D), R6.1, U$4.P$2 (SDA)
SDA3.3: Q1.2 (S), R3.2, U$1.11 (PA08)
SWDCLK: U$1.31 (PA30), U$5.9 (SWDCLK)
SWDIO: U$1.32 (PA31), U$5.10 (SWDIO)
USB-ID: R1.2, U$1.22 (PA23), U$3.4

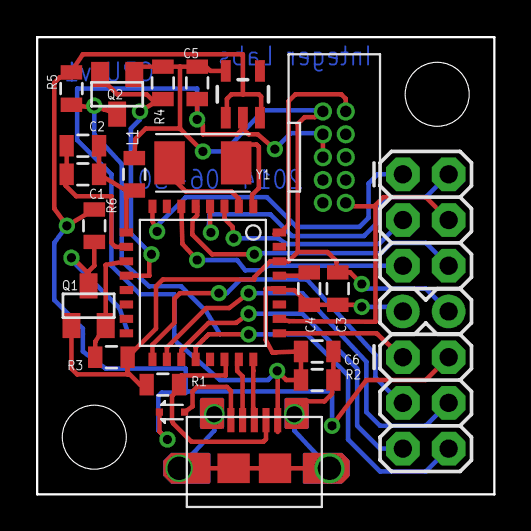
[picture p74: board SAMD21.brd from above]

Board: 2 copper layers, 25.4 x 25.4 mm, 25 parts (0 on the bottom side), 30 nets.
