modulolabs/pcb/DC/TB6612FNG/TB6612FNG.brd

## EAGLE design DC/TB6612FNG/TB6612FNG.brd (2014-08-30)

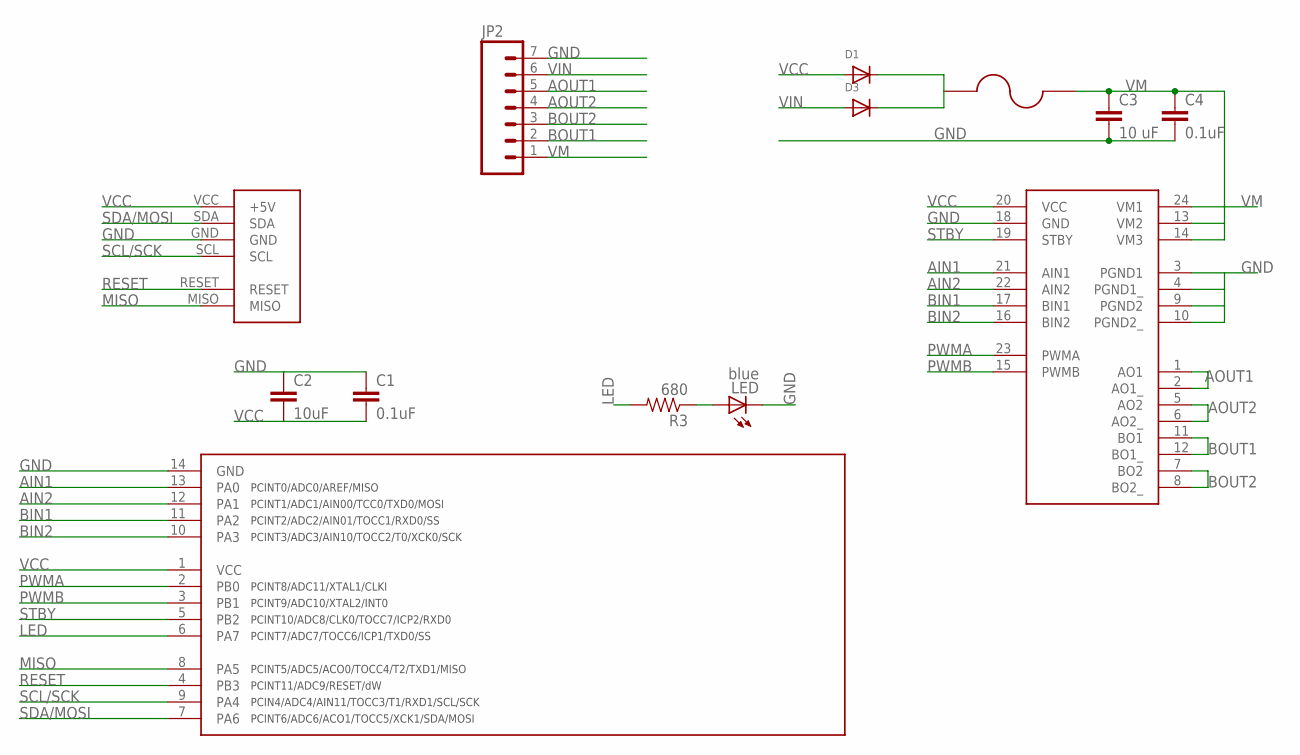
[picture p75: schematic TB6612FNG.sch]

Parts:
C1, C4: 0.1uF; 0805
C2: 10uF; 0805
C3: 10 uF; 0805
D1, D3: DIODESOD-123; SOD-123
JP2: M07; 1X07
LED: blue; CHIPLED_1206
R3: 680; 0805
U$1: TB6612FNG; SSOP-24
U$2: FUSE; 1812
U$3: TINY841; SOIC14
U$4: FOOTPRINTFOOTPRINT-2; FOOTPRINT2

Connections:
AIN1: U$1.21 (AIN1), U$3.13 (PA0)
AIN2: U$1.22 (AIN2), U$3.12 (PA1)
AOUT1: JP2.5, U$1.1 (AO1), U$1.2 (AO1_)
AOUT2: JP2.4, U$1.5 (AO2), U$1.6 (AO2_)
BIN1: U$1.17 (BIN1), U$3.11 (PA2)
BIN2: U$1.16 (BIN2), U$3.10 (PA3)
BOUT1: JP2.2, U$1.11 (BO1), U$1.12 (BO1_)
BOUT2: JP2.3, U$1.7 (BO2), U$1.8 (BO2_)
GND: C1.1, C2.1, C3.2, C4.2, JP2.7, LED.C, U$1.3 (PGND1), U$1.4 (PGND1_), U$1.9 (PGND2), U$1.10 (PGND2_), U$1.18 (GND), U$3.14 (GND), U$4.GND
LED: R3.2, U$3.6 (PA7)
MISO: U$3.8 (PA5), U$4.MISO
unnamed: D1.C, D3.C, U$2.P$1 (1)
unnamed: LED.A, R3.1
PWMA: U$1.23 (PWMA), U$3.2 (PB0)
PWMB: U$1.15 (PWMB), U$3.3 (PB1)
RESET: U$3.4 (PB3), U$4.RESET
SCL/SCK: U$3.9 (PA4), U$4.SCL
SDA/MOSI: U$3.7 (PA6), U$4.SDA
STBY: U$1.19 (STBY), U$3.5 (PB2)
VCC: C1.2, C2.2, D1.A, U$1.20 (VCC), U$3.1 (VCC), U$4.VCC (+5V)
VIN: D3.A, JP2.6
VM: C3.1, C4.1, JP2.1, U$1.13 (VM2), U$1.14 (VM3), U$1.24 (VM1), U$2.P$2 (2)

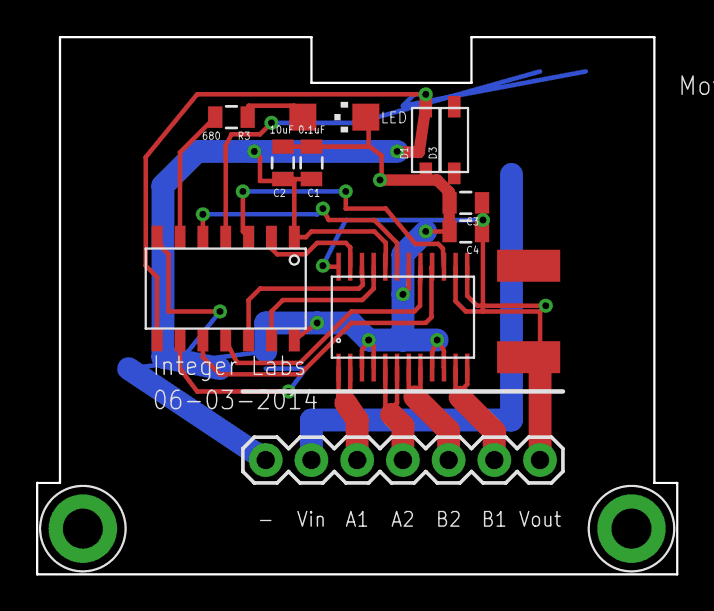
[picture p76: board TB6612FNG.brd from above]

Board: 2 copper layers, 35.6 x 29.8 mm, 13 parts (0 on the bottom side), 22 nets.
