modulolabs/pcb/Motor/Motor.brd

## EAGLE design Motor/Motor.brd (2014-08-22)

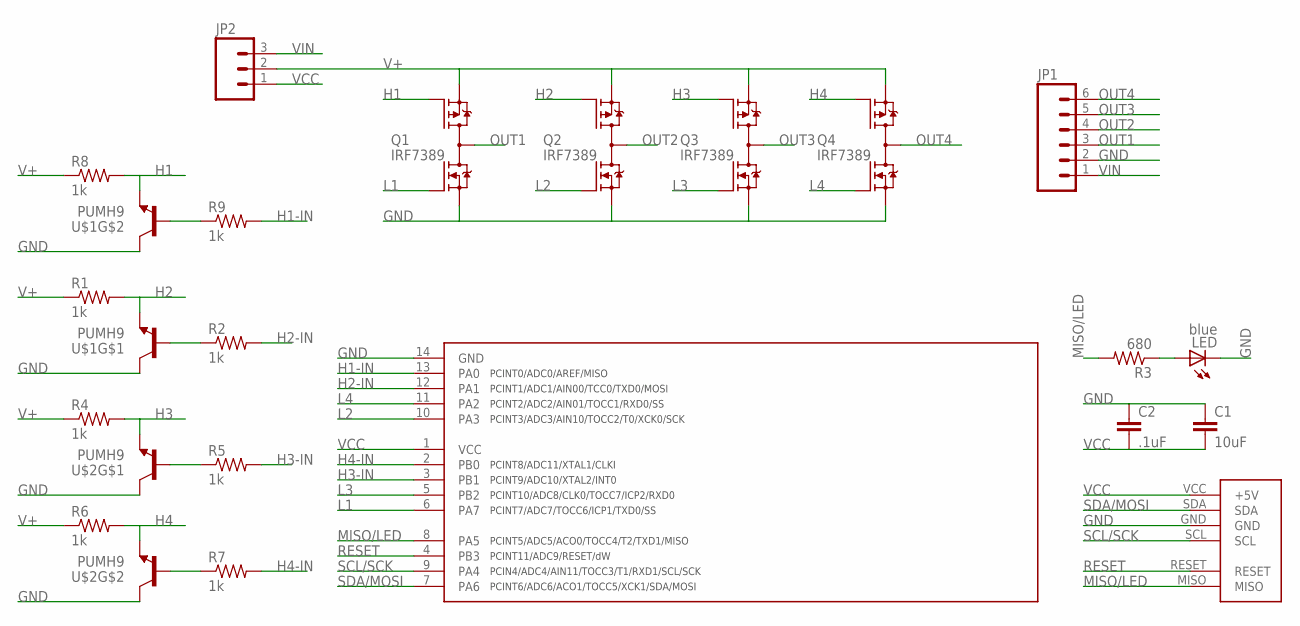
[picture p77: schematic Motor.sch]

Parts:
C1: 10uF; 0805
C2: .1uF; 0805
JP1: M063.5MM-6; SCREWTERMINAL-3.5MM-6
JP2: M03LOCK_NO_SILK; 1X03_LOCK_NO_SILK
LED: blue; CHIPLED_1206
Q1, Q2, Q3, Q4: IRF7389; SO08-IRF
R1, R2, R4, R5, R6, R7, R8, R9: 1k; 0805
R3: 680; 0805
U$1, U$2: PUMH9; SOT363
U$3: TINY841; SOIC14
U$4: FOOTPRINTFOOTPRINT-2; FOOTPRINT2

Connections:
GND: C1.1, C2.1, JP1.2, LED.C, Q1.1 (N-S), Q2.1 (N-S), Q3.1 (N-S), Q4.1 (N-S), U$1.3 (C), U$1.6 (C), U$2.3 (C), U$2.6 (C), U$3.14 (GND), U$4.GND
H1: Q1.4 (P-G), R8.2, U$1.1 (E)
H1-IN: R9.2, U$3.13 (PA0)
H2: Q2.4 (P-G), R1.2, U$1.4 (E)
H2-IN: R2.2, U$3.12 (PA1)
H3: Q3.4 (P-G), R4.2, U$2.4 (E)
H3-IN: R5.2, U$3.3 (PB1)
H4: Q4.4 (P-G), R6.2, U$2.1 (E)
H4-IN: R7.2, U$3.2 (PB0)
L1: Q1.2 (N-G), U$3.6 (PA7)
L2: Q2.2 (N-G), U$3.10 (PA3)
L3: Q3.2 (N-G), U$3.5 (PB2)
L4: Q4.2 (N-G), U$3.11 (PA2)
MISO/LED: R3.2, U$3.8 (PA5), U$4.MISO
unnamed: R2.1, U$1.5 (B)
unnamed: R5.1, U$2.5 (B)
unnamed: LED.A, R3.1
unnamed: R7.1, U$2.2 (B)
unnamed: R9.1, U$1.2 (B)
OUT1: JP1.3, Q1.5 (D), Q1.6 (D), Q1.7 (D), Q1.8 (D)
OUT2: JP1.4, Q2.5 (D), Q2.6 (D), Q2.7 (D), Q2.8 (D)
OUT3: JP1.5, Q3.5 (D), Q3.6 (D), Q3.7 (D), Q3.8 (D)
OUT4: JP1.6, Q4.5 (D), Q4.6 (D), Q4.7 (D), Q4.8 (D)
RESET: U$3.4 (PB3), U$4.RESET
SCL/SCK: U$3.9 (PA4), U$4.SCL
SDA/MOSI: U$3.7 (PA6), U$4.SDA
V+: JP2.2, Q1.3 (P-S), Q2.3 (P-S), Q3.3 (P-S), Q4.3 (P-S), R1.1, R4.1, R6.1, R8.1
VCC: C1.2, C2.2, JP2.1, U$3.1 (VCC), U$4.VCC (+5V)
VIN: JP1.1, JP2.3

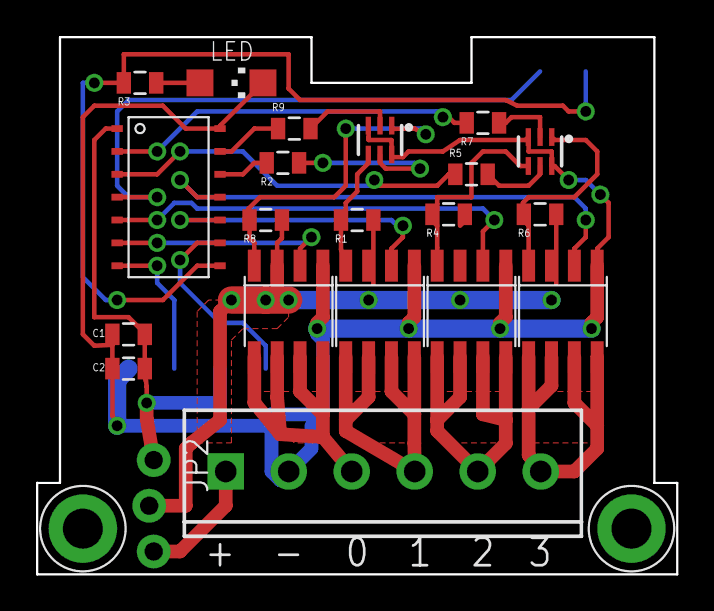
[picture p78: board Motor.brd from above]

Board: 2 copper layers, 35.6 x 29.8 mm, 22 parts (0 on the bottom side), 29 nets.
