modulolabs/pcb/uC/ProMicro/Pro_Micro.brd

## EAGLE design uC/ProMicro/Pro_Micro.brd (2014-06-20)

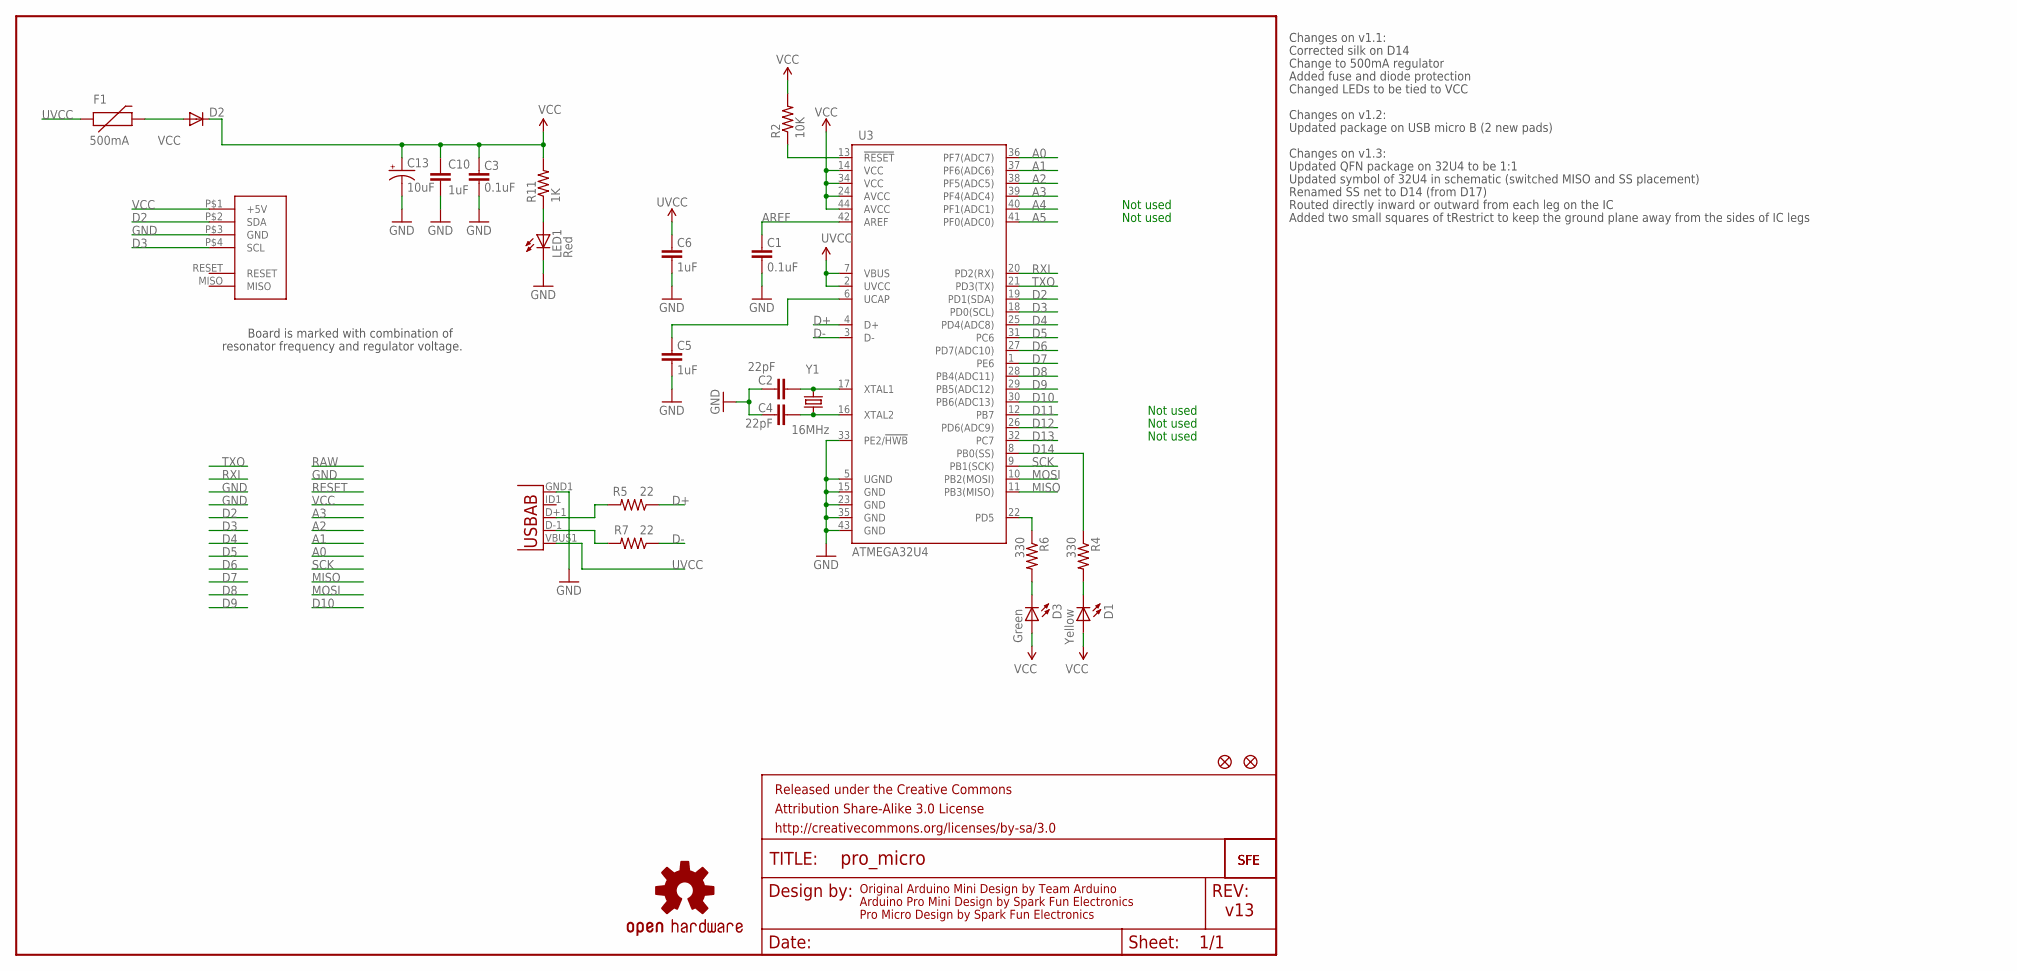
[picture p79: schematic Pro_Micro.sch]

Parts:
C1, C3: 0.1uF; 0603-CAP
C2, C4: 22pF; 0603-CAP
C5, C6, C10: 1uF; 0603-CAP
C13: 10uF; EIA3216
D1: Yellow; LED-0603
D2: DIODESOD; SOD-323
D3: Green; LED-0603
F1: 500mA; PTC-1206
FRAME1: FRAME-LETTER; CREATIVE_COMMONS
JP1, JP2: FIDUCIALUFIDUCIAL; MICRO-FIDUCIAL
LED1: Red; LED-0603
R2: 10K; 0603-RES
R4, R6: 330; 0603-RES
R5, R7: 22; 0603-RES
R11: 1K; 0603-RES
U3: ATMEGA32U4; QFN-44-NOPAD_1:1-OUTFAKES
U$1: LOGO-SFESK; SFE-LOGO-FLAME
U$2: FOOTPRINT
U$3: OSHW-LOGOS; OSHW-LOGO-S
U$11: LOGO-SFENEW; SFE-NEW-WEBLOGO
X1: USB-ABIN&OUT; USB-AB-MICRO-SMD-V03-IN&OUT
Y1: 16MHz; CRYSTAL-SMD-5X3

Connections:
A0: U3.36 (PF7(ADC7))
A1: U3.37 (PF6(ADC6))
A2: U3.38 (PF5(ADC5))
A3: U3.39 (PF4(ADC4))
A4: U3.40 (PF1(ADC1))
A5: U3.41 (PF0(ADC0))
AREF: C1.2, U3.42 (AREF)
D2: U3.19 (PD1(SDA)), U$2.P$2 (SDA)
D3: U3.18 (PD0(SCL)), U$2.P$4 (SCL)
D4: U3.25 (PD4(ADC8))
D5: U3.31 (PC6)
D6: U3.27 (PD7(ADC10))
D7: U3.1 (PE6)
D8: U3.28 (PB4(ADC11))
D9: U3.29 (PB5(ADC12))
D10: U3.30 (PB6(ADC13))
D11: U3.12 (PB7)
D12: U3.26 (PD6(ADC9))
D13: U3.32 (PC7)
D14: R4.1, U3.8 (PB0(SS))
D+: R5.1, U3.4 (D+)
D-: R7.1, U3.3 (D-)
GND: C1.1, C2.2, C3.1, C4.2, C5.1, C6.1, C10.2, C13.C (-), LED1.C, U3.5 (UGND), U3.15 (GND), U3.23 (GND), U3.33 (PE2/!HWB), U3.35 (GND), U3.43 (GND), U$2.P$3 (GND), X1.GND1 (GND)
MISO: U3.11 (PB3(MISO))
MOSI: U3.10 (PB2(MOSI))
unnamed: C4.1, U3.16 (XTAL2), Y1.1
unnamed: C2.1, U3.17 (XTAL1), Y1.3 (2)
unnamed: C5.2, U3.6 (UCAP)
unnamed: D1.C, R4.2
unnamed: R7.2, X1.D-1 (D-)
unnamed: D3.C, R6.2
unnamed: R5.2, X1.D+1 (D+)
unnamed: D2.2 (A), F1.2
unnamed: LED1.A, R11.1
RESET: R2.1, U3.13 (!RESET)
RXI: U3.20 (PD2(RX))
SCK: U3.9 (PB1(SCK))
TXLED: R6.1, U3.22 (PD5)
TXO: U3.21 (PD3(TX))
UVCC: C6.2, F1.1, U3.2 (UVCC), U3.7 (VBUS), X1.VBUS1 (VBUS)
VCC: C3.2, C10.1, C13.A (+), D1.A, D2.1 (C), D3.A, R2.2, R11.2, U3.14 (VCC), U3.24 (AVCC), U3.34 (VCC), U3.44 (AVCC), U$2.P$1 (+5V)

Notes on the sheet:
Original Arduino Mini Design by Team Arduino
Arduino Pro Mini Design by Spark Fun Electronics
Board is marked with combination of
resonator frequency and regulator voltage.
Not used
Pro Micro Design by Spark Fun Electronics
Changes on v1.1:
Corrected silk on D14
Change to 500mA regulator
Added fuse and diode protection
Changed LEDs to be tied to VCC
Changes on v1.2:
Updated package on USB micro B (2 new pads)
Changes on v1.3:
Updated QFN package on 32U4 to be 1:1
Updated symbol of 32U4 in schematic (switched MISO and SS placement)
Renamed SS net to D14 (from D17)
Routed directly inward or outward from each leg on the IC
Added two small squares of tRestrict to keep the ground plane away from the sides of IC legs
v13

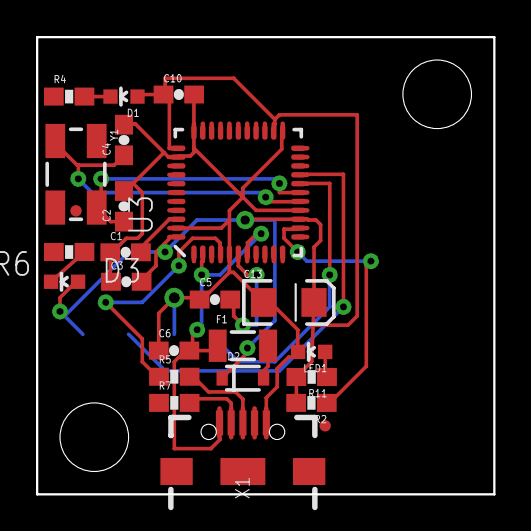
[picture p80: board Pro_Micro.brd from above]

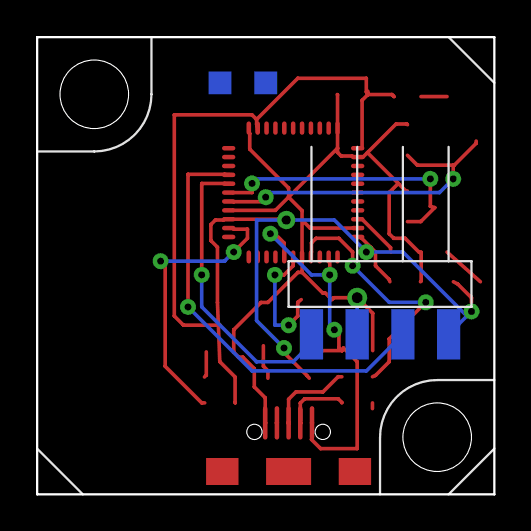
[picture p81: board Pro_Micro.brd from below]

Board: 2 copper layers, 25.4 x 25.4 mm, 29 parts (2 on the bottom side), 20 nets.
