modulolabs/pcb/DC/DRV8839/DRV8839.brd

## EAGLE design DC/DRV8839/DRV8839.brd (2014-06-20)

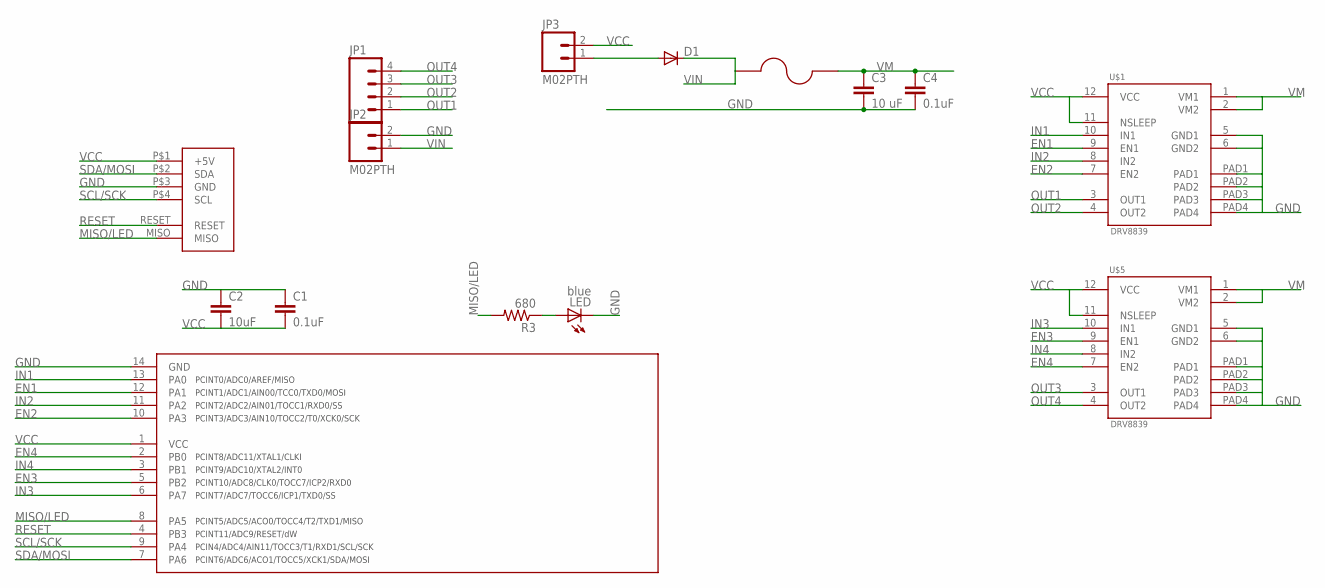
[picture p82: schematic DRV8839.sch]

Parts:
C1, C4: 0.1uF; 0805
C2: 10uF; 0805
C3: 10 uF; 0805
D1: DIODESMC/DO-214AB; SMC
JP1: M04PTH; 1X04
JP2, JP3: M02PTH; 1X02
LED: blue; CHIPLED_1206
R3: 680; 0805
U$1, U$5: DRV8839; WSON-POWERPAD-12
U$2: FUSE; 1812
U$3: TINY841; SOIC14
U$4: FOOTPRINT

Connections:
EN1: U$1.9 (EN1), U$3.12 (PA1)
EN2: U$1.7 (EN2), U$3.10 (PA3)
EN3: U$3.5 (PB2), U$5.9 (EN1)
EN4: U$3.2 (PB0), U$5.7 (EN2)
GND: C1.1, C2.1, C3.2, C4.2, JP2.2, LED.C, U$1.5 (GND1), U$1.6 (GND2), U$1.PAD1, U$1.PAD2, U$1.PAD3, U$1.PAD4, U$3.14 (GND), U$4.P$3 (GND), U$5.5 (GND1), U$5.6 (GND2), U$5.PAD1, U$5.PAD2, U$5.PAD3, U$5.PAD4
IN1: U$1.10 (IN1), U$3.13 (PA0)
IN2: U$1.8 (IN2), U$3.11 (PA2)
IN3: U$3.6 (PA7), U$5.10 (IN1)
IN4: U$3.3 (PB1), U$5.8 (IN2)
MISO/LED: R3.2, U$3.8 (PA5), U$4.MISO
unnamed: D1.A, JP3.1
unnamed: LED.A, R3.1
OUT1: JP1.1, U$1.3 (OUT1)
OUT2: JP1.2, U$1.4 (OUT2)
OUT3: JP1.3, U$5.3 (OUT1)
OUT4: JP1.4, U$5.4 (OUT2)
RESET: U$3.4 (PB3), U$4.RESET
SCL/SCK: U$3.9 (PA4), U$4.P$4 (SCL)
SDA/MOSI: U$3.7 (PA6), U$4.P$2 (SDA)
VCC: C1.2, C2.2, JP3.2, U$1.11 (NSLEEP), U$1.12 (VCC), U$3.1 (VCC), U$4.P$1 (+5V), U$5.11 (NSLEEP), U$5.12 (VCC)
VIN: D1.C, JP2.1, U$2.P$1 (1)
VM: C3.1, C4.1, U$1.1 (VM1), U$1.2 (VM2), U$2.P$2 (2), U$5.1 (VM1), U$5.2 (VM2)

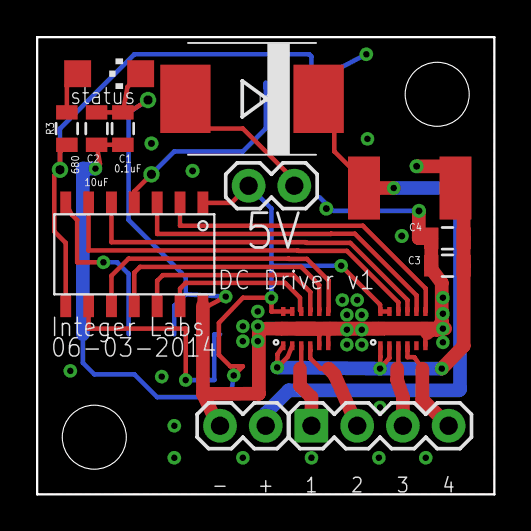
[picture p83: board DRV8839.brd from above]

Board: 2 copper layers, 25.4 x 25.4 mm, 15 parts (0 on the bottom side), 22 nets.
