modulolabs/pcb/Pot/Pot.brd

## EAGLE design Pot/Pot.brd (2014-06-20)

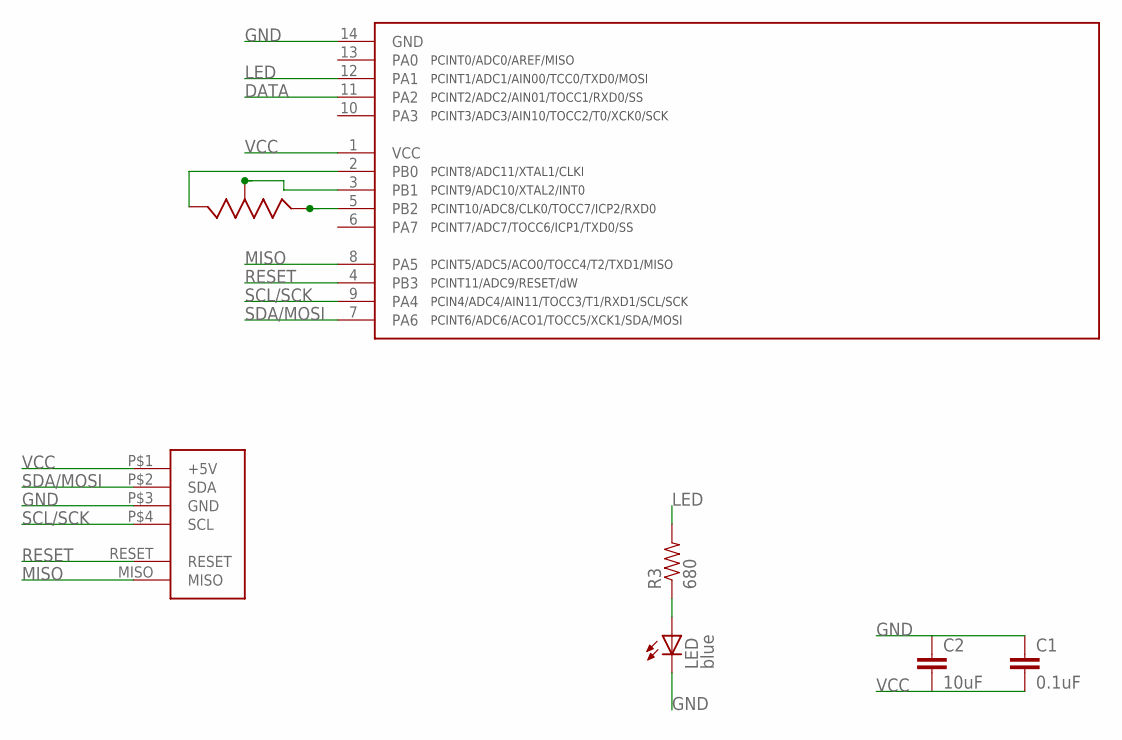
[picture p84: schematic Pot.sch]

Parts:
C1: 0.1uF; 0805
C2: 10uF; 0805
LED: blue; CHIPLED_1206
R3: 680; 0805
U$2: BOURNS_PRS11S; PRS11S
U$3: TINY841; SOIC14
U$4: FOOTPRINT

Connections:
DATA: U$3.11 (PA2)
GND: C1.1, C2.1, LED.C, U$3.14 (GND), U$4.P$3 (GND)
LED: R3.2, U$3.12 (PA1)
MISO: U$3.8 (PA5), U$4.MISO
unnamed: U$2.2 (P1), U$3.5 (PB2)
unnamed: U$2.3 (P2), U$3.3 (PB1)
unnamed: U$2.1 (P3), U$3.2 (PB0)
unnamed: LED.A, R3.1
RESET: U$3.4 (PB3), U$4.RESET
SCL/SCK: U$3.9 (PA4), U$4.P$4 (SCL)
SDA/MOSI: U$3.7 (PA6), U$4.P$2 (SDA)
VCC: C1.2, C2.2, U$3.1 (VCC), U$4.P$1 (+5V)

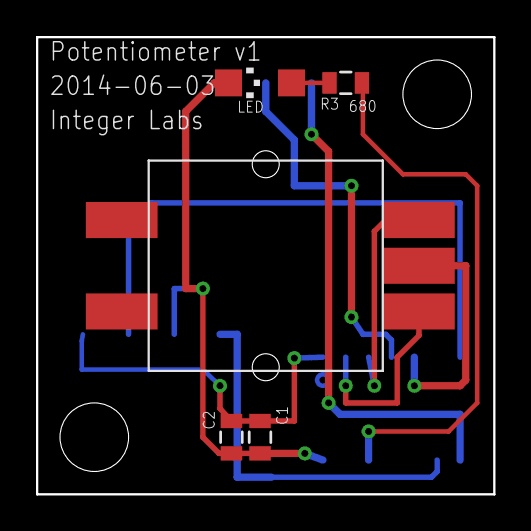
[picture p85: board Pot.brd from above]

Board: 2 copper layers, 25.4 x 25.4 mm, 7 parts (1 on the bottom side), 11 nets.
