modulolabs/pcb/Stepper/A4980/A4980.brd

## EAGLE design Stepper/A4980/A4980.brd (2014-06-20)

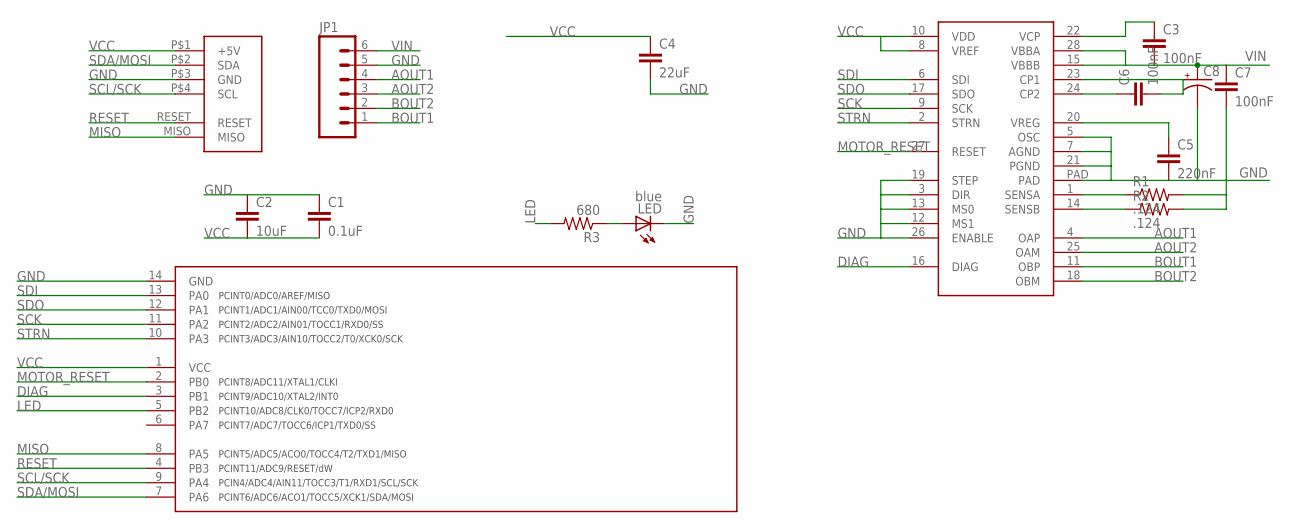
[picture p86: schematic A4980.sch]

Parts:
C1: 0.1uF; 0805
C2: 10uF; 0805
C3, C6, C7: 100nF; 0805
C4: 22uF; 0805
C5: 220nF; 0805
C8: CAP_POLD; PANASONIC_D
JP1: M06SIP; 1X06
LED: blue; CHIPLED_1206
R1, R2: .124; 0805
R3: 680; 0805
U$1: A4980; TSSOP-28
U$3: TINY841; SOIC14
U$4: FOOTPRINT

Connections:
AOUT1: JP1.4, U$1.4 (OAP)
AOUT2: JP1.3, U$1.25 (OAM)
BOUT1: JP1.1, U$1.11 (OBP)
BOUT2: JP1.2, U$1.18 (OBM)
DIAG: U$1.16 (DIAG), U$3.3 (PB1)
GND: C1.1, C2.1, C4.2, C5.2, C7.2, C8.-, JP1.5, LED.C, R1.2, R2.2, U$1.3 (DIR), U$1.5 (OSC), U$1.7 (AGND), U$1.12 (MS1), U$1.13 (MS0), U$1.19 (STEP), U$1.21 (PGND), U$1.26 (ENABLE), U$1.PAD, U$3.14 (GND), U$4.P$3 (GND)
LED: R3.2, U$3.5 (PB2)
MISO: U$3.8 (PA5), U$4.MISO
MOTOR_RESET: U$1.27 (RESET), U$3.2 (PB0)
unnamed: C3.1, U$1.22 (VCP)
unnamed: R1.1, U$1.1 (SENSA)
unnamed: R2.1, U$1.14 (SENSB)
unnamed: LED.A, R3.1
unnamed: C5.1, U$1.20 (VREG)
unnamed: C6.1, U$1.24 (CP2)
unnamed: C6.2, U$1.23 (CP1)
RESET: U$3.4 (PB3), U$4.RESET
SCK: U$1.9 (SCK), U$3.11 (PA2)
SCL/SCK: U$3.9 (PA4), U$4.P$4 (SCL)
SDA/MOSI: U$3.7 (PA6), U$4.P$2 (SDA)
SDI: U$1.6 (SDI), U$3.13 (PA0)
SDO: U$1.17 (SDO), U$3.12 (PA1)
STRN: U$1.2 (STRN), U$3.10 (PA3)
VCC: C1.2, C2.2, C4.1, U$1.8 (VREF), U$1.10 (VDD), U$3.1 (VCC), U$4.P$1 (+5V)
VIN: C3.2, C7.1, C8.+, JP1.6, U$1.15 (VBBB), U$1.28 (VBBA)

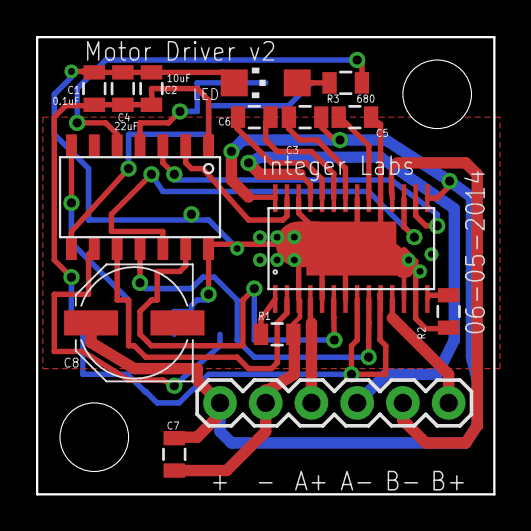
[picture p87: board A4980.brd from above]

Board: 2 copper layers, 25.4 x 25.4 mm, 16 parts (0 on the bottom side), 25 nets.
