modulolabs/pcb/uC/Leonardo/Leonardo.brd

## EAGLE design uC/Leonardo/Leonardo.brd (2014-06-20)

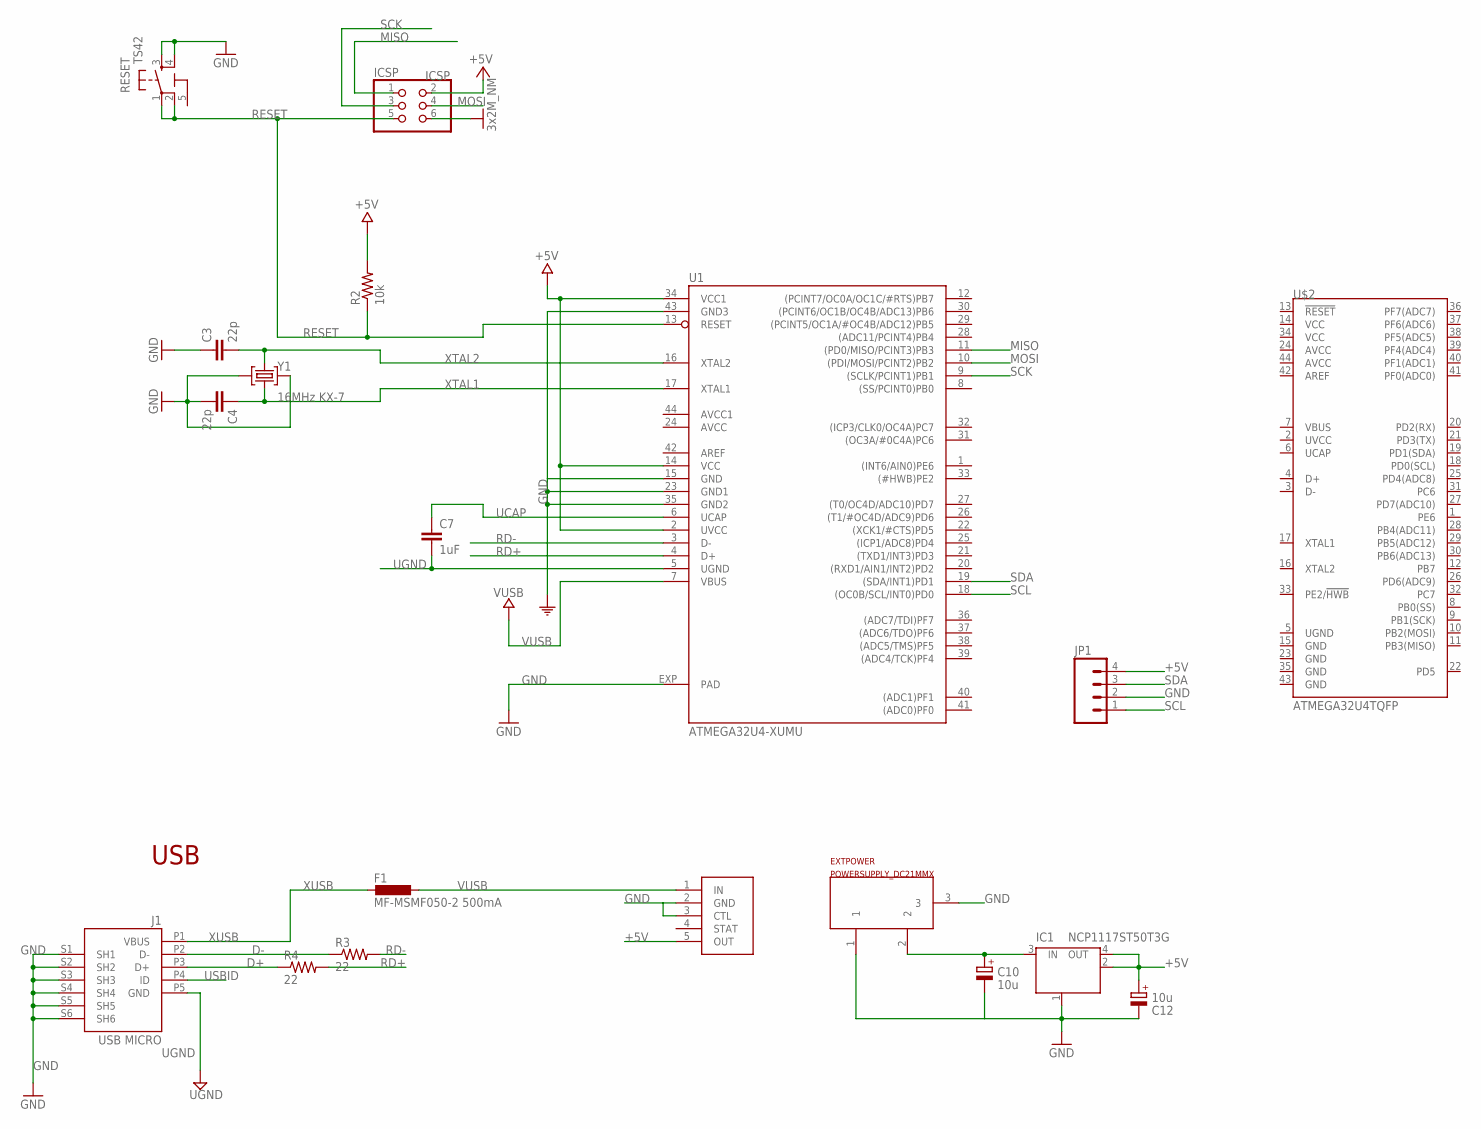
[picture p88: schematic Leonardo.sch]

Parts:
C3, C4: 22p; C0603-ROUND
C7: 1uF; C0603-ROUND
C10, C12: 10u; SMC_B
EXTPOWER: POWERSUPPLY_DC21MMX; POWERSUPPLY_DC-21MM
F1: MF-MSMF050-2 500mA; L1812
IC1: NCP1117ST50T3G; SOT223
ICSP: ICSP; 2X03
J1: USB MICRO; CON2_USB_MICRO_B_AT
JP1: M04LOCK; 1X04_LOCK
R2: 10k; 1206
R3, R4: 22; 0805
RESET: TS42
U1: ATMEGA32U4-XUMU; QFN44ML7X7
U$1: LTC4411; SOT23-5
U$2: ATMEGA32U4TQFP; SPARKFUN-DIGITALIC_TQFP44
Y1: 16MHz KX-7; CRYSTAL-3.2-2.5

Connections:
5-GND: RESET.5 (5-GND)
+5V: C12.+, IC1.2 (OUT), IC1.4 (OUT), ICSP.2, JP1.4, R2.2, U1.2 (UVCC), U1.14 (VCC), U1.34 (VCC1), U$1.5 (OUT)
AREF: U1.42 (AREF)
AVCC: U1.24 (AVCC)
AVCC1: U1.44 (AVCC1)
D+: J1.P3 (D+), R4.1
D-: J1.P2 (D-), R3.1
GND: C3.1, C4.2, C10.-, C12.-, EXTPOWER.1, EXTPOWER.3, IC1.1 (GND/ADJ), ICSP.6, J1.S1 (SH1), J1.S2 (SH2), J1.S3 (SH3), J1.S4 (SH4), J1.S5 (SH5), J1.S6 (SH6), JP1.2, RESET.3, RESET.4, U1.15 (GND), U1.23 (GND1), U1.35 (GND2), U1.43 (GND3), U1.EXP (PAD), U$1.2 (GND), U$1.3 (CTL), Y1.2 (GND), Y1.4 (GND)
MISO: ICSP.1, U1.11 ((PD0/MISO/PCINT3)PB3)
MOSI: ICSP.4, U1.10 ((PDI/MOSI/PCINT2)PB2)
RD+: R4.2, U1.4 (D+)
RD-: R3.2, U1.3 (D-)
RESET: ICSP.5, R2.1, RESET.1, RESET.2, U1.13 (RESET)
SCK: ICSP.3, U1.9 ((SCLK/PCINT1)PB1)
SCL: JP1.1, U1.18 ((OC0B/SCL/INT0)PD0)
SDA: JP1.3, U1.19 ((SDA/INT1)PD1)
UCAP: C7.1, U1.6 (UCAP)
UGND: C7.2, J1.P5 (GND), U1.5 (UGND)
USBID: J1.P4 (ID)
VIN: C10.+, EXTPOWER.2, IC1.3 (IN)
VUSB: F1.1, U1.7 (VBUS), U$1.1 (IN)
XTAL1: C4.1, U1.17 (XTAL1), Y1.1 (C1)
XTAL2: C3.2, U1.16 (XTAL2), Y1.3 (C2)
XUSB: F1.2, J1.P1 (VBUS)

Notes on the sheet:
USB

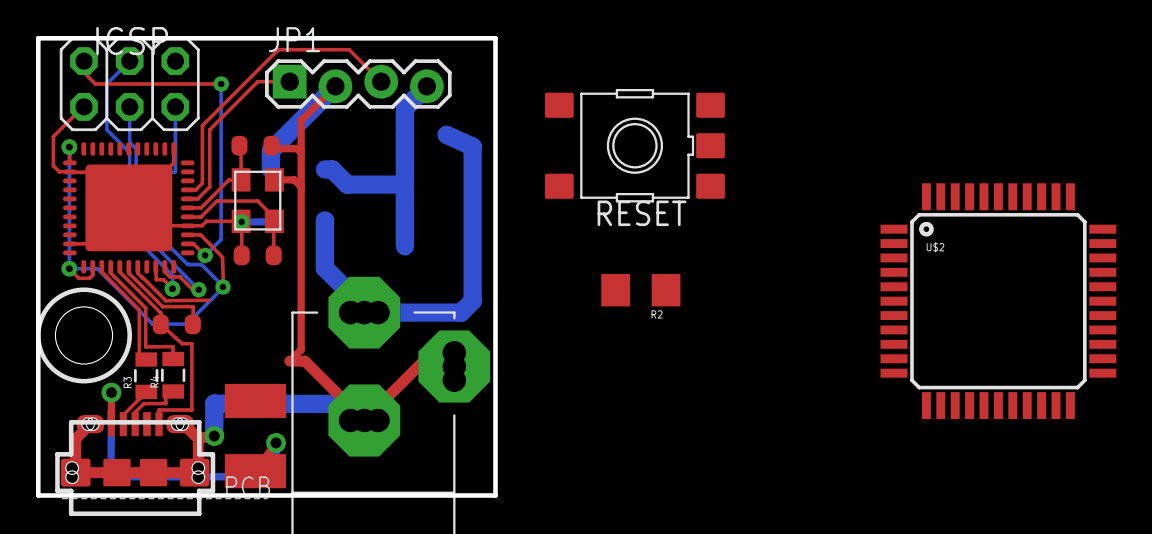
[picture p89: board Leonardo.brd from above]

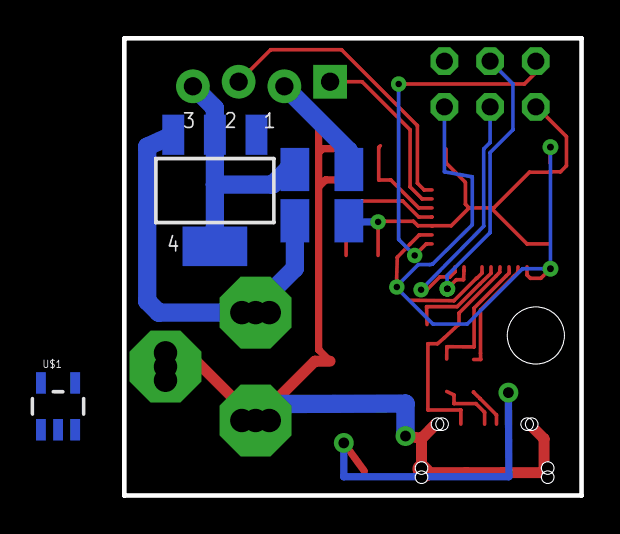
[picture p90: board Leonardo.brd from below]

Board: 2 copper layers, 25.4 x 25.4 mm, 19 parts (4 on the bottom side), 19 nets.
