modulolabs/pcb/Stepper/DRV8834/DRV8834.brd

## EAGLE design Stepper/DRV8834/DRV8834.brd (2014-06-20)

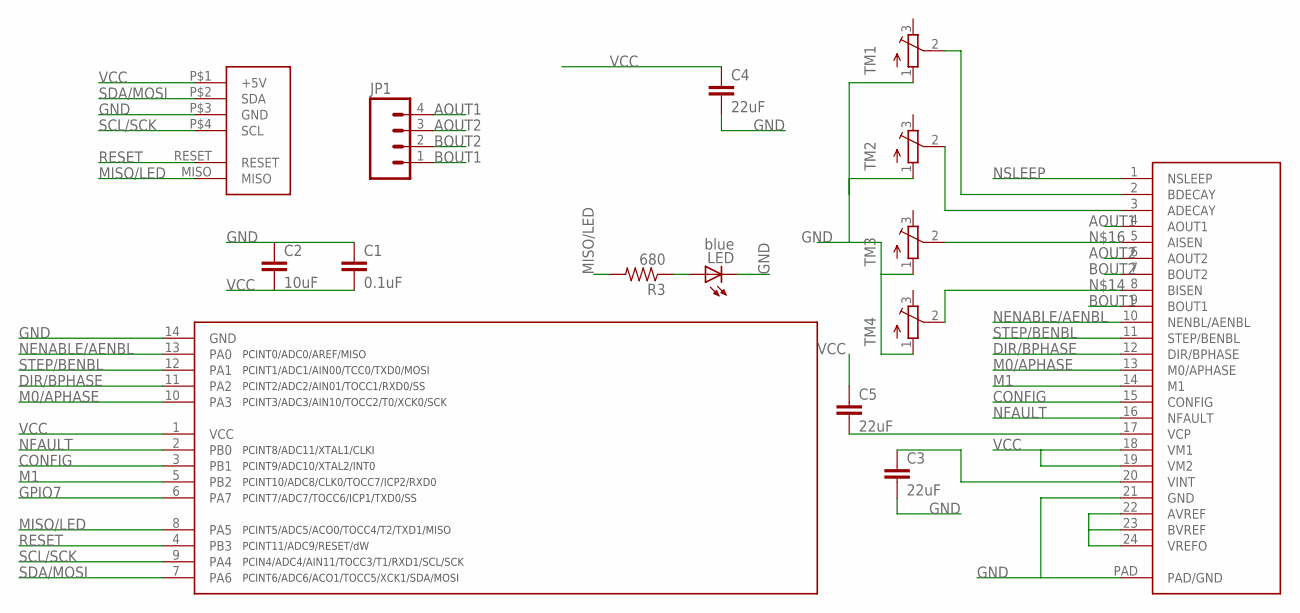
[picture p91: schematic DRV8834.sch]

Parts:
C1: 0.1uF; 0805
C2: 10uF; 0805
C3, C4, C5: 22uF; 0805
JP1: M04SCREW_LOCK; SCREWTERMINAL-3.5MM-4_LOCK
LED: blue; CHIPLED_1206
R3: 680; 0805
TM1, TM2, TM3, TM4: TRIMPOTTC33X; TC33X
U$1: DRV8834; HTSSOP-24
U$3: TINY841; SOIC14
U$4: FOOTPRINT

Connections:
AOUT1: JP1.4, U$1.4 (AOUT1)
AOUT2: JP1.3, U$1.6 (AOUT2)
BOUT1: JP1.1, U$1.9 (BOUT1)
BOUT2: JP1.2, U$1.7 (BOUT2)
CONFIG: U$1.15 (CONFIG), U$3.3 (PB1)
DIR/BPHASE: U$1.12 (DIR/BPHASE), U$3.11 (PA2)
GND: C1.1, C2.1, C3.2, C4.2, LED.C, TM1.1 (A), TM2.1 (A), TM3.1 (A), TM4.1 (A), U$1.21 (GND), U$1.PAD (PAD/GND), U$3.14 (GND), U$4.P$3 (GND)
GPIO7: U$3.6 (PA7)
M0/APHASE: U$1.13 (M0/APHASE), U$3.10 (PA3)
M1: U$1.14 (M1), U$3.5 (PB2)
MISO/LED: R3.2, U$3.8 (PA5), U$4.MISO
unnamed: LED.A, R3.1
unnamed: C5.2, U$1.17 (VCP)
unnamed: TM1.2 (S), U$1.2 (BDECAY)
unnamed: TM2.2 (S), U$1.3 (ADECAY)
unnamed: C3.1, U$1.20 (VINT)
unnamed: U$1.22 (AVREF), U$1.23 (BVREF), U$1.24 (VREFO)
unnamed: TM4.2 (S), U$1.8 (BISEN)
unnamed: TM3.2 (S), U$1.5 (AISEN)
NENABLE/AENBL: U$1.10 (NENBL/AENBL), U$3.13 (PA0)
NFAULT: U$1.16 (NFAULT), U$3.2 (PB0)
NSLEEP: U$1.1 (NSLEEP)
RESET: U$3.4 (PB3), U$4.RESET
SCL/SCK: U$3.9 (PA4), U$4.P$4 (SCL)
SDA/MOSI: U$3.7 (PA6), U$4.P$2 (SDA)
STEP/BENBL: U$1.11 (STEP/BENBL), U$3.12 (PA1)
VCC: C1.2, C2.2, C4.1, C5.1, U$1.18 (VM1), U$1.19 (VM2), U$3.1 (VCC), U$4.P$1 (+5V)

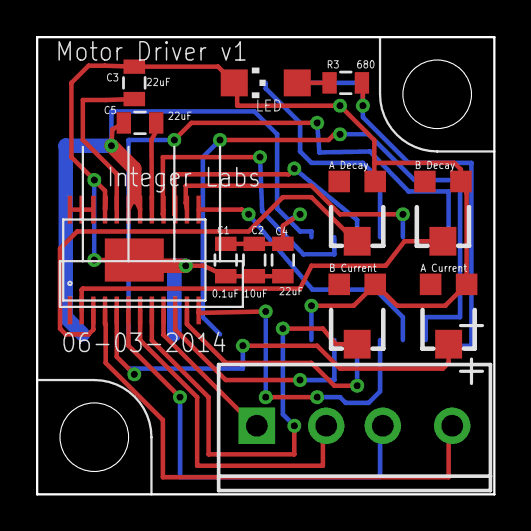
[picture p92: board DRV8834.brd from above]

Board: 2 copper layers, 25.4 x 25.4 mm, 15 parts (1 on the bottom side), 25 nets.
